kiu/kha/kha-bgt-subrack/kha-bgt-main/README.md

# kha-bgt-main

Main Power Preset Module

## Parts

Use [kha-bgt-generic-base](../../kha-bgt-misc/kha-bgt-generic-base/) as base

## Photos

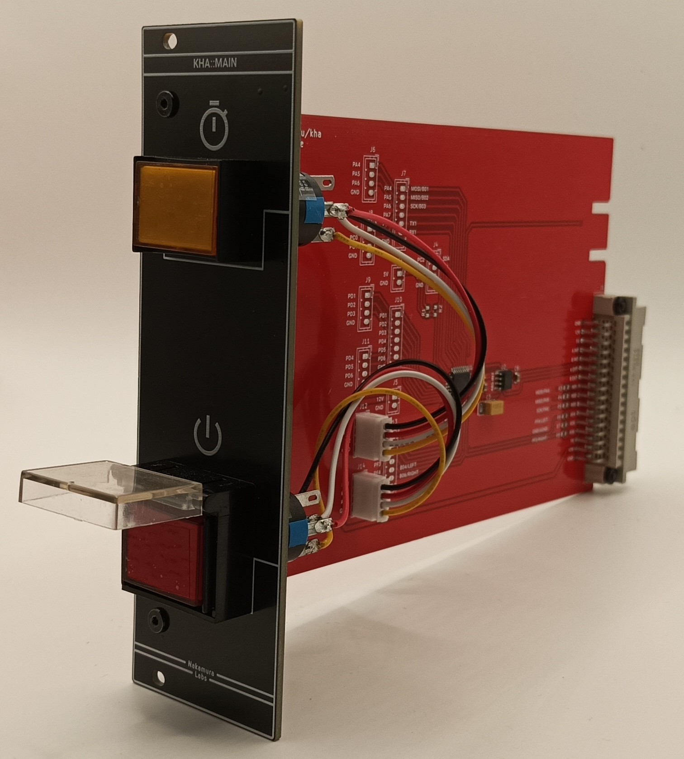
[picture p24: kha-bgt-subrack/kha-bgt-main/kha-bgt-main-photo.jpg]
