kiu/kha/kha-nodes/kha-relay-2x3/README.md

# kha-relay-2x3

Mains Power Relay

## Photos

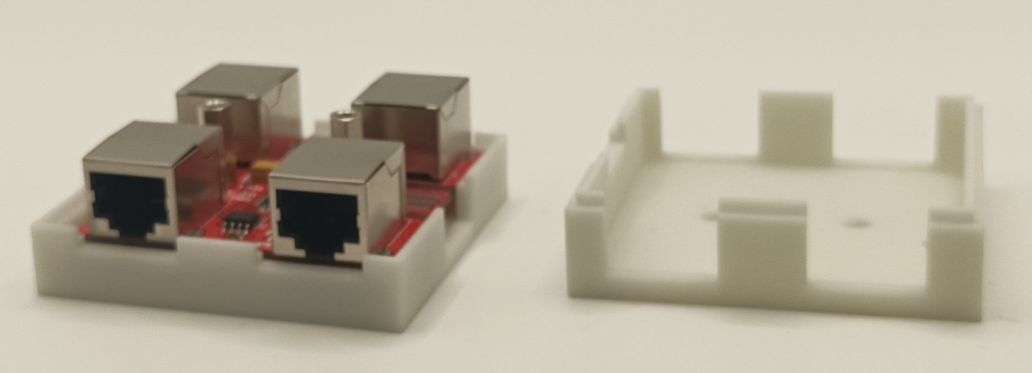
[picture p25: kha-nodes/kha-relay-2x3/kha-relay-2x3-node/kha-relay-2x3-node-photo.jpg]
