kiu/kha/kha-bgt-misc/kha-bgt-pwr/README.md

# kha-bgt-pwr

Subrack Power Module

Generating 5V out of 12V bus supply

## Photos

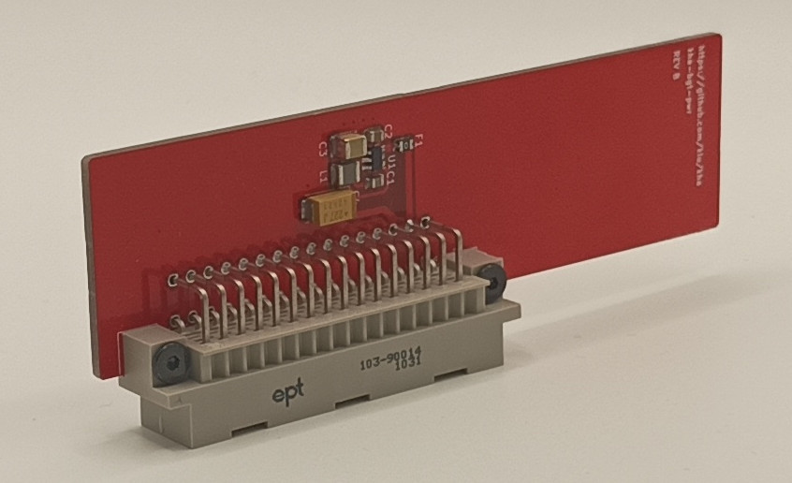
[picture p26: kha-bgt-misc/kha-bgt-pwr/kha-bgt-pwr-photo.jpg]


## Render

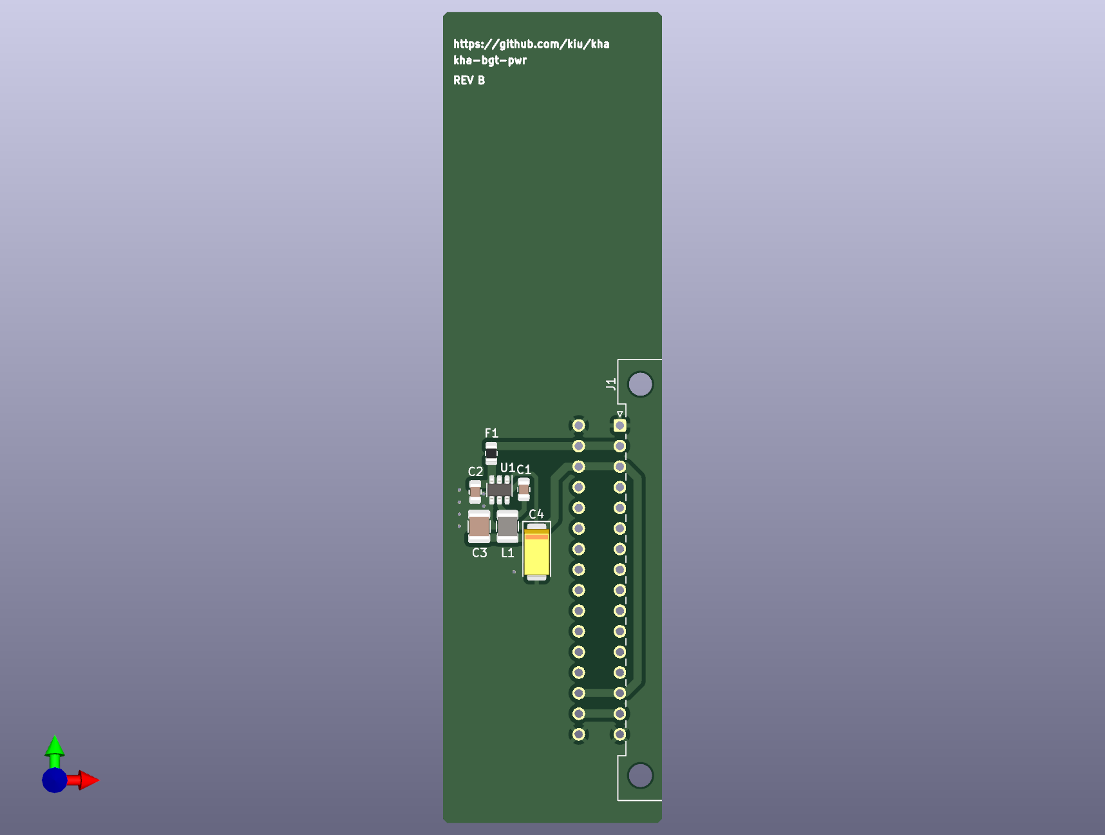
[picture p27: kha-bgt-misc/kha-bgt-pwr/kha-bgt-pwr-render-front.png]


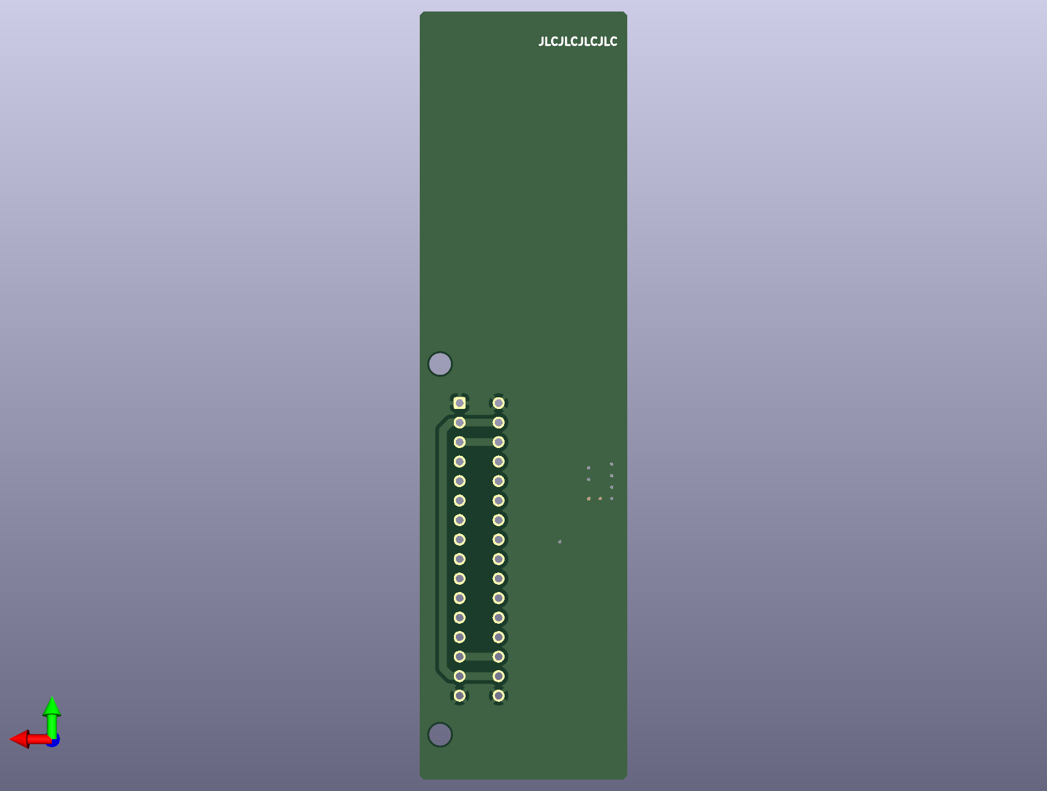
[picture p28: kha-bgt-misc/kha-bgt-pwr/kha-bgt-pwr-render-back.png]
