kiu/kha/kha-bgt-rack/kha-bgt-backplane/README.md

# kha-bgt-backplane

Rack backplane

## Photos

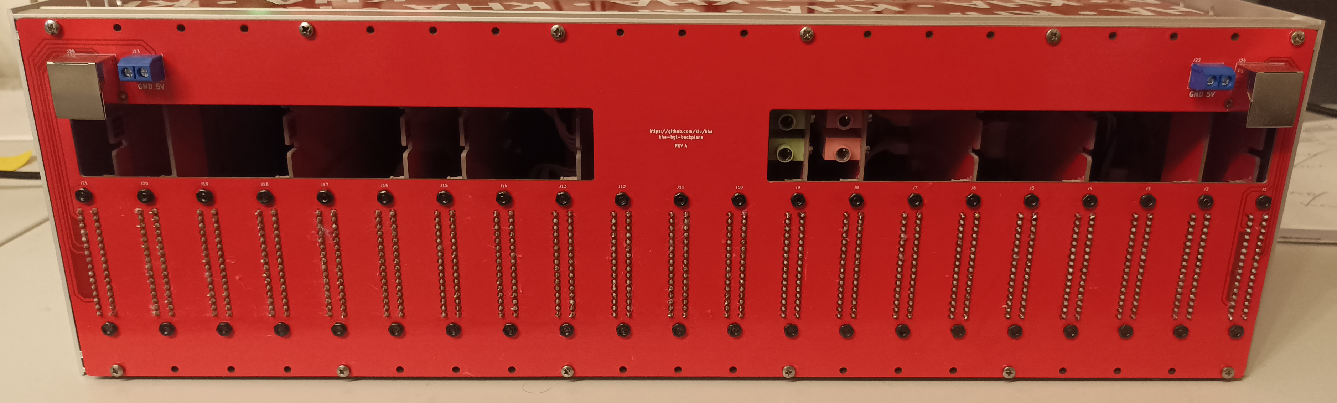
[picture p29: kha-bgt-rack/kha-bgt-backplane/kha-bgt-backplane-photo.jpg]


## Render

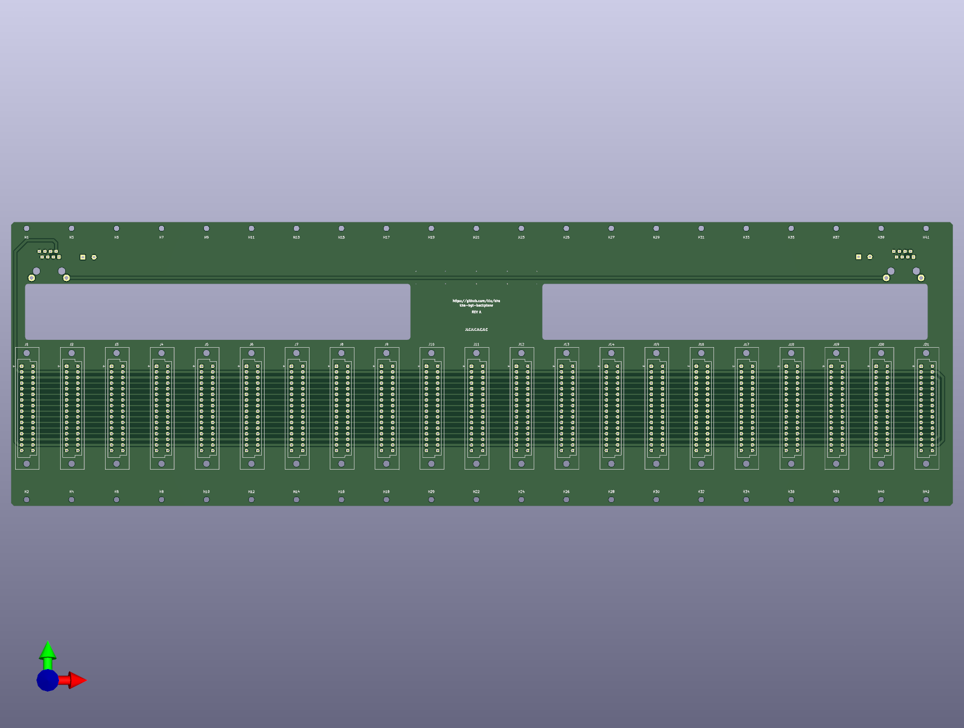
[picture p30: kha-bgt-rack/kha-bgt-backplane/kha-bgt-backplane-render-front.png]


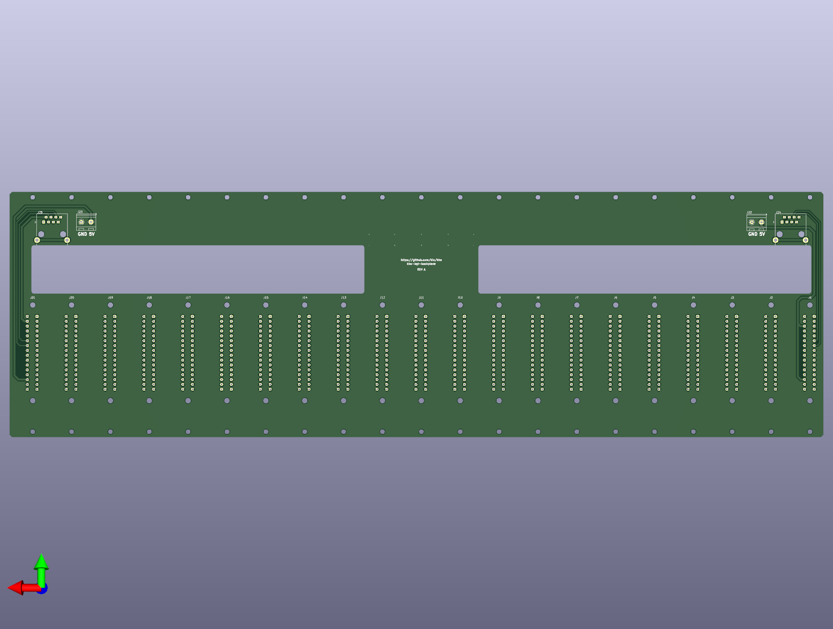
[picture p31: kha-bgt-rack/kha-bgt-backplane/kha-bgt-backplane-render-back.png]


## Todo

- Remove 2nd internal RS-485 bus, never used
- Add silkscreen for bus
- Use bigger font for silkscreen
- Add screw terminal for 12V injection
- Built-in 5V stepdown on backplane
- Backplane should be symmetric
