kiu/kha/kha-nodes/kha-pwr-rj45/README.md

# kha-pwr-rj45

POE Power Inject

## Photos

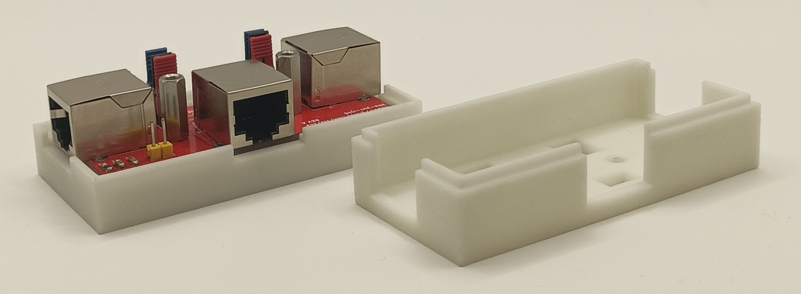
[picture p32: kha-nodes/kha-pwr-rj45/kha-pwr-rj45-photo.jpg]


## Render

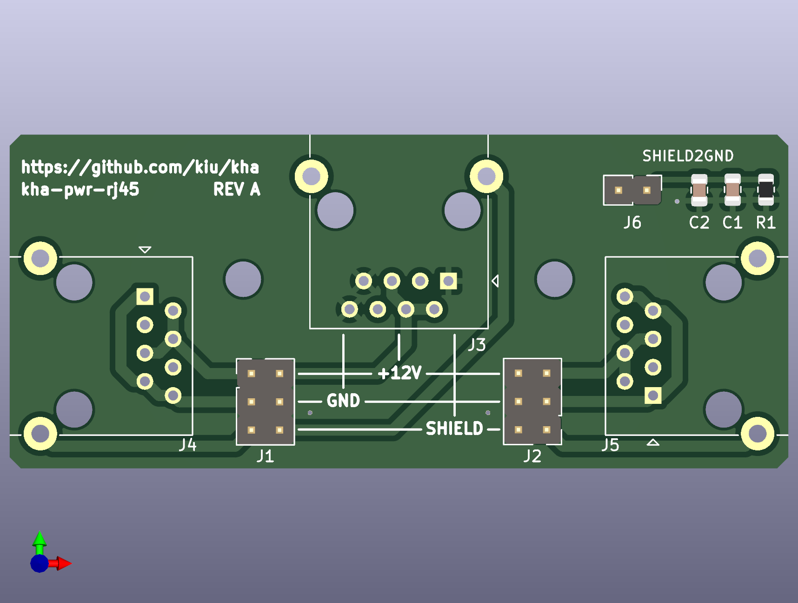
[picture p33: kha-nodes/kha-pwr-rj45/kha-pwr-rj45-render-front.png]


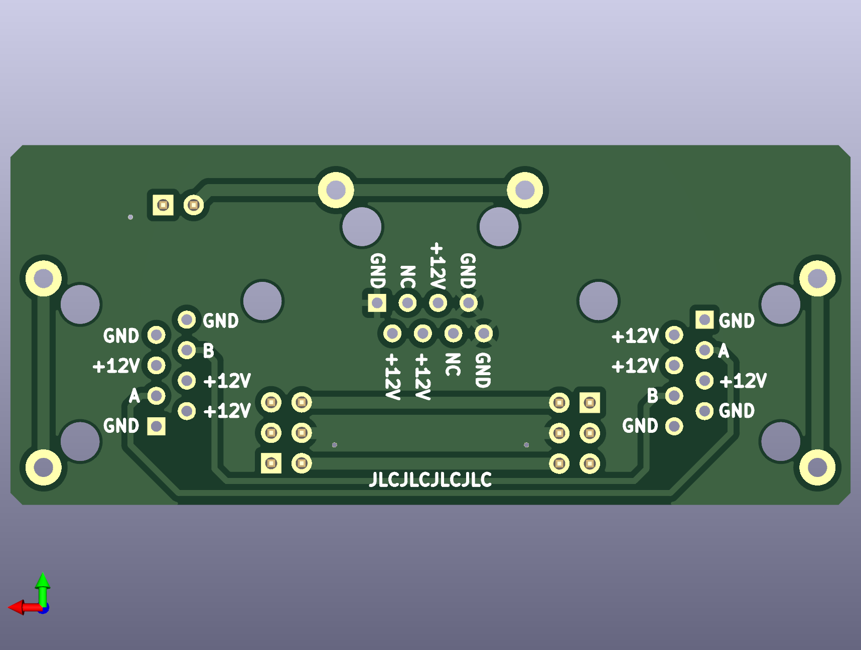
[picture p34: kha-nodes/kha-pwr-rj45/kha-pwr-rj45-render-back.png]
