kiu/kha/kha-nodes/kha-pwr-terminal/README.md

# kha-pwr-terminal

Screw Terminal Power Inject

## Photos

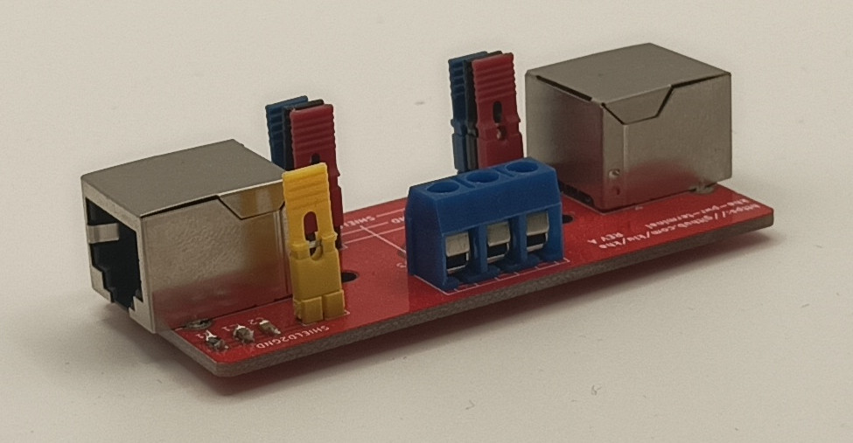
[picture p35: kha-nodes/kha-pwr-terminal/kha-pwr-terminal-photo.jpg]


## Render

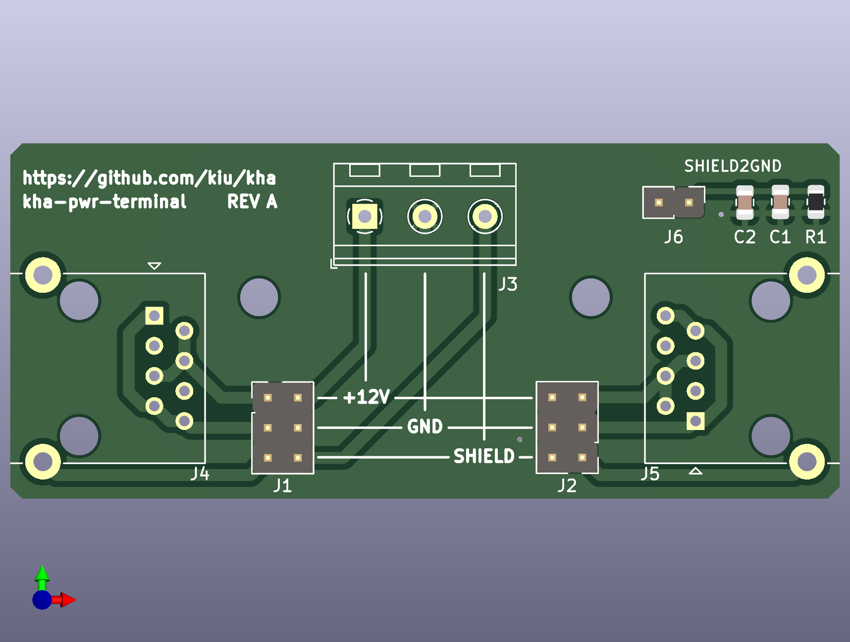
[picture p36: kha-nodes/kha-pwr-terminal/kha-pwr-terminal-render-front.png]


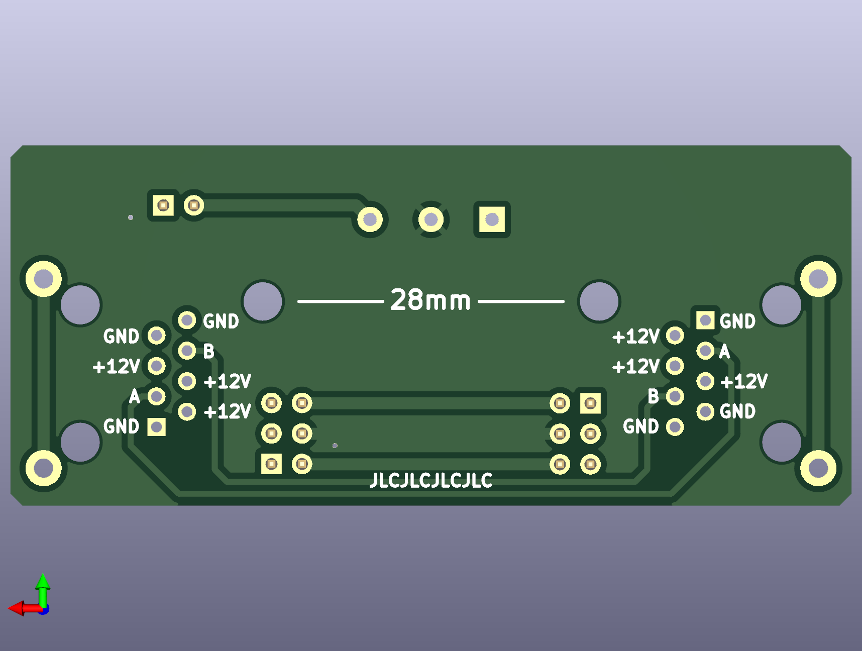
[picture p37: kha-nodes/kha-pwr-terminal/kha-pwr-terminal-render-back.png]
