kiu/kha/tools/kha-userrow/README.md

# kha-userrow

Device provisioning information stored in AVR64 userrow

- Board Type
- Board Revision
- Device Address
- Device Group
- Data (currently unused)
