kiu/kha/kha-bgt-rack/kha-bgt-cover/README.md

# kha-bgt-cover

Rack Cover Plate

## Render

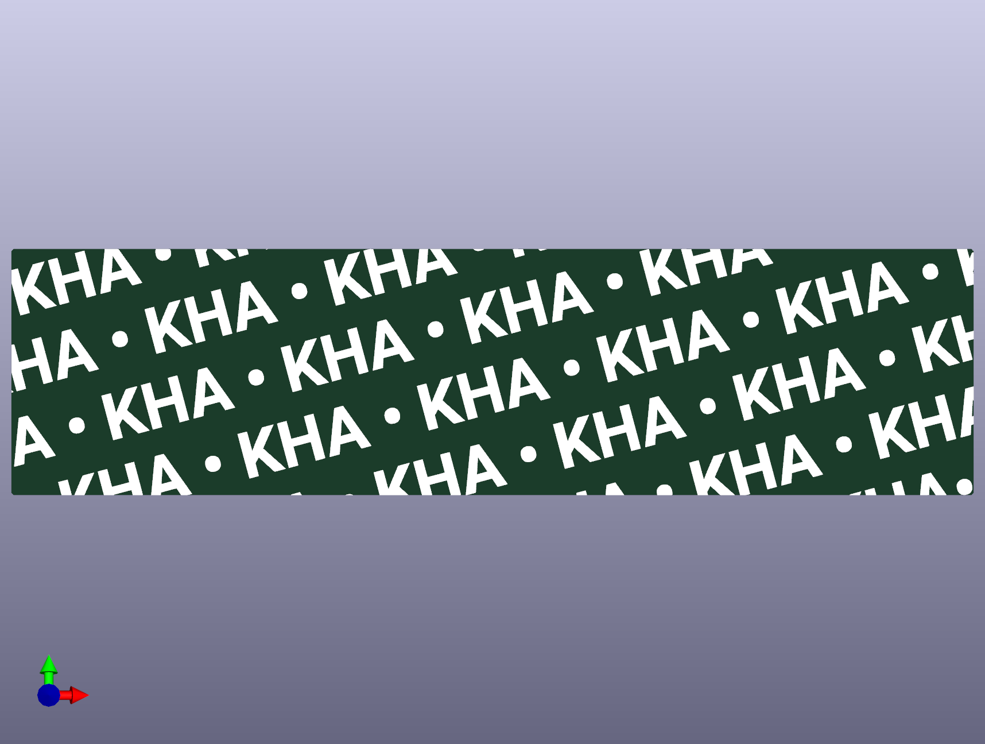
[picture p38: kha-bgt-rack/kha-bgt-cover/kha-bgt-cover-render-front.png]


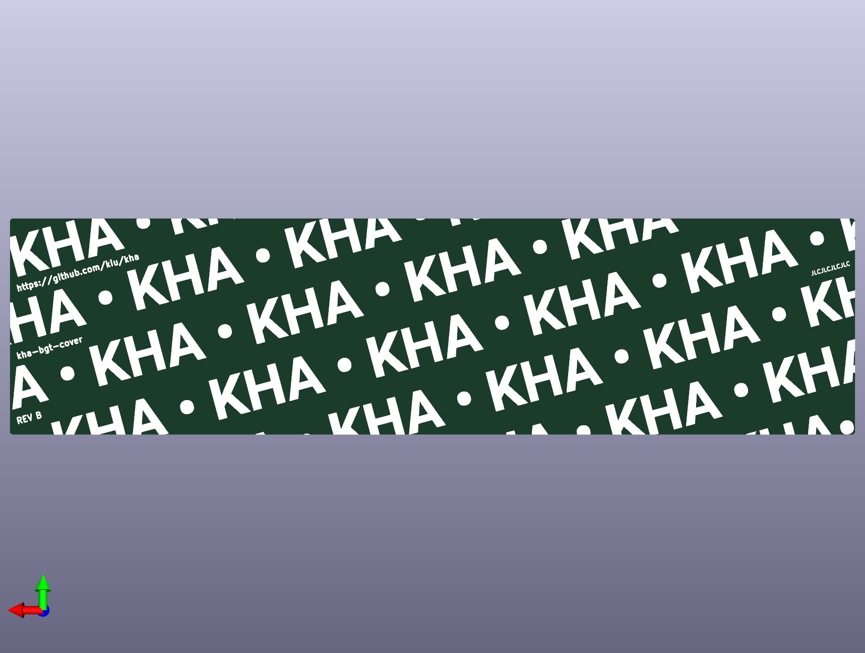
[picture p39: kha-bgt-rack/kha-bgt-cover/kha-bgt-cover-render-back.png]
