kiu/kha/kha-bgt-rack/kha-bgt-spacer/README.md

# kha-bgt-spacer

Rack Spacer

Double stacked spacer needed to provide z space for backplane

## Render

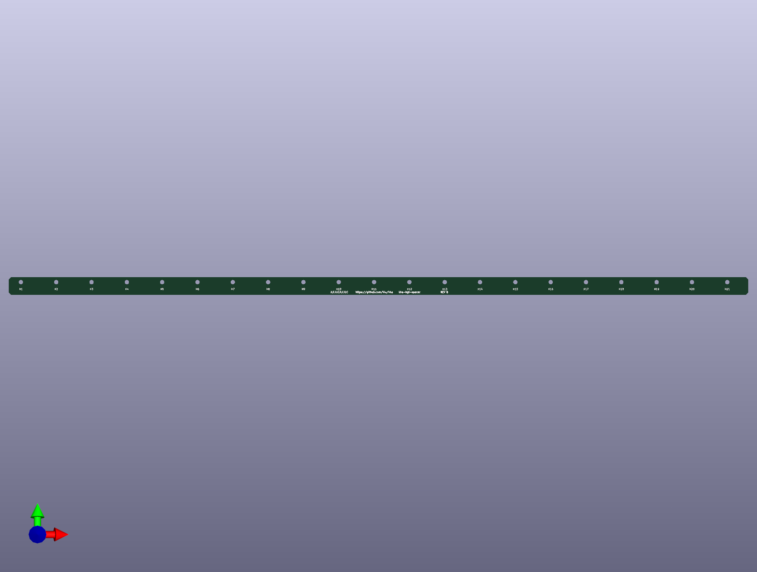
[picture p40: kha-bgt-rack/kha-bgt-spacer/kha-bgt-spacer-render-front.png]


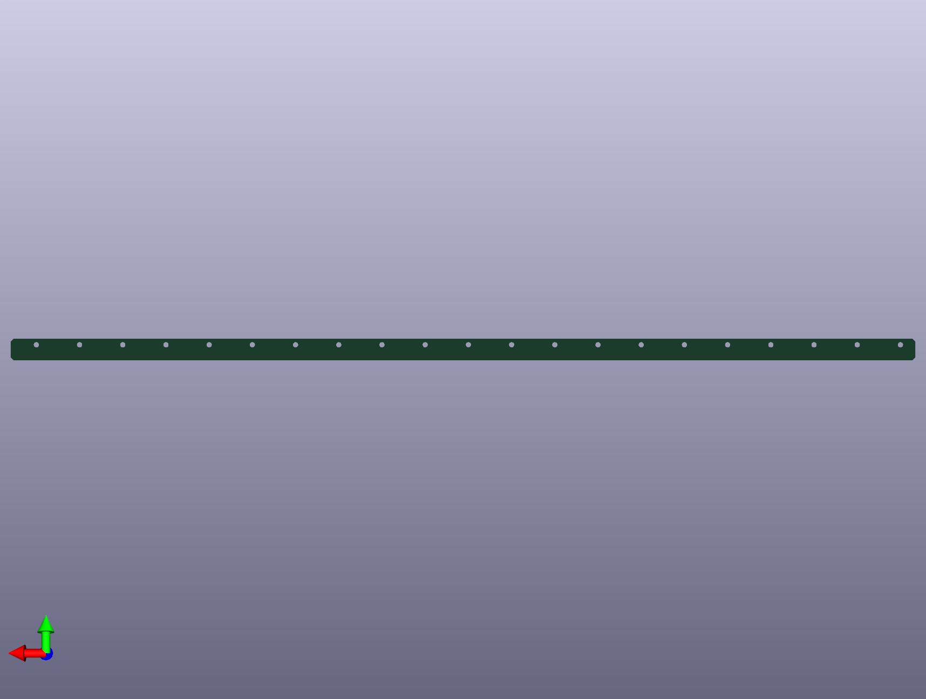
[picture p41: kha-bgt-rack/kha-bgt-spacer/kha-bgt-spacer-render-back.png]
