kiu/kha/kha-bgt-misc/kha-bgt-generic-4btn-sub/README.md

# kha-bgt-generic-4btn-sub

Generic Four Push Button Mounting PCB

## Render

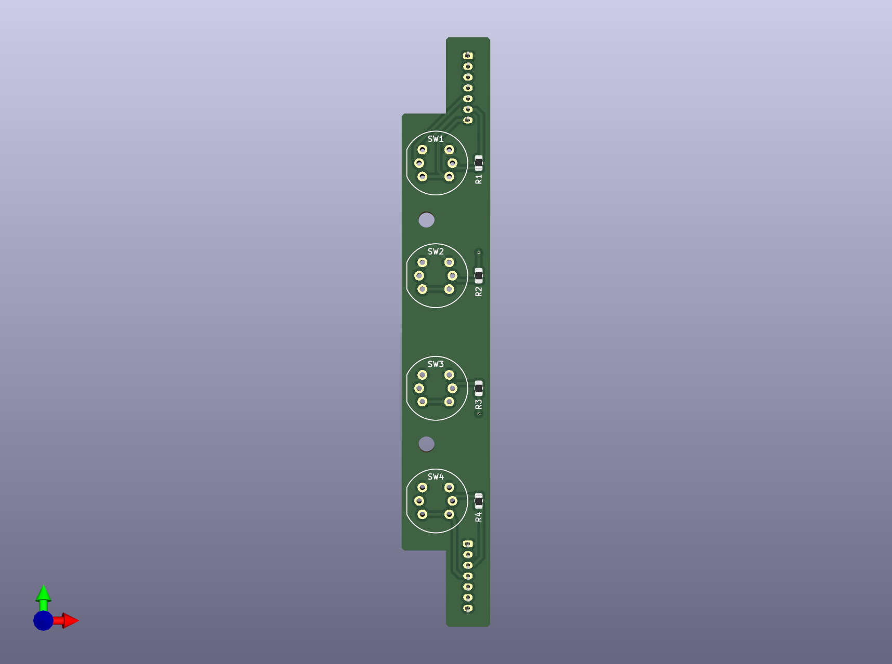
[picture p42: kha-bgt-misc/kha-bgt-generic-4btn-sub/kha-bgt-generic-4btn-sub-render-front.png]


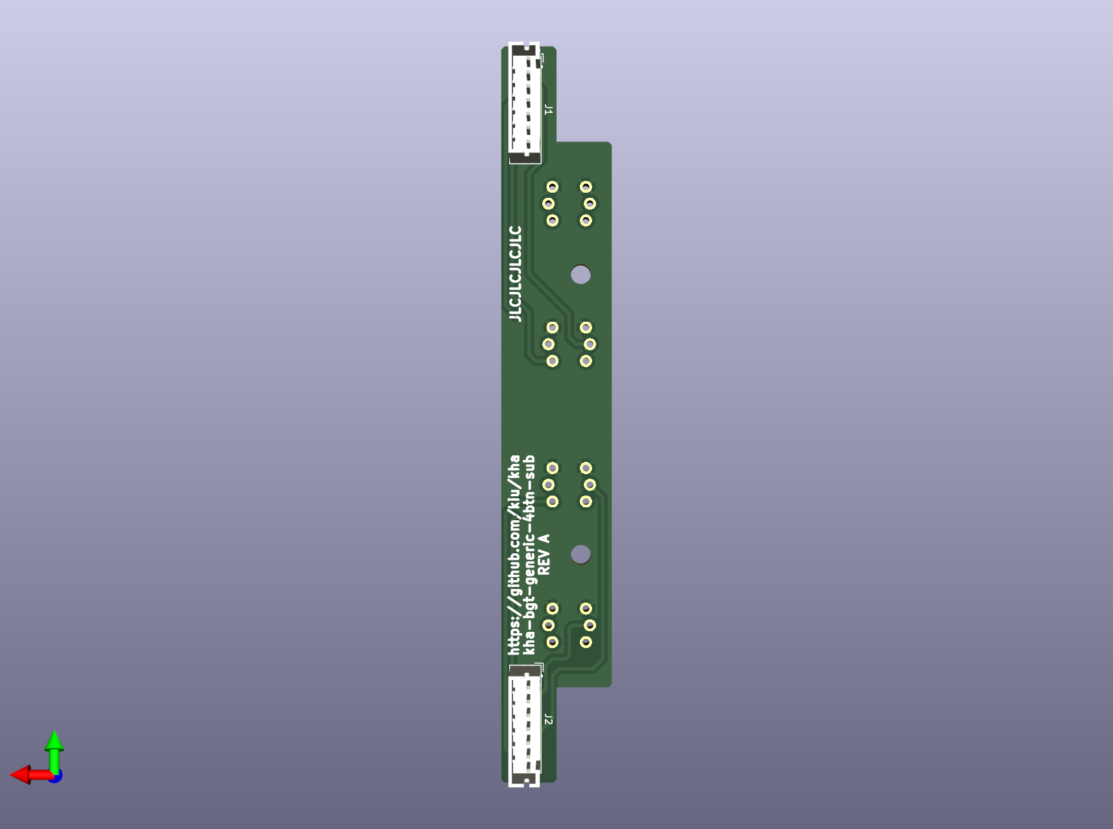
[picture p43: kha-bgt-misc/kha-bgt-generic-4btn-sub/kha-bgt-generic-4btn-sub-render-back.png]
