kiu/kha/kha-bgt-misc/kha-bgt-generic-rotary-encoder/README.md

# kha-bgt-generic-rotary-encoder

Generic Single Rotary Encoder Mounting PCB

## Render

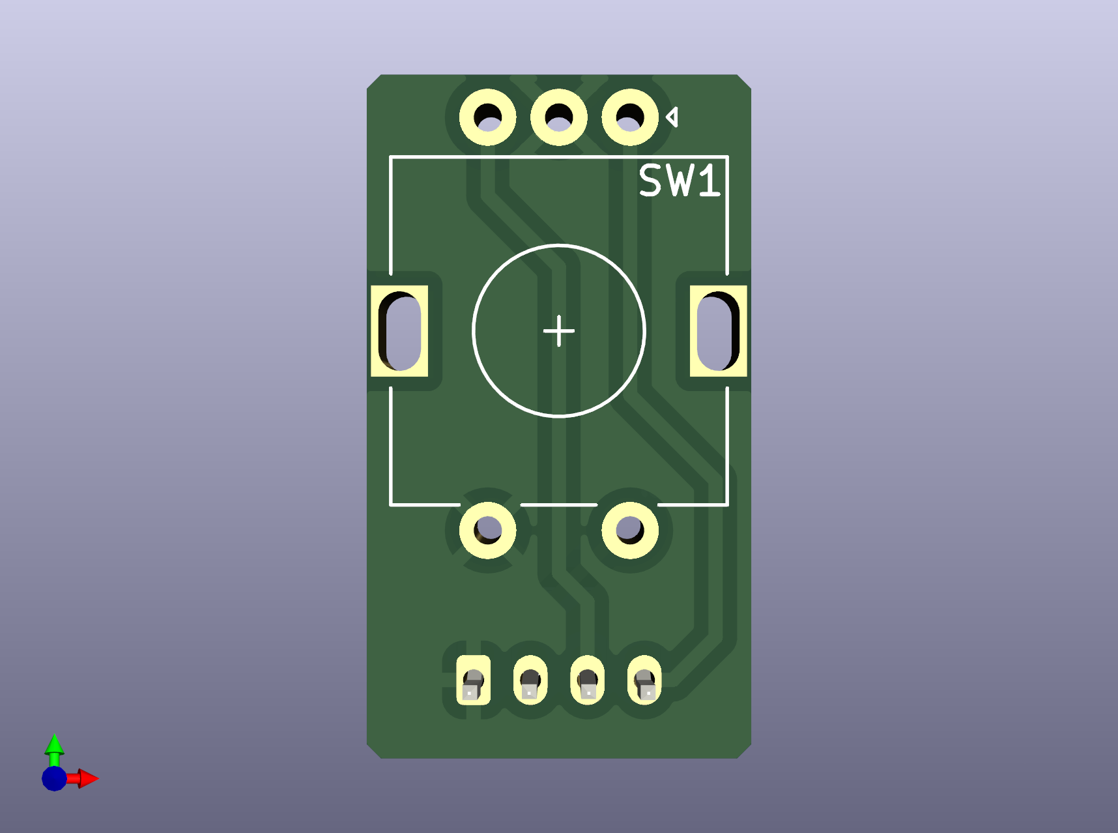
[picture p44: kha-bgt-misc/kha-bgt-generic-rotary-encoder/kha-bgt-generic-rotary-encoder-render-front.png]


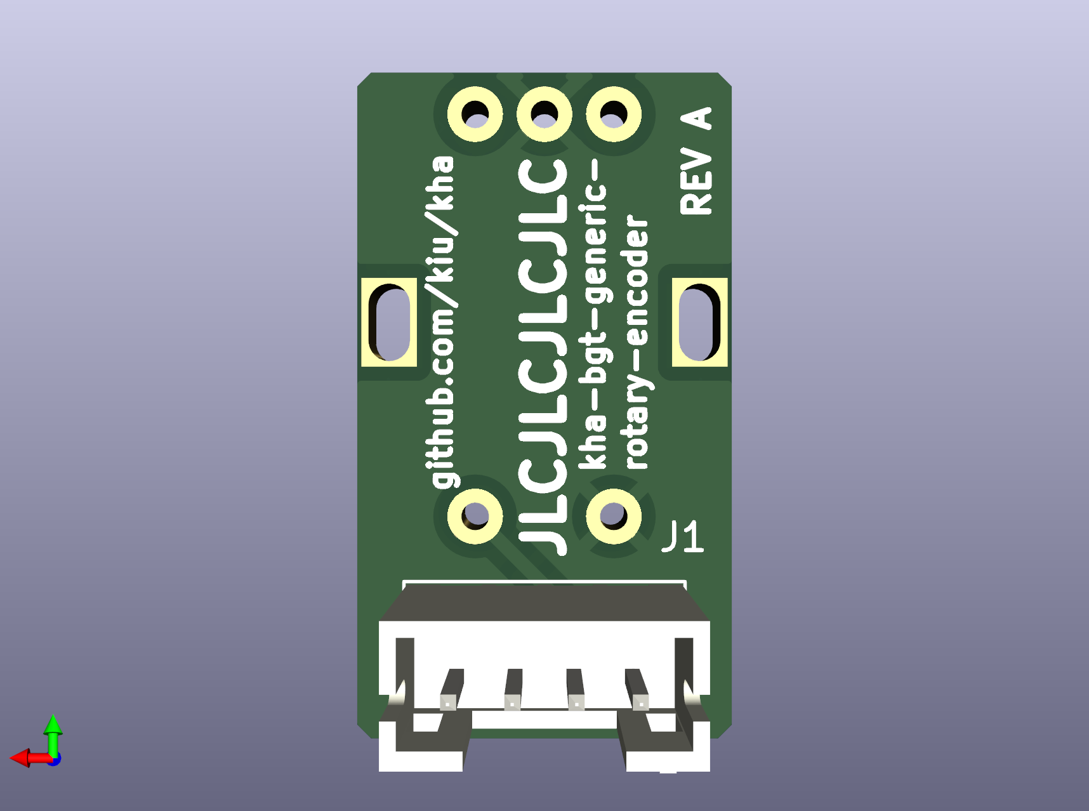
[picture p45: kha-bgt-misc/kha-bgt-generic-rotary-encoder/kha-bgt-generic-rotary-encoder-render-back.png]
