kiu/kha/kha-bgt-misc/kha-bgt-template/README.md

# kha-bgt-template

Templates to be used for creating custom front panels and base pcbs

## Render

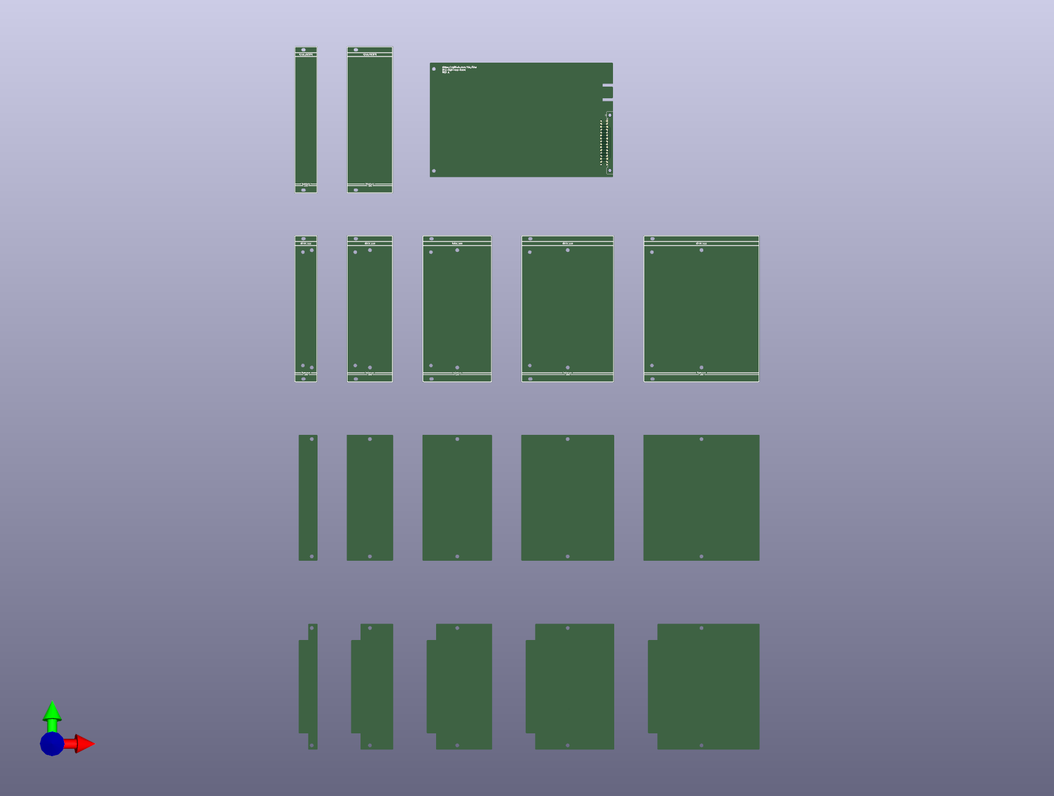
[picture p46: kha-bgt-misc/kha-bgt-template/kha-bgt-template-render-front.png]


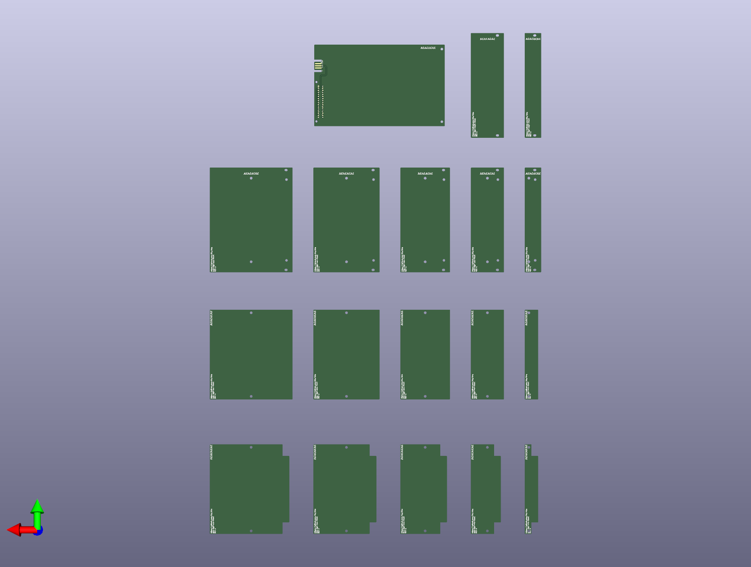
[picture p47: kha-bgt-misc/kha-bgt-template/kha-bgt-template-render-back.png]
