kiu/kha/kha-bgt-subrack/kha-bgt-strip/kha-bgt-strip-front/README.md

# kha-bgt-strip-front

LED Strip Front Panel

## Render

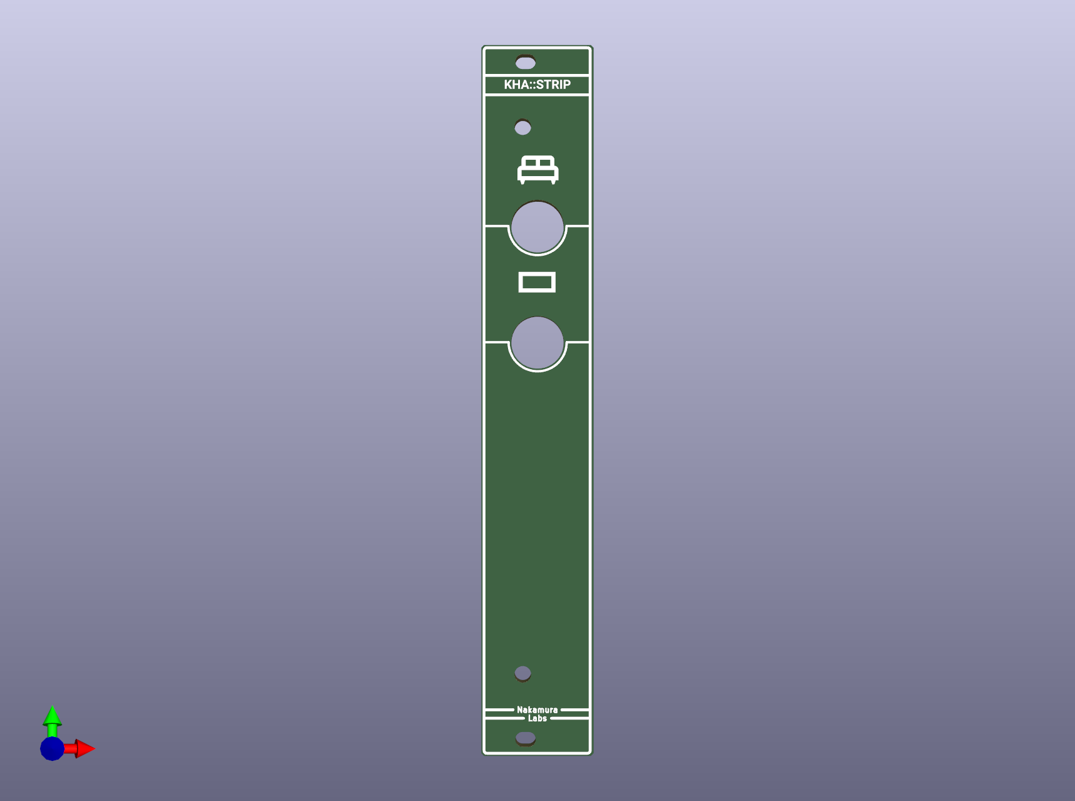
[picture p48: kha-bgt-subrack/kha-bgt-strip/kha-bgt-strip-front/kha-bgt-strip-front-render-front.png]


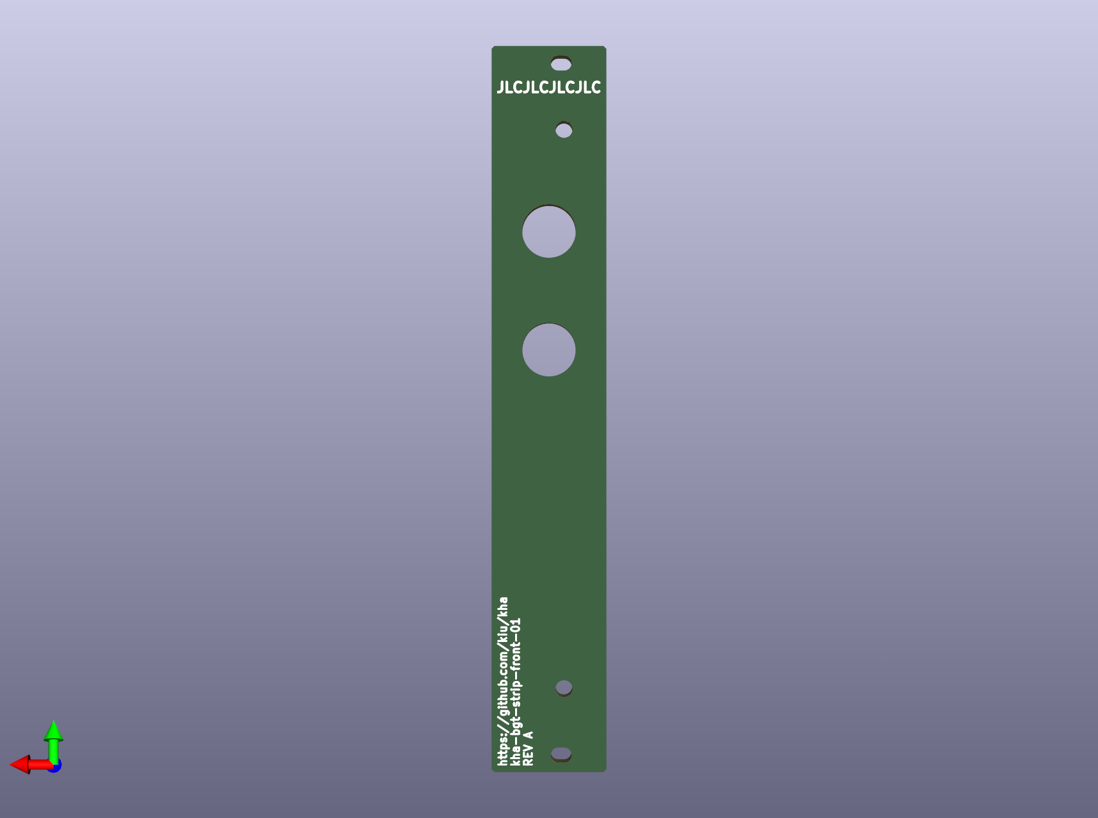
[picture p49: kha-bgt-subrack/kha-bgt-strip/kha-bgt-strip-front/kha-bgt-strip-front-render-back.png]
