kiu/kha/kha-bgt-subrack/kha-bgt-power/kha-bgt-power-front-04-desk/README.md

# kha-bgt-power-front-04-desk

Mains Power Switching Module Front Panel Use Case 04

## Render

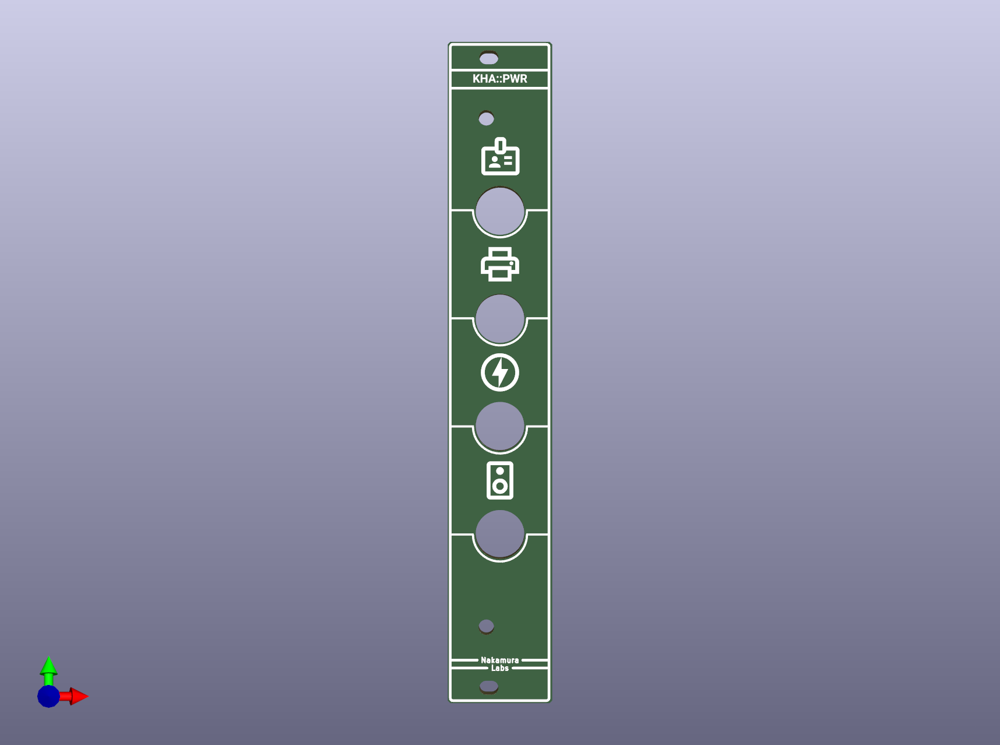
[picture p50: kha-bgt-subrack/kha-bgt-power/kha-bgt-power-front-04-desk/kha-bgt-power-front-04-desk-render-front.png]


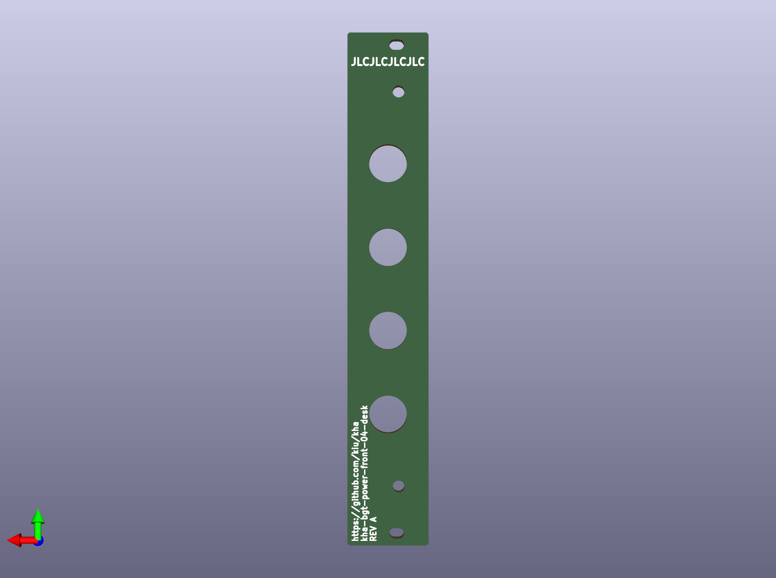
[picture p51: kha-bgt-subrack/kha-bgt-power/kha-bgt-power-front-04-desk/kha-bgt-power-front-04-desk-render-back.png]
