kiu/kha/kha-bgt-subrack/kha-bgt-audio/kha-bgt-audio-base/README.md

# kha-bgt-audio-base

Audio Switching Module Base

- 2x TRS (back)
- 1x TRS (front)
- 1x Bluetooth

## Render

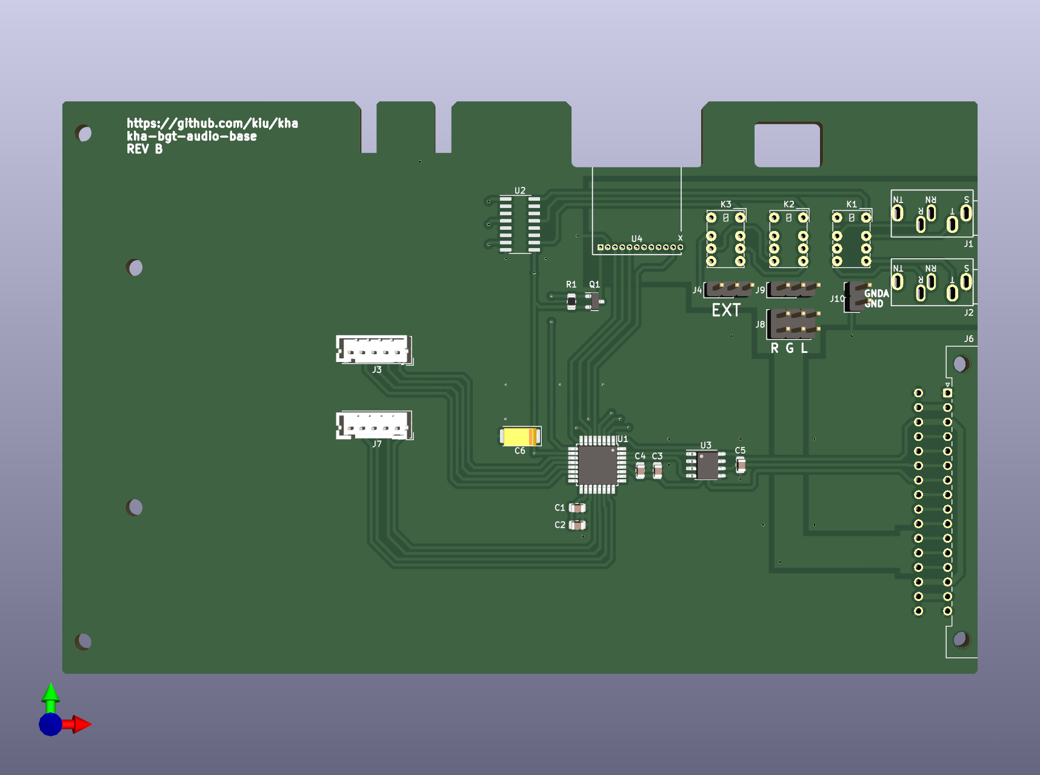
[picture p52: kha-bgt-subrack/kha-bgt-audio/kha-bgt-audio-base/kha-bgt-audio-base-render-front.png]


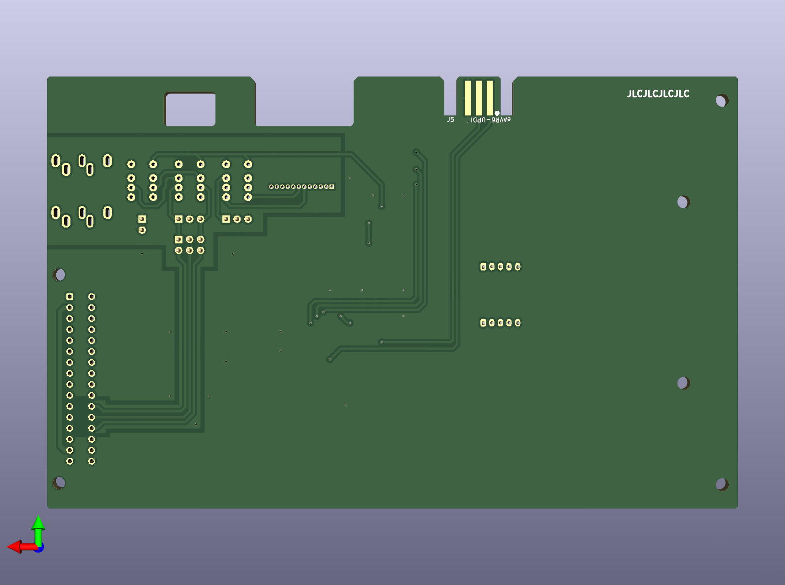
[picture p53: kha-bgt-subrack/kha-bgt-audio/kha-bgt-audio-base/kha-bgt-audio-base-render-back.png]
