kiu/kha/kha-bgt-subrack/kha-bgt-audio/kha-bgt-audio-front-in/README.md

# kha-bgt-audio-front-in

Audio Switching Module Input Front Panel

## Render

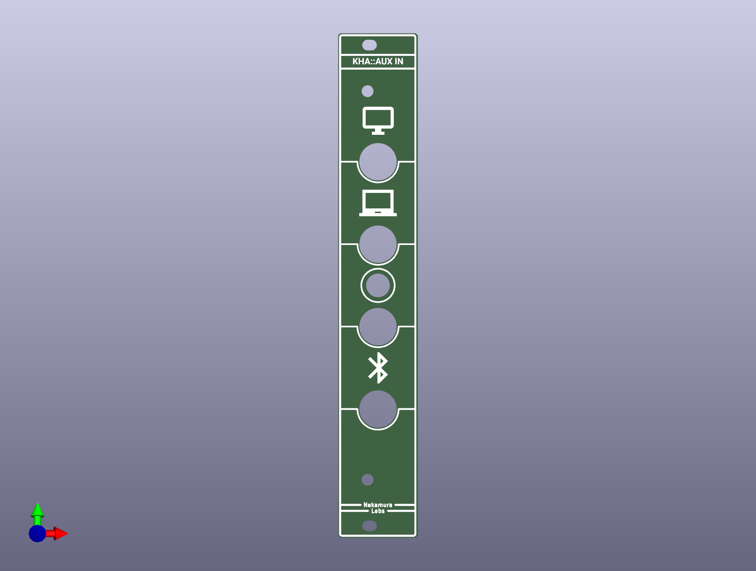
[picture p54: kha-bgt-subrack/kha-bgt-audio/kha-bgt-audio-front-in/kha-bgt-audio-front-in-render-front.png]


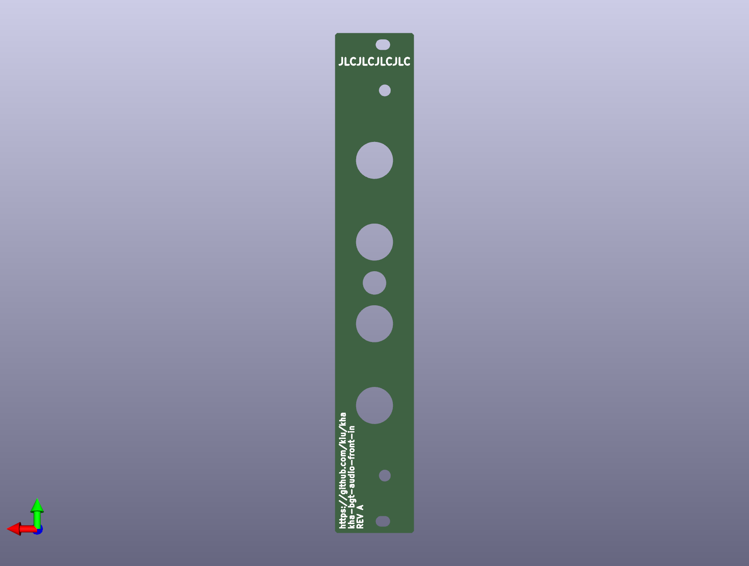
[picture p55: kha-bgt-subrack/kha-bgt-audio/kha-bgt-audio-front-in/kha-bgt-audio-front-in-render-back.png]
