kiu/kha/kha-bgt-subrack/kha-bgt-audio/kha-bgt-audio-front-out/README.md

# kha-bgt-audio-front-out

Audio Switching Module Output Front Panel

## Render

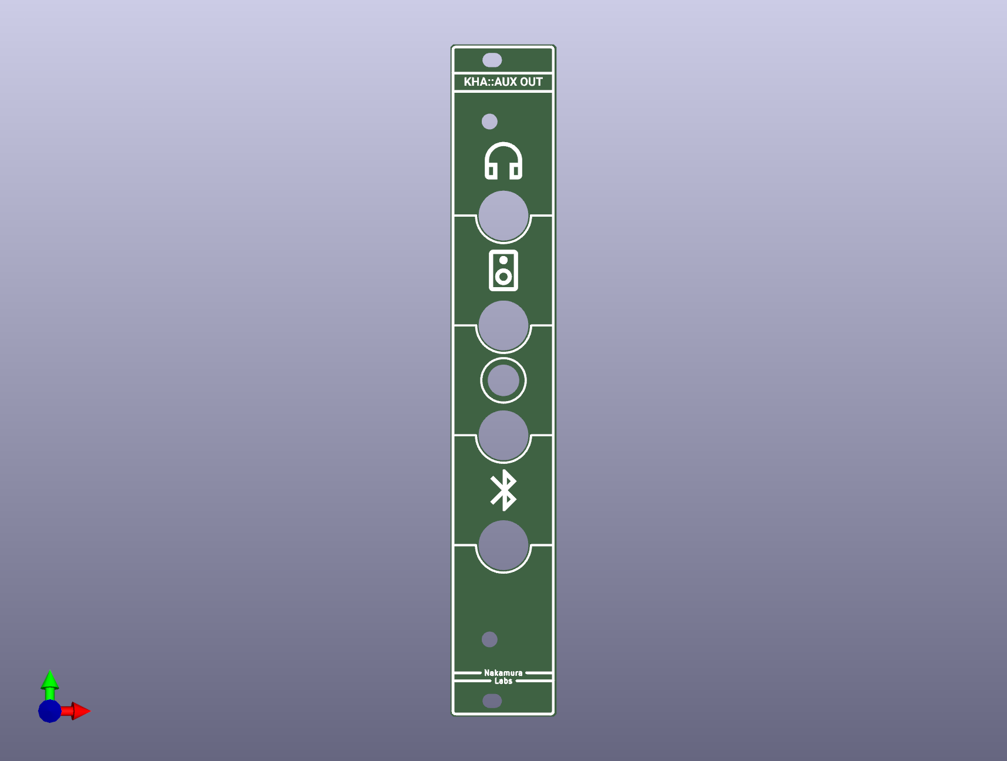
[picture p56: kha-bgt-subrack/kha-bgt-audio/kha-bgt-audio-front-out/kha-bgt-audio-front-out-render-front.png]


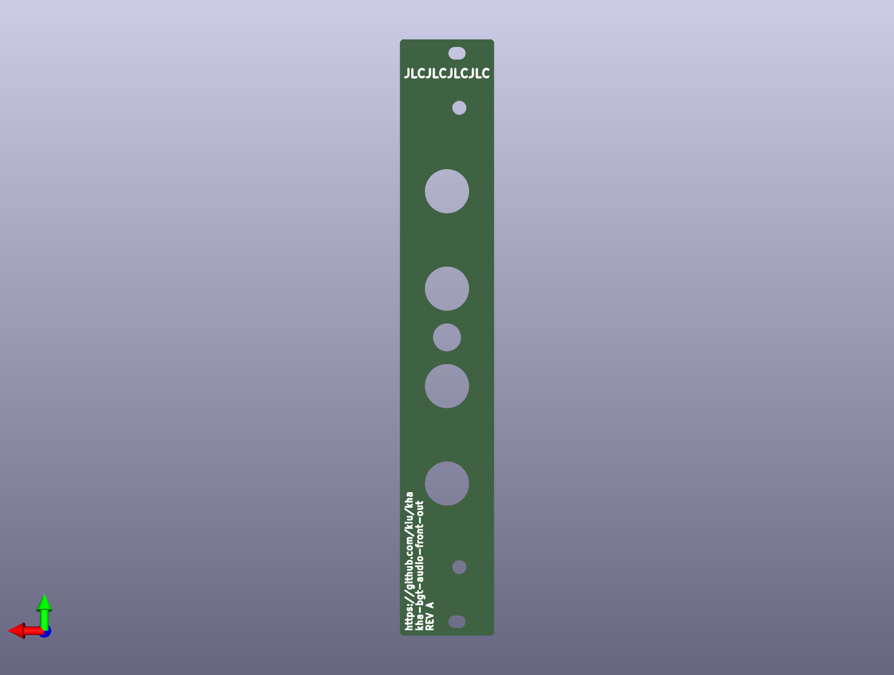
[picture p57: kha-bgt-subrack/kha-bgt-audio/kha-bgt-audio-front-out/kha-bgt-audio-front-out-render-back.png]
