kiu/kha/kha-bgt-subrack/kha-bgt-audio/kha-bgt-audio-sub/README.md

# kha-bgt-audio-sub

Audio Switching Module Four Push Button and TRS Mounting PCB

## Render

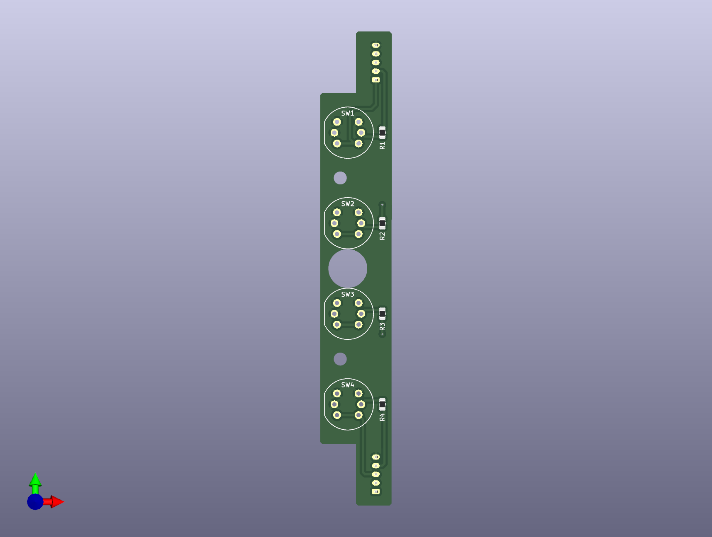
[picture p58: kha-bgt-subrack/kha-bgt-audio/kha-bgt-audio-sub/kha-bgt-audio-sub-render-front.png]


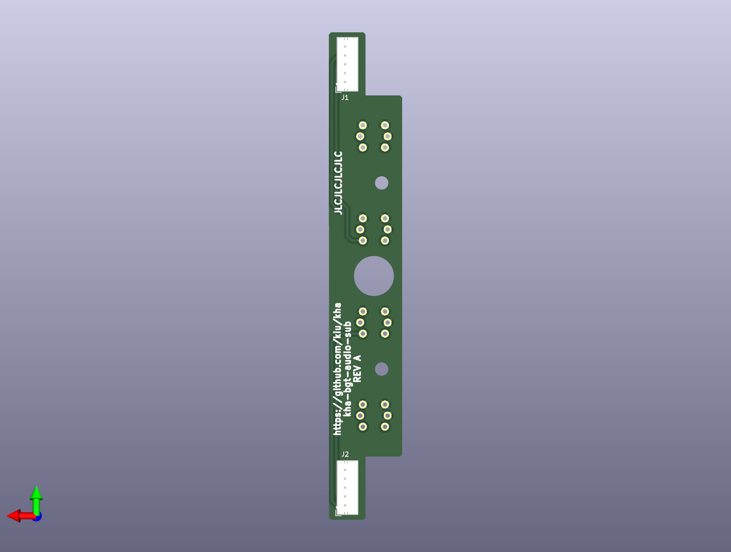
[picture p59: kha-bgt-subrack/kha-bgt-audio/kha-bgt-audio-sub/kha-bgt-audio-sub-render-back.png]
