kiu/kha/kha-bgt-subrack/kha-bgt-main/kha-bgt-main-front/README.md

# kha-bgt-main-front

Main Power Preset Module Front Panel

## Render

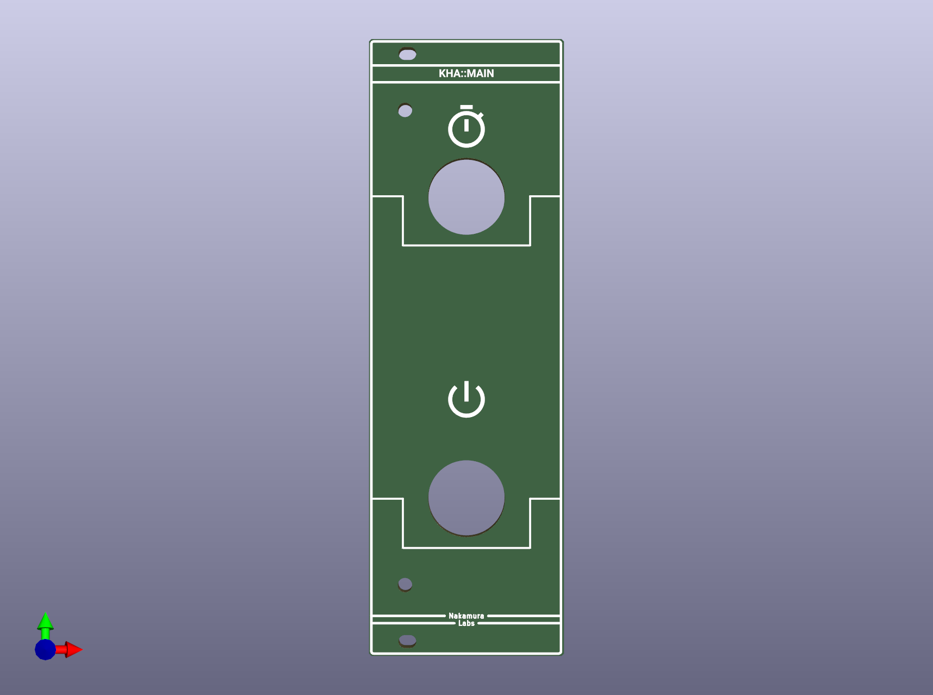
[picture p60: kha-bgt-subrack/kha-bgt-main/kha-bgt-main-front/kha-bgt-main-front-render-front.png]


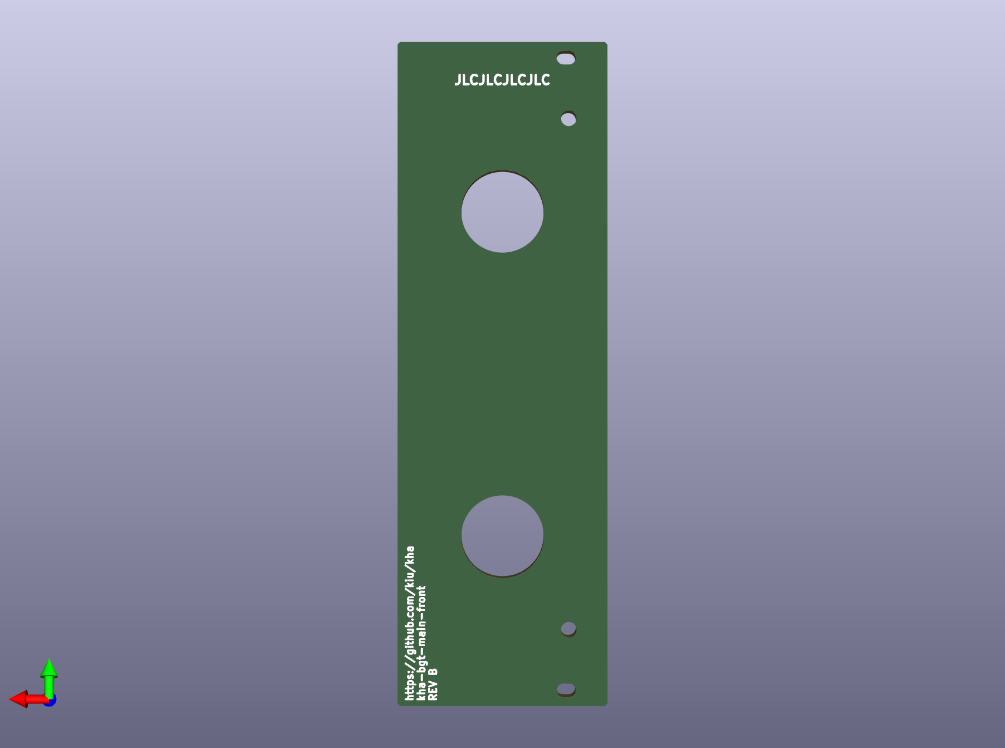
[picture p61: kha-bgt-subrack/kha-bgt-main/kha-bgt-main-front/kha-bgt-main-front-render-back.png]
