kiu/kha/kha-bgt-subrack/kha-bgt-power/kha-bgt-power-base/README.md

# kha-bgt-power-base

Mains Power Switching Module Base

## Render

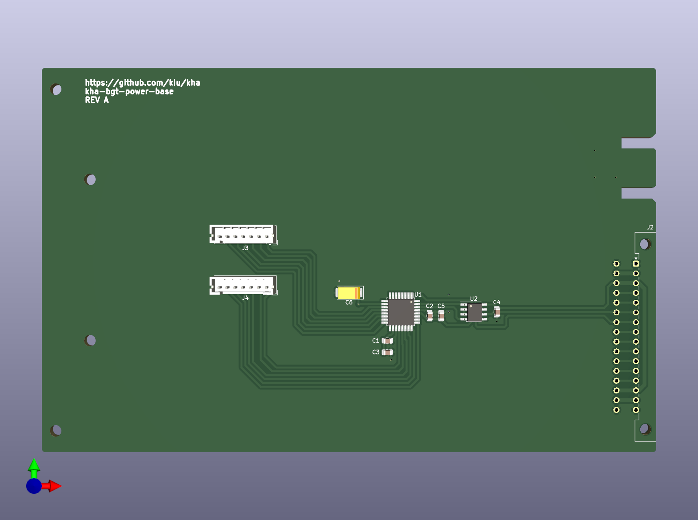
[picture p62: kha-bgt-subrack/kha-bgt-power/kha-bgt-power-base/kha-bgt-power-base-render-front.png]


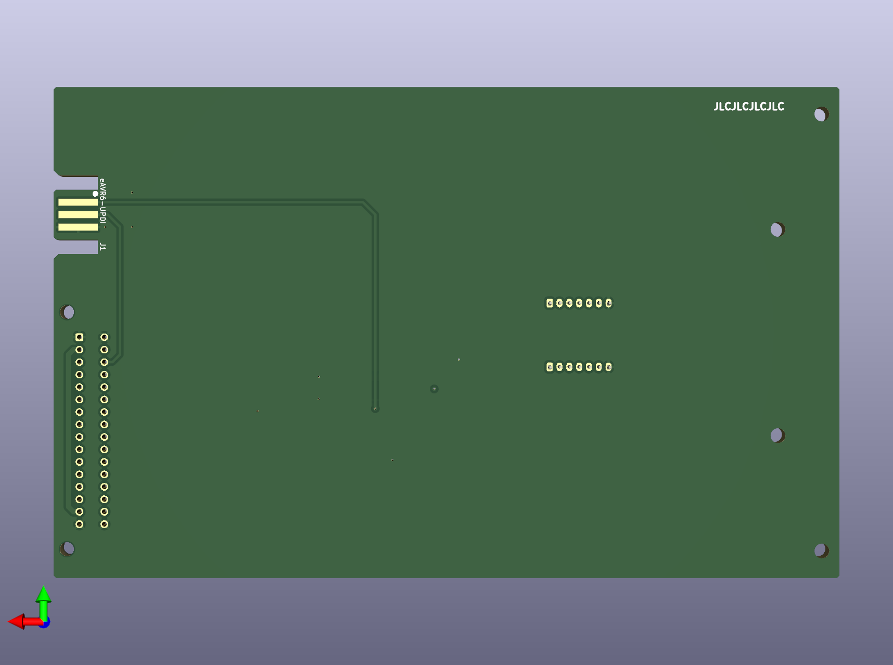
[picture p63: kha-bgt-subrack/kha-bgt-power/kha-bgt-power-base/kha-bgt-power-base-render-back.png]
