kiu/kha/kha-bgt-subrack/kha-bgt-power/kha-bgt-power-front-01-light/README.md

# kha-bgt-power-front-01-light

Mains Power Switching Module Front Panel Use Case 01

## Render

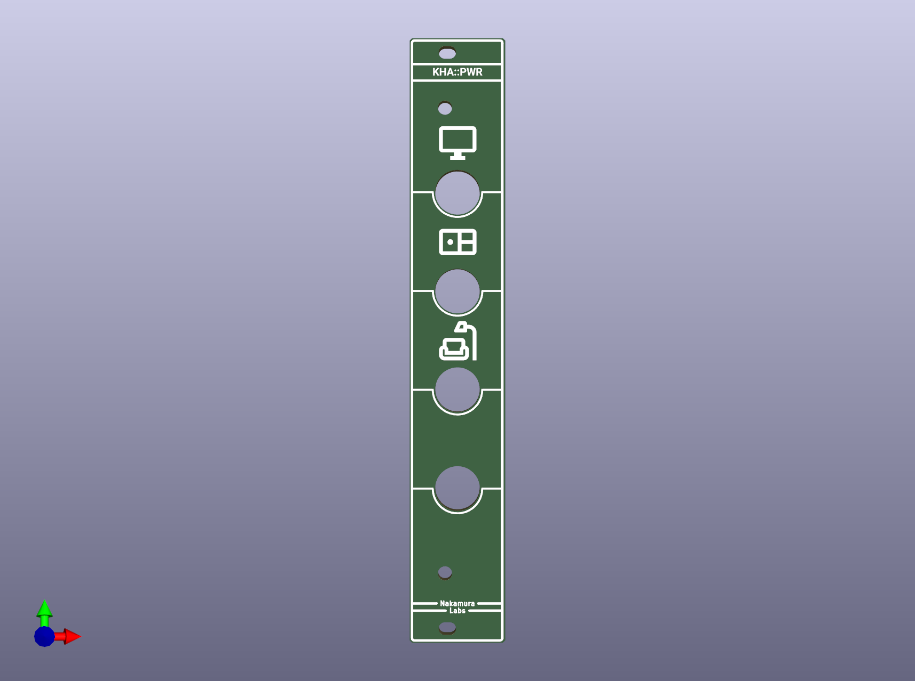
[picture p64: kha-bgt-subrack/kha-bgt-power/kha-bgt-power-front-01-light/kha-bgt-power-front-01-light-render-front.png]


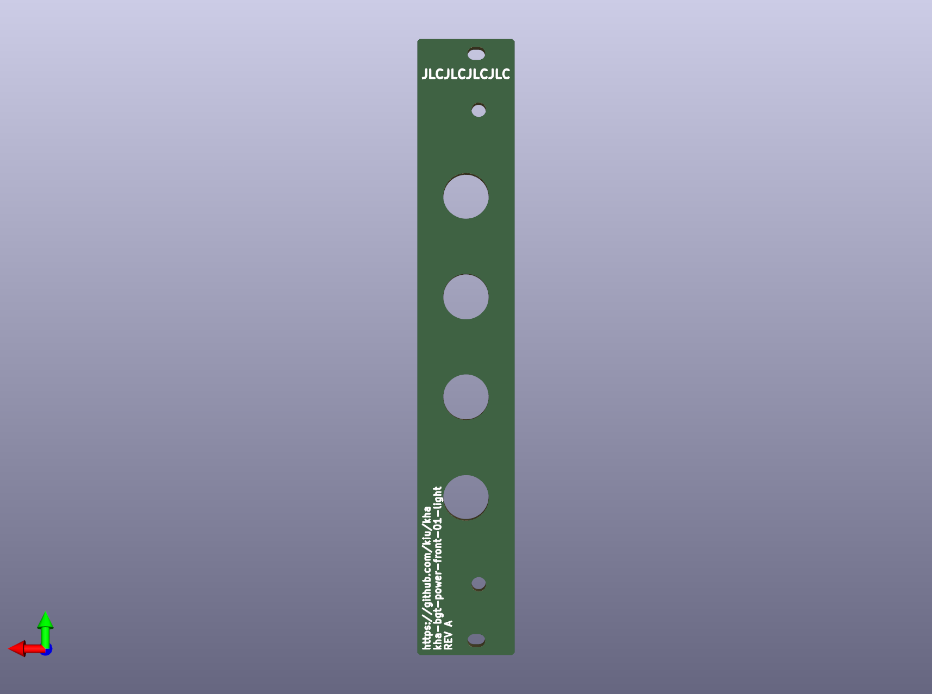
[picture p65: kha-bgt-subrack/kha-bgt-power/kha-bgt-power-front-01-light/kha-bgt-power-front-01-light-render-back.png]
