kiu/kha/kha-bgt-subrack/kha-bgt-power/kha-bgt-power-front-02-tinker/README.md

# kha-bgt-power-front-02-tinker

Mains Power Switching Module Front Panel Use Case 02

## Render

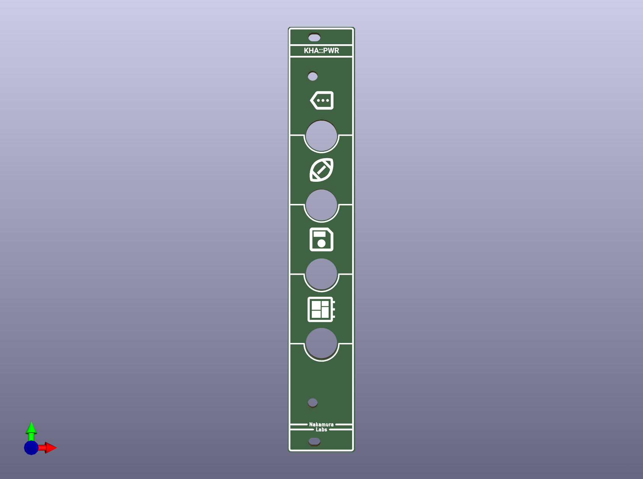
[picture p66: kha-bgt-subrack/kha-bgt-power/kha-bgt-power-front-02-tinker/kha-bgt-power-front-02-tinker-render-front.png]


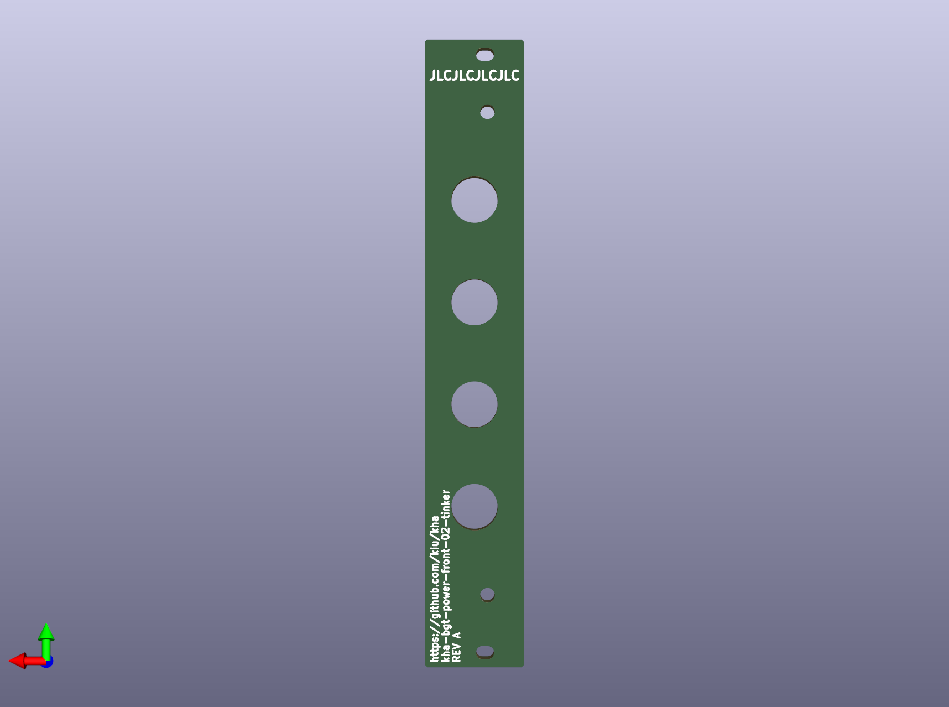
[picture p67: kha-bgt-subrack/kha-bgt-power/kha-bgt-power-front-02-tinker/kha-bgt-power-front-02-tinker-render-back.png]
