kiu/kha/kha-bgt-subrack/kha-bgt-power/kha-bgt-power-front-03-misc/README.md

# kha-bgt-power-front-03-misc

Mains Power Switching Module Front Panel Use Case 03

## Render

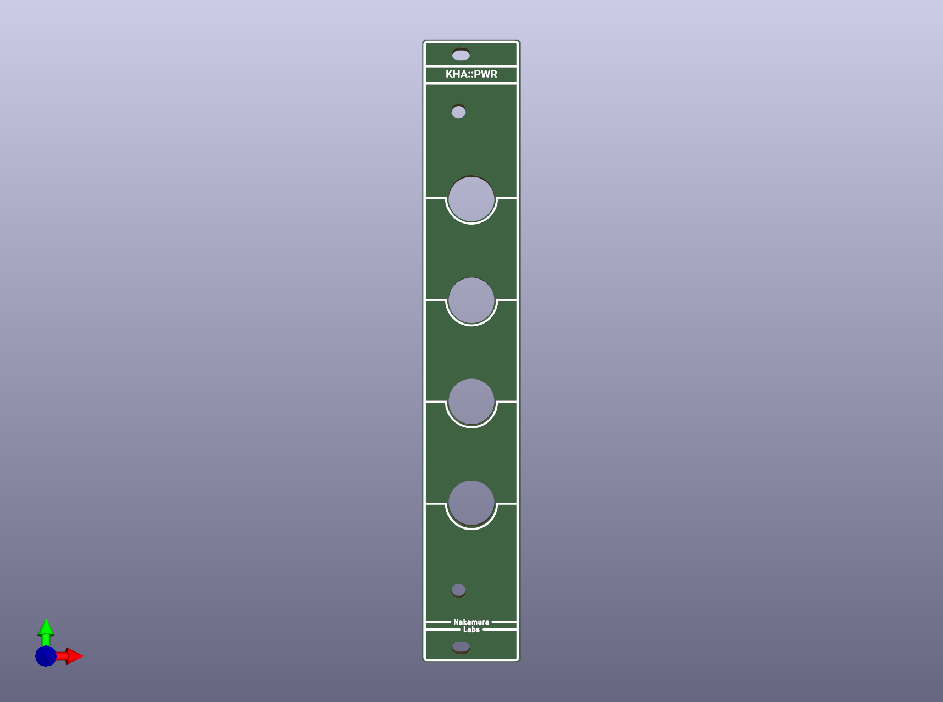
[picture p68: kha-bgt-subrack/kha-bgt-power/kha-bgt-power-front-03-misc/kha-bgt-power-front-03-misc-render-front.png]


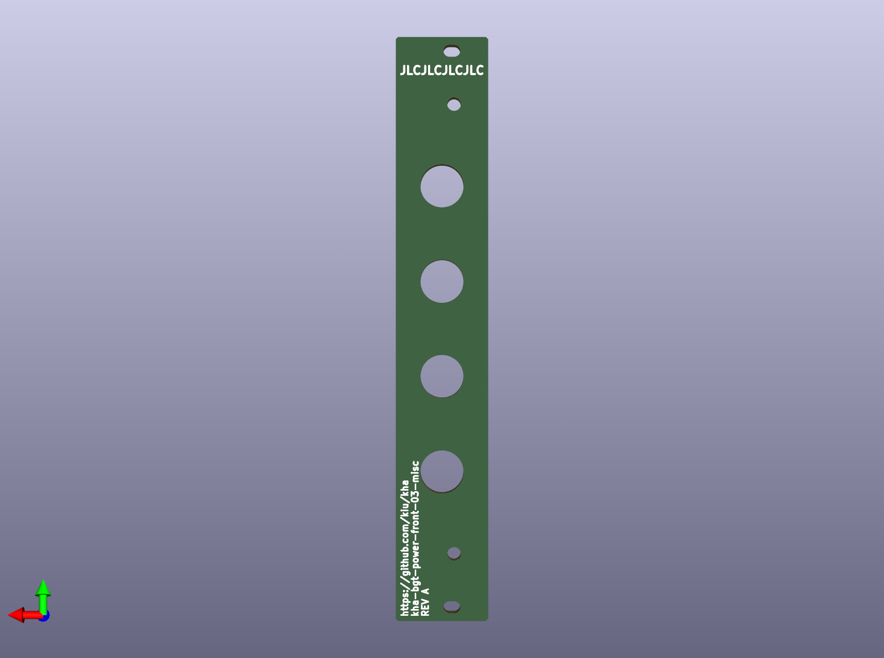
[picture p69: kha-bgt-subrack/kha-bgt-power/kha-bgt-power-front-03-misc/kha-bgt-power-front-03-misc-render-back.png]
