kiu/kha/kha-bgt-subrack/kha-bgt-power/kha-bgt-power-sub/README.md

# kha-bgt-power-sub

Mains Power Switching Module Four Push Button Mounting PCB

## Render



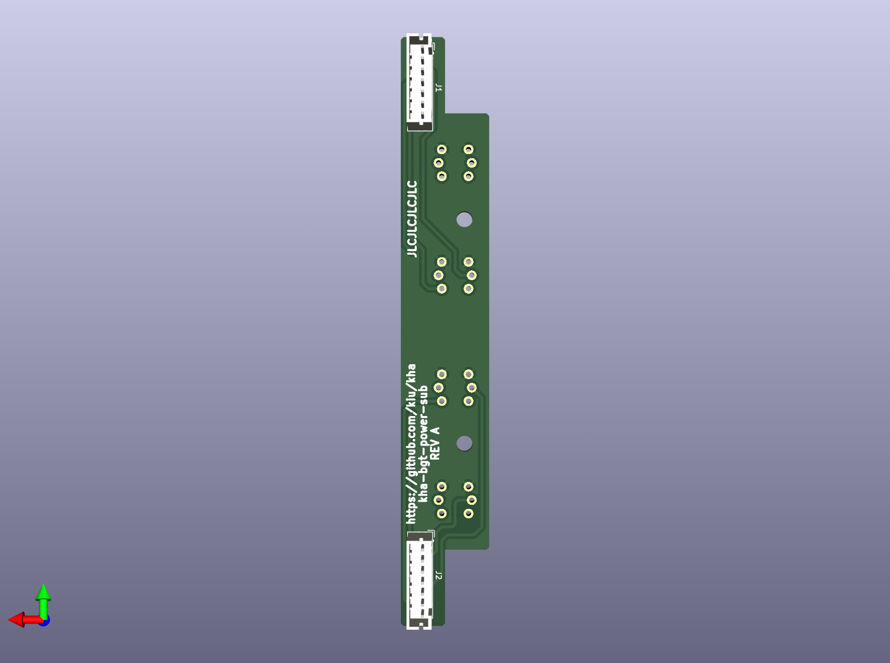
[picture p70: kha-bgt-subrack/kha-bgt-power/kha-bgt-power-sub/kha-bgt-power-sub-render-back.png]
