kiu/kha/kha-bgt-subrack/kha-bgt-rainbow/kha-bgt-rainbow-sub/README.md

# kha-bgt-rainbow-sub

Rainbow Animation Module One Push Button Mounting PCB

## Render

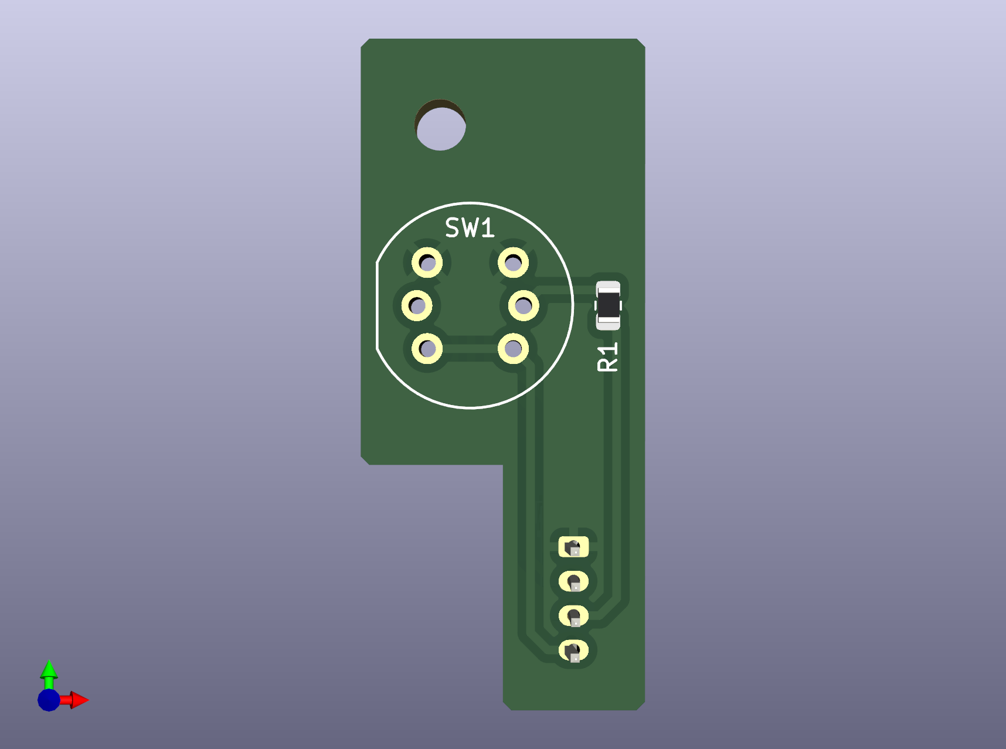
[picture p71: kha-bgt-subrack/kha-bgt-rainbow/kha-bgt-rainbow-sub/kha-bgt-rainbow-sub-render-front.png]


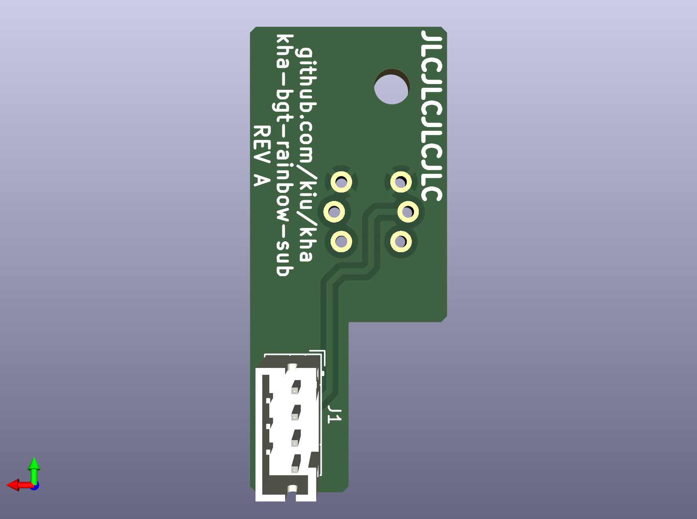
[picture p72: kha-bgt-subrack/kha-bgt-rainbow/kha-bgt-rainbow-sub/kha-bgt-rainbow-sub-render-back.png]
