kiu/kha/kha-nodes/kha-led-ikea/kha-led-ikea-node/README.md

# kha-led-ikea-node

IKEA LED Node

## Photos



## Render

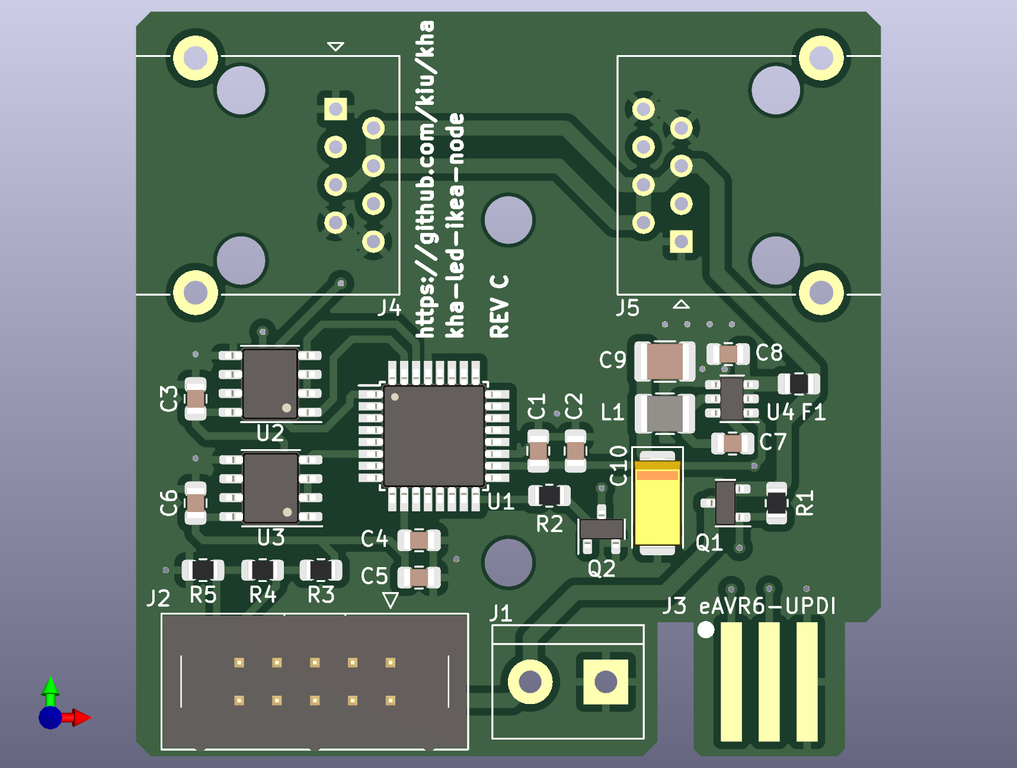
[picture p73: kha-nodes/kha-led-ikea/kha-led-ikea-node/kha-led-ikea-node-render-front.png]


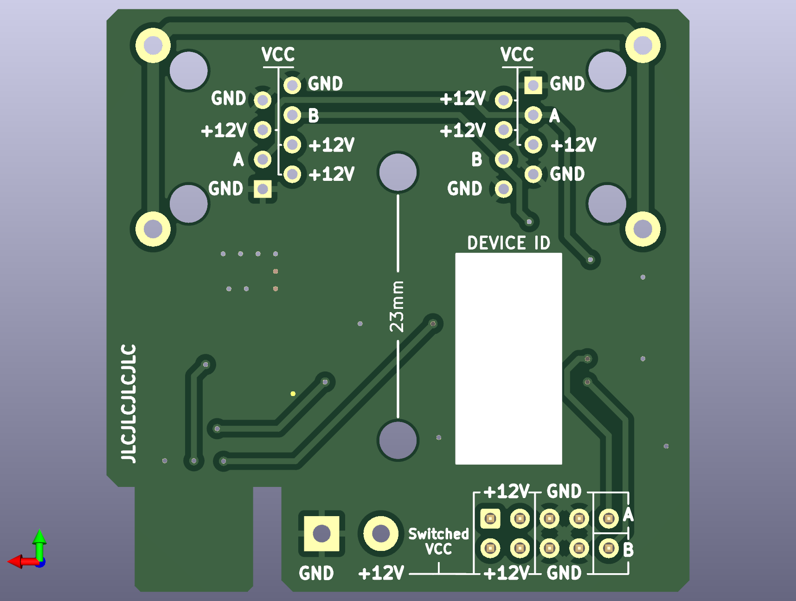
[picture p74: kha-nodes/kha-led-ikea/kha-led-ikea-node/kha-led-ikea-node-render-back.png]
