kiu/kha/kha-nodes/kha-relay-2x3/kha-relay-2x3-box/README.md

# kha-relay-2x3-box

Mains Power Relay Box

## Photos



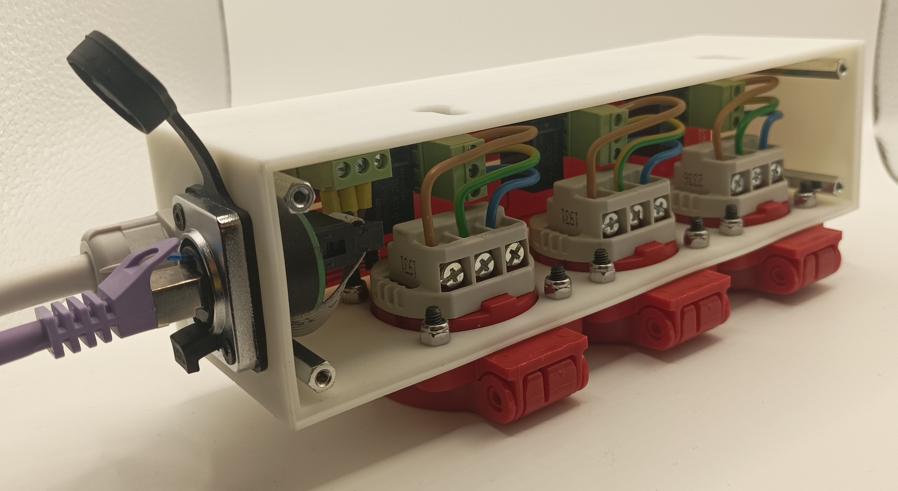
[picture p75: kha-nodes/kha-relay-2x3/kha-relay-2x3-box/kha-relay-2x3-box-photo-inside.jpg]
