kiu/kha/kha-nodes/kha-relay-2x3/kha-relay-2x3-node/README.md

# kha-relay-2x3-node

Mains Power Relay Node

## Photos



## Render

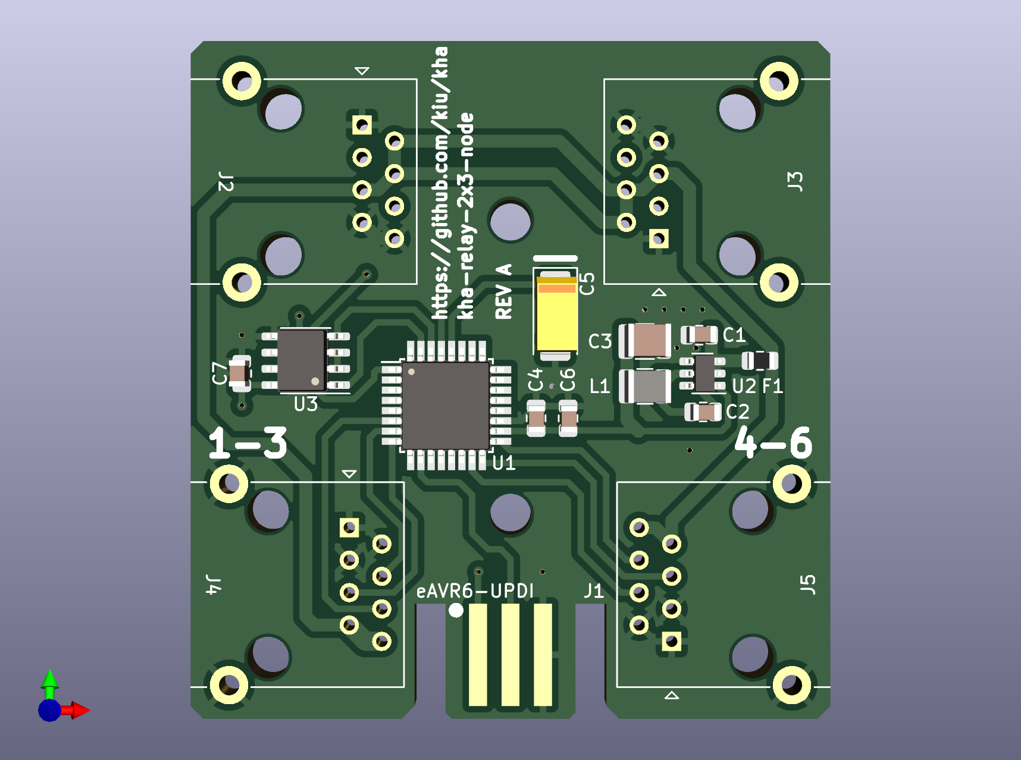
[picture p76: kha-nodes/kha-relay-2x3/kha-relay-2x3-node/kha-relay-2x3-node-render-front.png]


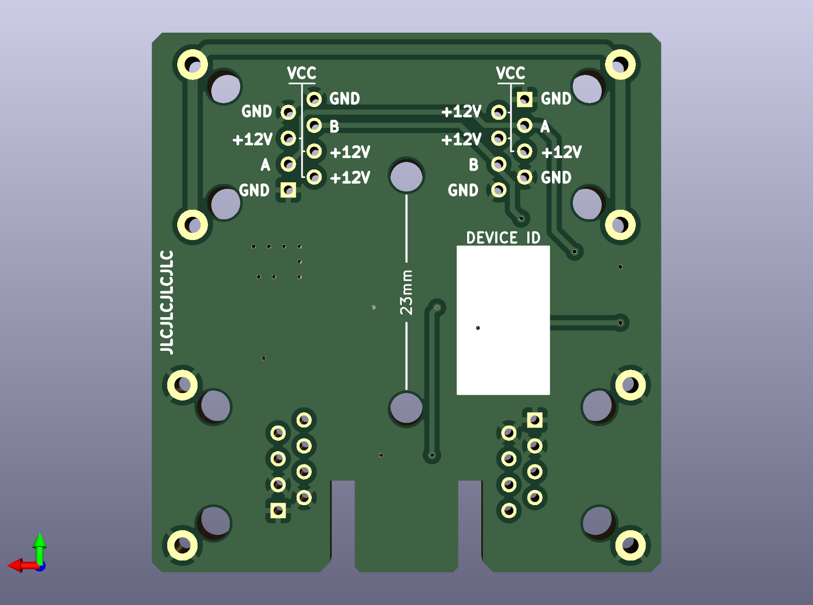
[picture p77: kha-nodes/kha-relay-2x3/kha-relay-2x3-node/kha-relay-2x3-node-render-back.png]
