kiu/kha/kha-nodes/kha-led-ikea/kha-led-ikea-lighting/kha-led-ikea-kallax/README.md

# kha-led-ikea-kallax

IKEA Kallax LED Panels 

## Photos



## Render

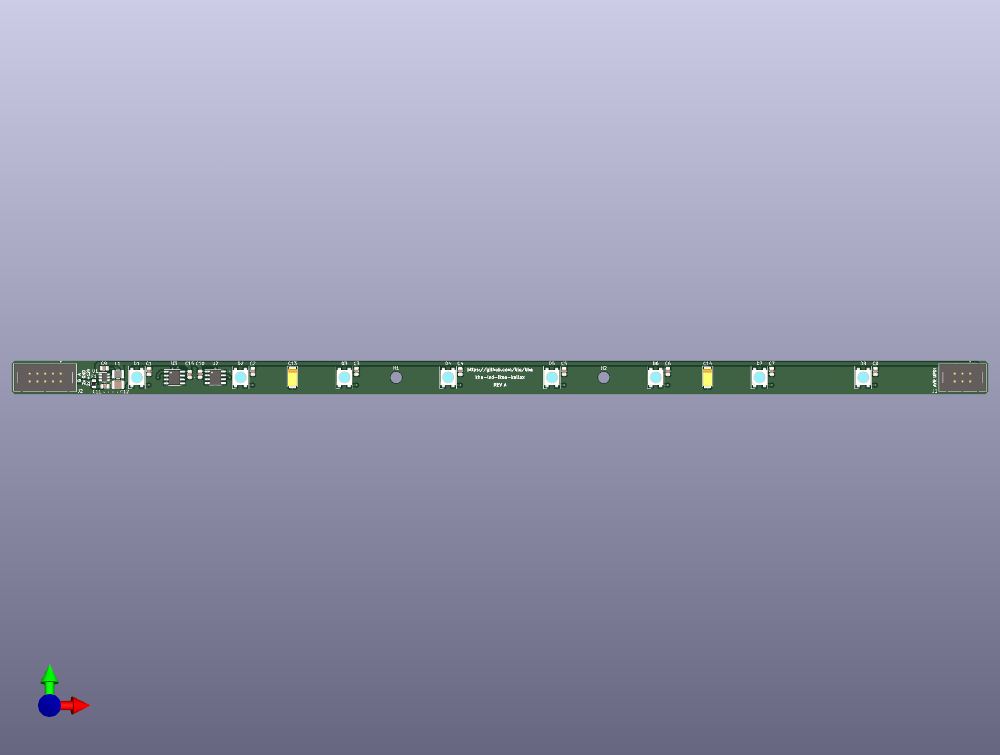
[picture p78: kha-nodes/kha-led-ikea/kha-led-ikea-lighting/kha-led-ikea-kallax/kha-led-ikea-kallax-render-front.png]


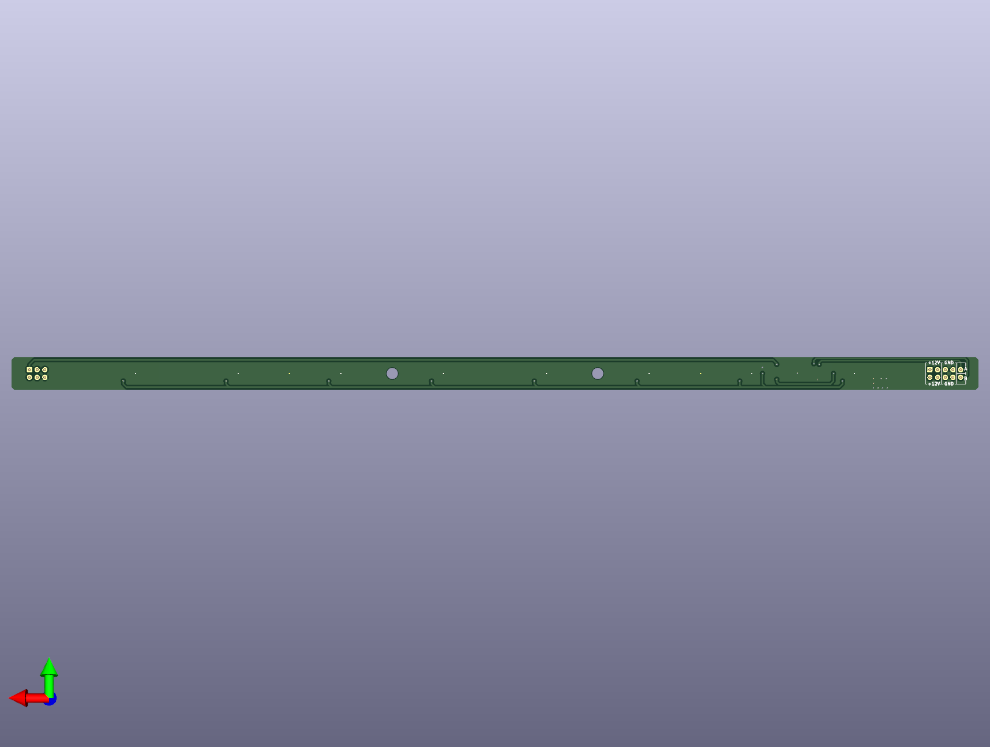
[picture p79: kha-nodes/kha-led-ikea/kha-led-ikea-lighting/kha-led-ikea-kallax/kha-led-ikea-kallax-render-back.png]
