kiu/kha/kha-nodes/kha-led-ikea/kha-led-ikea-lighting/kha-led-ikea-oxberg40/README.md

# kha-led-ikea-oxberg40

IKEA Oxberg 40cm LED Panels 

## Photos

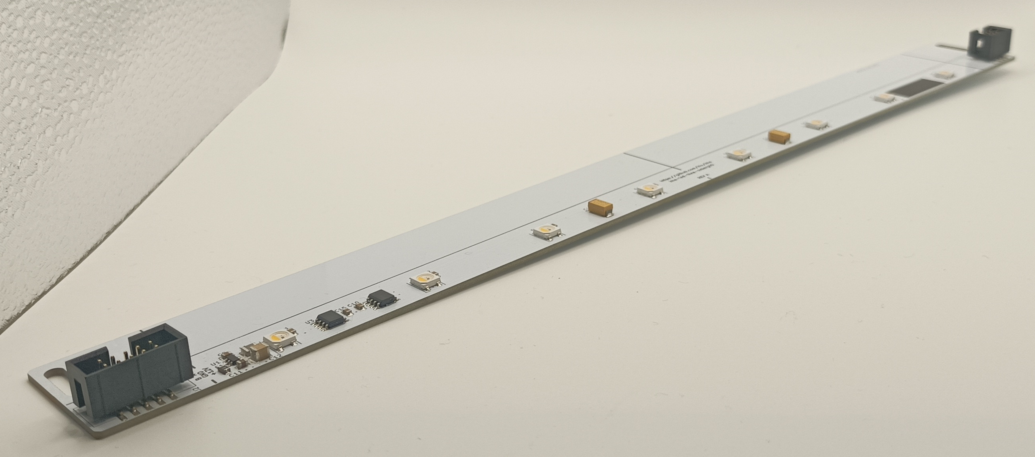
[picture p80: kha-nodes/kha-led-ikea/kha-led-ikea-lighting/kha-led-ikea-oxberg40/kha-led-ikea-oxberg40-photo.jpg]




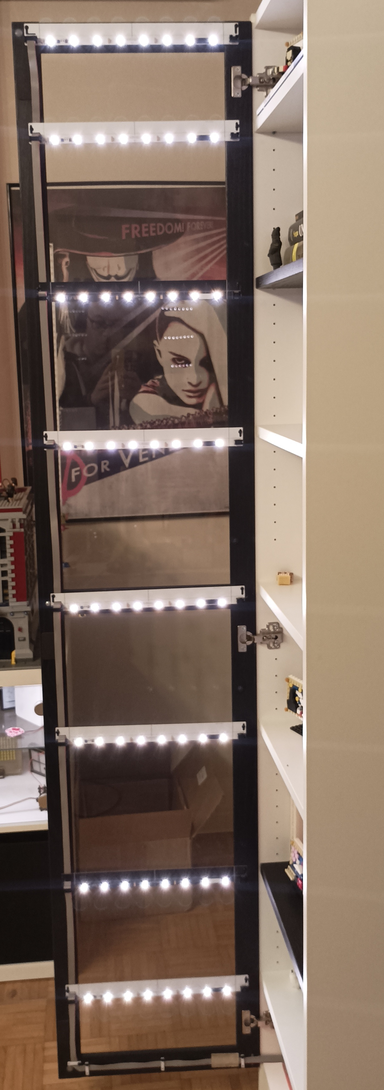
[picture p81: kha-nodes/kha-led-ikea/kha-led-ikea-lighting/kha-led-ikea-oxberg40/kha-led-ikea-oxberg40-photo-inside.jpg]


## Render

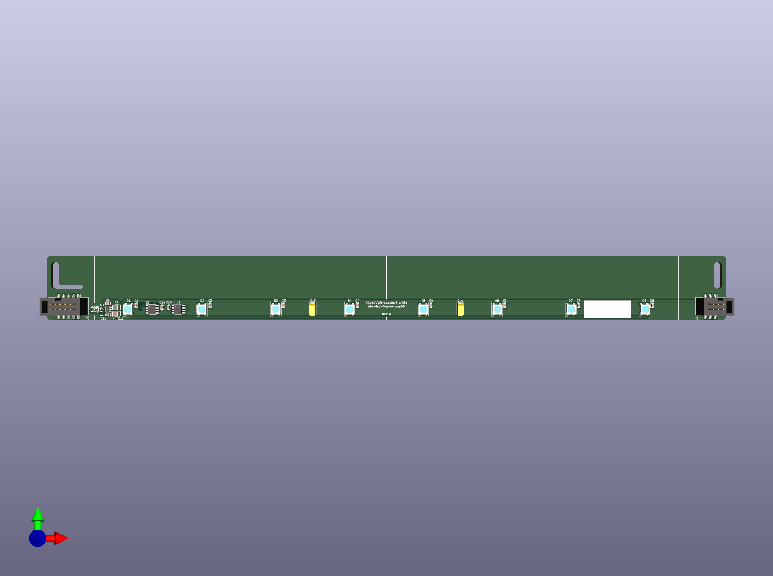
[picture p82: kha-nodes/kha-led-ikea/kha-led-ikea-lighting/kha-led-ikea-oxberg40/kha-led-ikea-oxberg40-render-front.png]


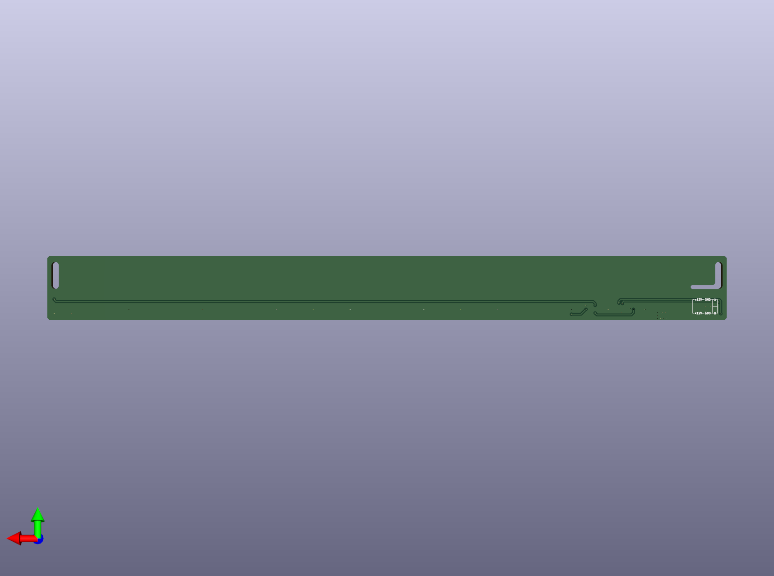
[picture p83: kha-nodes/kha-led-ikea/kha-led-ikea-lighting/kha-led-ikea-oxberg40/kha-led-ikea-oxberg40-render-back.png]
