kiu/kha/kha-nodes/kha-led-ikea/kha-led-ikea-lighting/kha-led-ikea-term/README.md

# kha-led-ikea-term

IKEA LED Panel Bus Termination

## Render

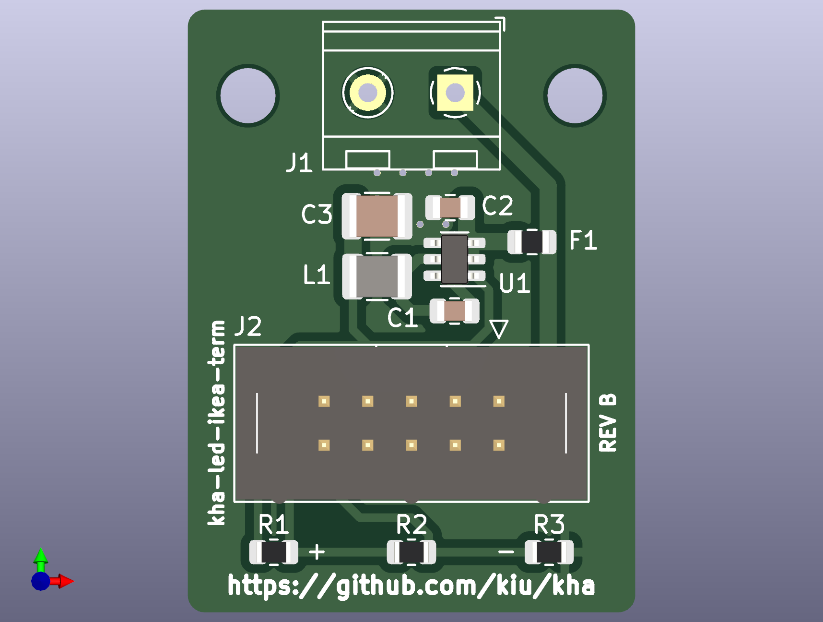
[picture p84: kha-nodes/kha-led-ikea/kha-led-ikea-lighting/kha-led-ikea-term/kha-led-ikea-term-render-front.png]


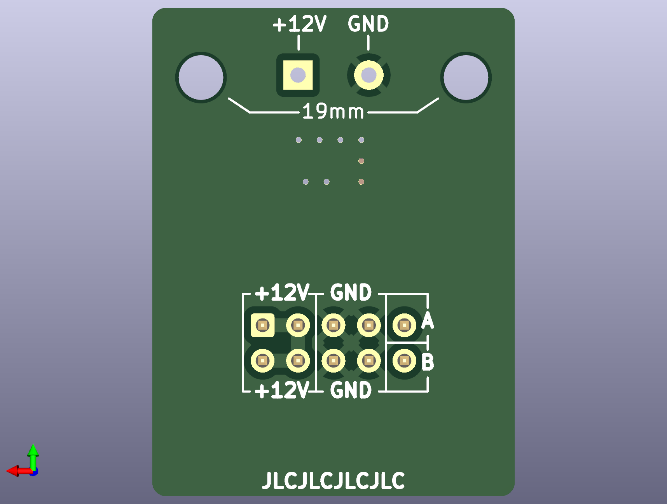
[picture p85: kha-nodes/kha-led-ikea/kha-led-ikea-lighting/kha-led-ikea-term/kha-led-ikea-term-render-back.png]
