kiu/kha/kha-nodes/kha-relay-2x3/kha-relay-2x3-box/kha-relay-2x3-base/README.md

# kha-relay-2x3-base

Mains Power Relay Box Base

## Render

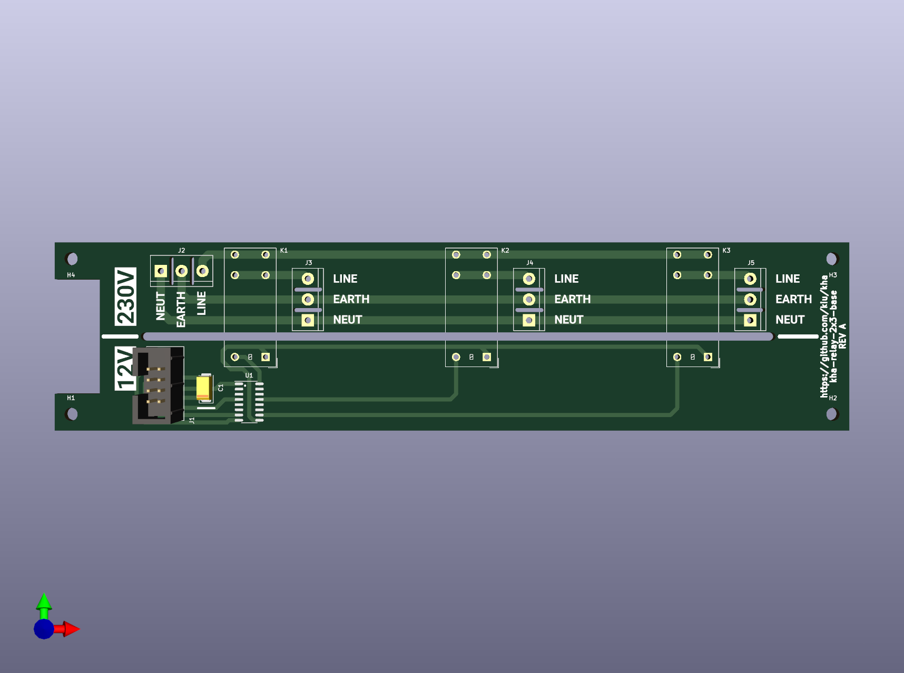
[picture p86: kha-nodes/kha-relay-2x3/kha-relay-2x3-box/kha-relay-2x3-base/kha-relay-2x3-base-render-front.png]


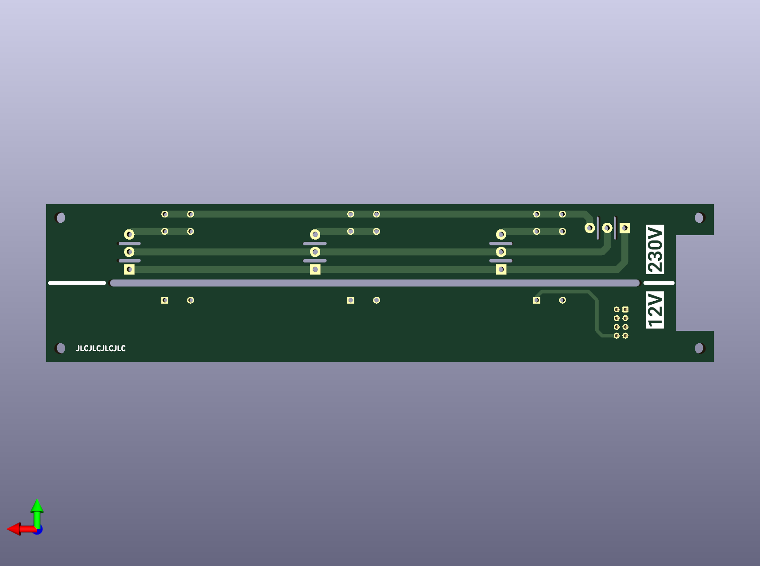
[picture p87: kha-nodes/kha-relay-2x3/kha-relay-2x3-box/kha-relay-2x3-base/kha-relay-2x3-base-render-back.png]
