kiu/kha/kha-nodes/kha-relay-2x3/kha-relay-2x3-box/kha-relay-2x3-front/README.md

# kha-relay-2x3-front

Mains Power Relay Box Front

## Render

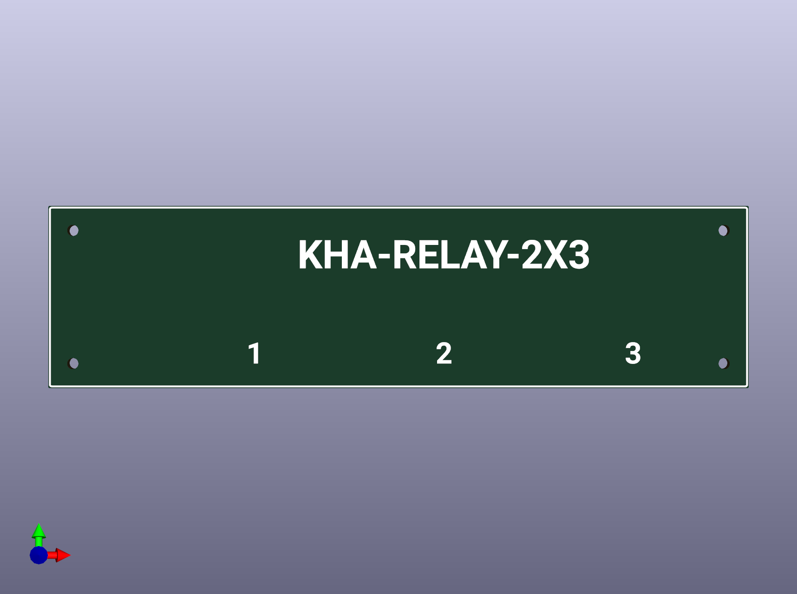
[picture p88: kha-nodes/kha-relay-2x3/kha-relay-2x3-box/kha-relay-2x3-front/kha-relay-2x3-front-render-front.png]


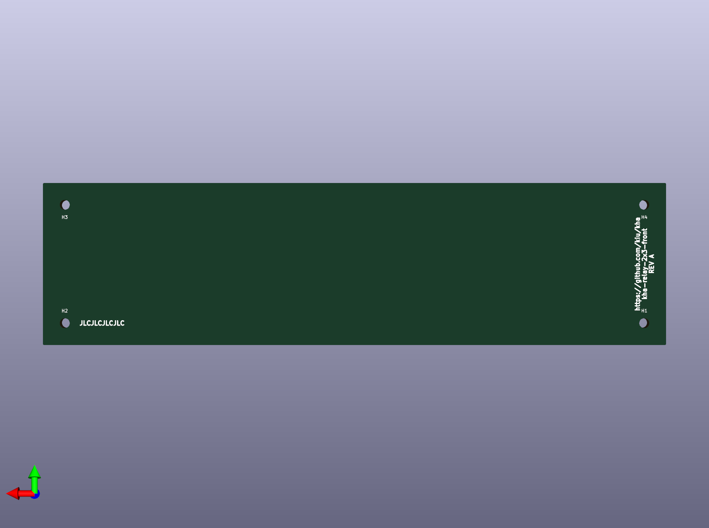
[picture p89: kha-nodes/kha-relay-2x3/kha-relay-2x3-box/kha-relay-2x3-front/kha-relay-2x3-front-render-back.png]
