kiu/kha/kha-bgt-subrack/kha-bgt-kaox/README.md

# kha-bgt-kaox

Kallax / Oxberg Module

## Parts

Use [kha-bgt-generic-base](../../kha-bgt-misc/kha-bgt-generic-base/) as base

Use [kha-bgt-generic-4btn-sub](../../kha-bgt-misc/kha-bgt-generic-4btn-sub/) as sub

## Photos

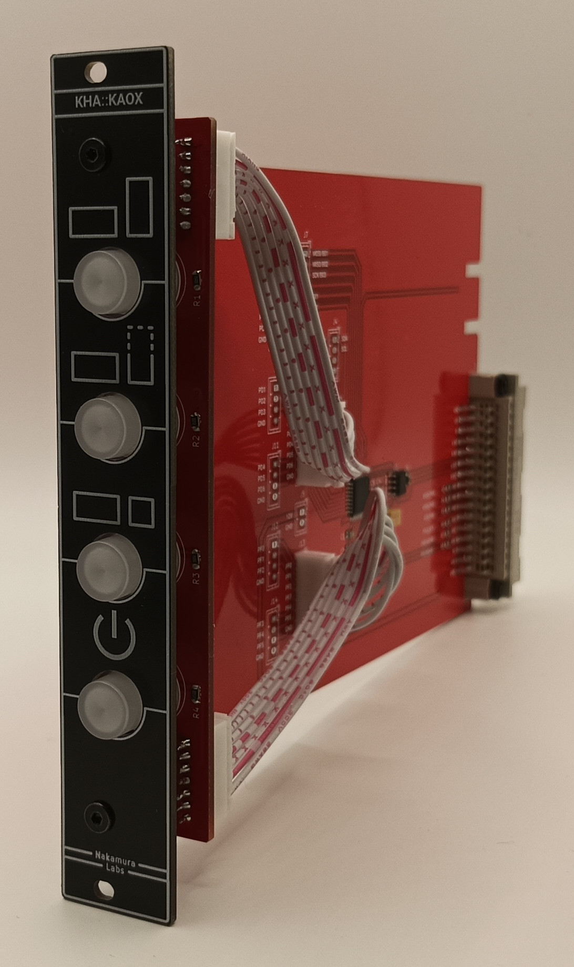
[picture p95: kha-bgt-subrack/kha-bgt-kaox/kha-bgt-kaox-photo.jpg]
