kiu/kha/kha-bgt-subrack/kha-bgt-preset/README.md

# kha-bgt-preset

Preset Module

## Parts

Use [kha-bgt-generic-base](../../kha-bgt-misc/kha-bgt-generic-base/) as base

Use [kha-bgt-generic-4btn-sub](../../kha-bgt-misc/kha-bgt-generic-4btn-sub/) as sub

## Photos

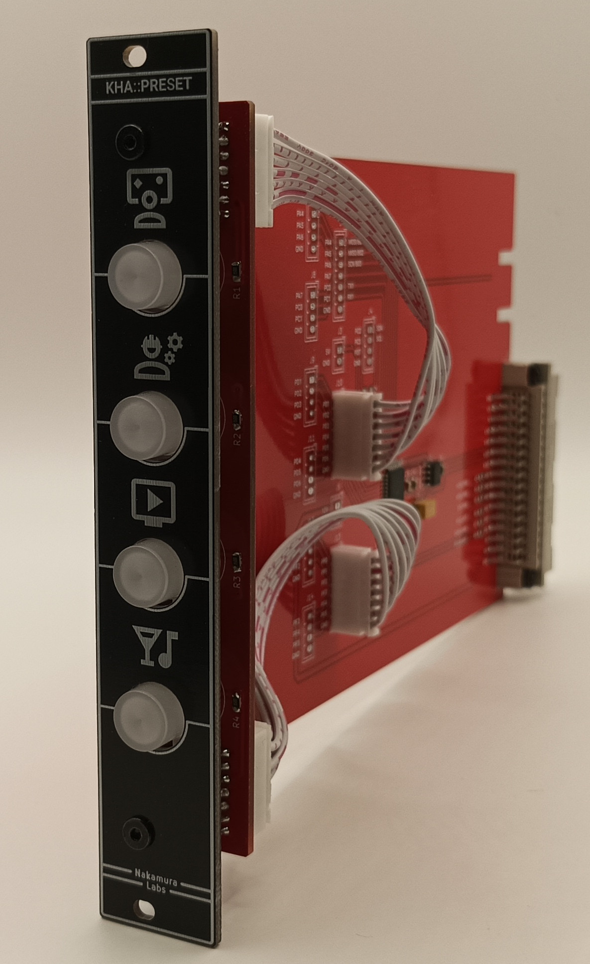
[picture p96: kha-bgt-subrack/kha-bgt-preset/kha-bgt-preset-photo.jpg]
