kiu/kha/kha-nodes/kha-gateway-usb/README.md

# kha-gateway-usb

USB Serial Gateway Node

## Photos

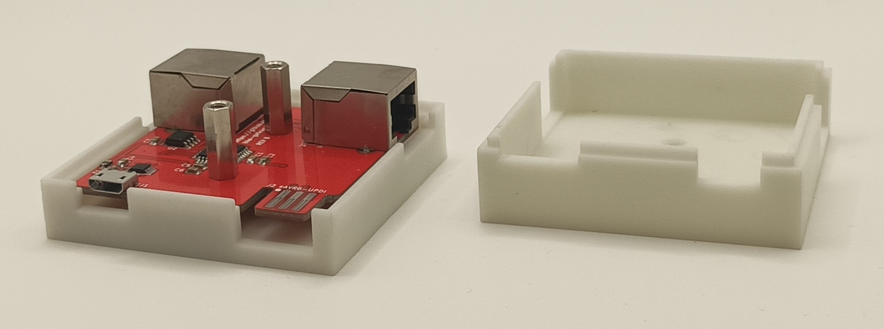
[picture p97: kha-nodes/kha-gateway-usb/kha-gateway-usb-photo.jpg]


## Render

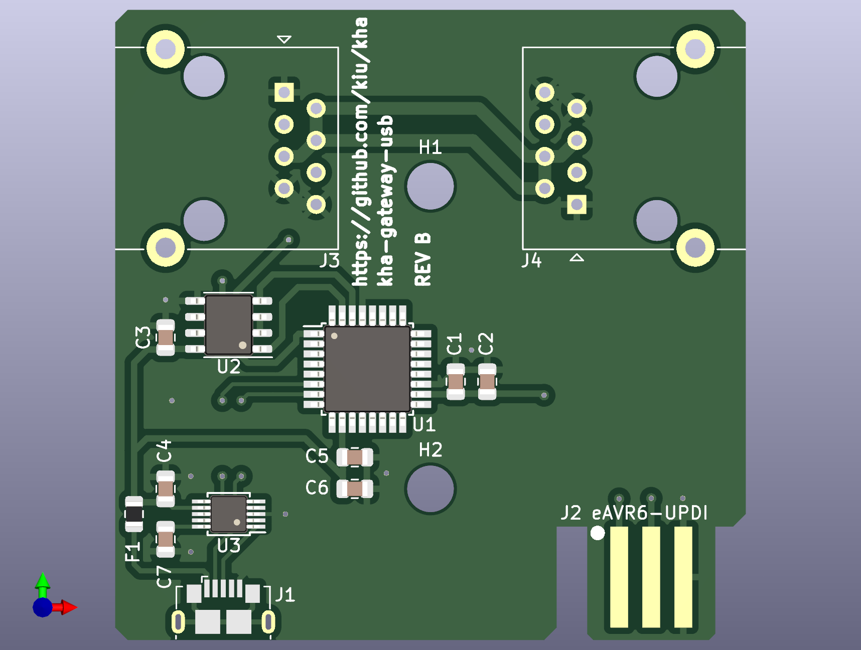
[picture p98: kha-nodes/kha-gateway-usb/kha-gateway-usb-render-front.png]


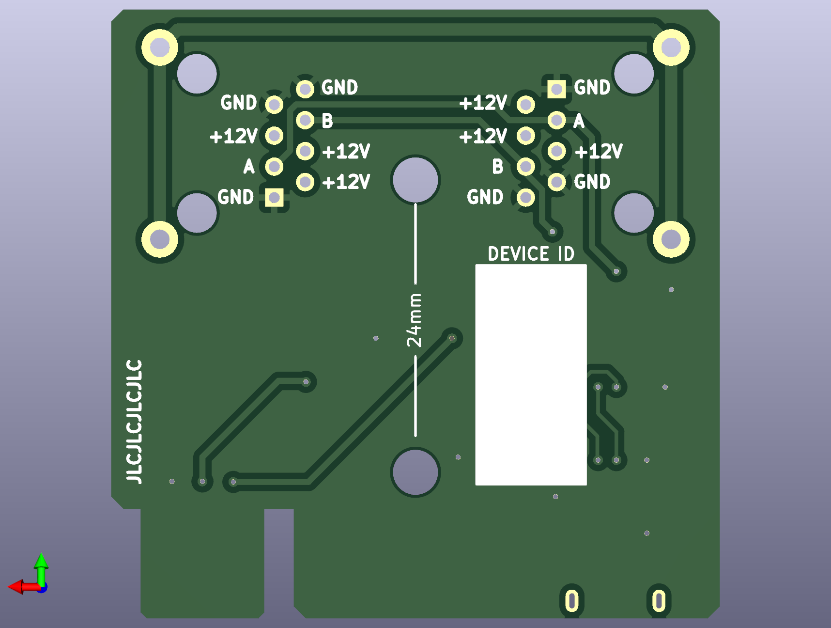
[picture p99: kha-nodes/kha-gateway-usb/kha-gateway-usb-render-back.png]
