kiu/kha/kha-bgt-misc/kha-bgt-extend/README.md

# kha-bgt-extend

Debugging Extender

## Photos

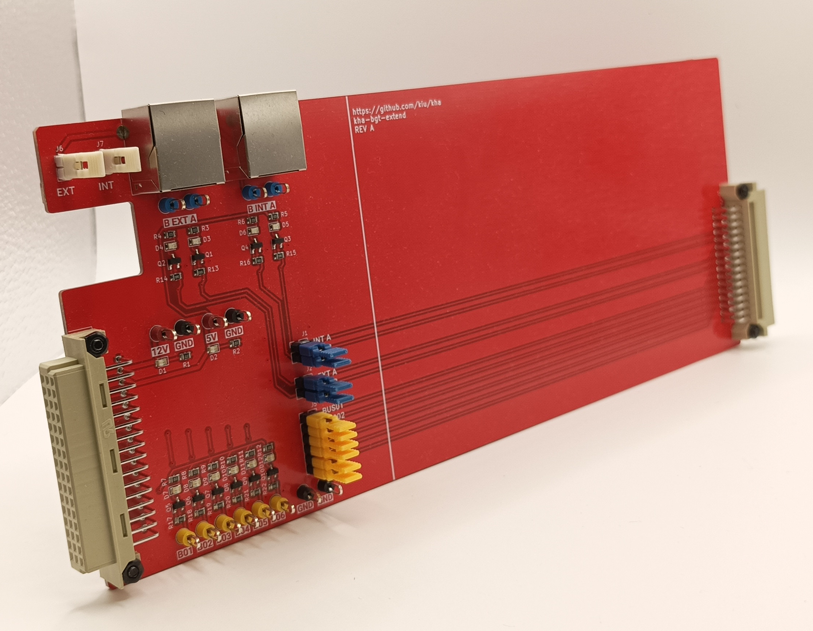
[picture p100: kha-bgt-misc/kha-bgt-extend/kha-bgt-extend-photo.jpg]


## Render

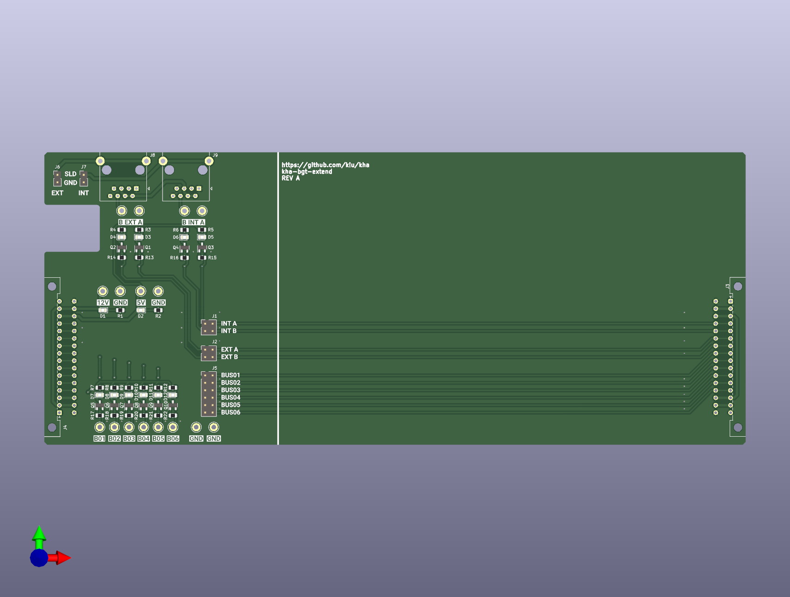
[picture p101: kha-bgt-misc/kha-bgt-extend/kha-bgt-extend-render-front.png]


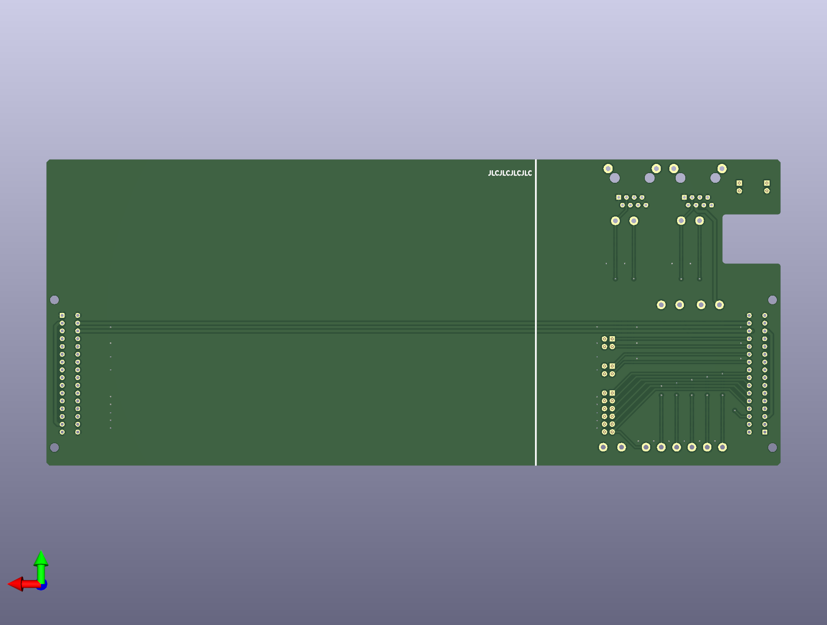
[picture p102: kha-bgt-misc/kha-bgt-extend/kha-bgt-extend-render-back.png]
