kiu/kha/kha-nodes/kha-term/README.md

# kha-pwr-term

Bus Termination

## Photos

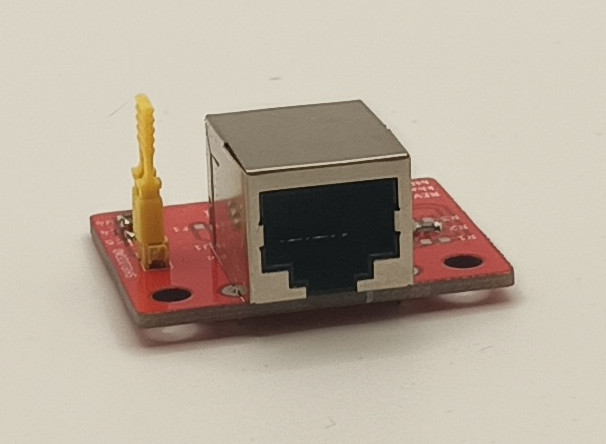
[picture p103: kha-nodes/kha-term/kha-term-photo.jpg]


## Render

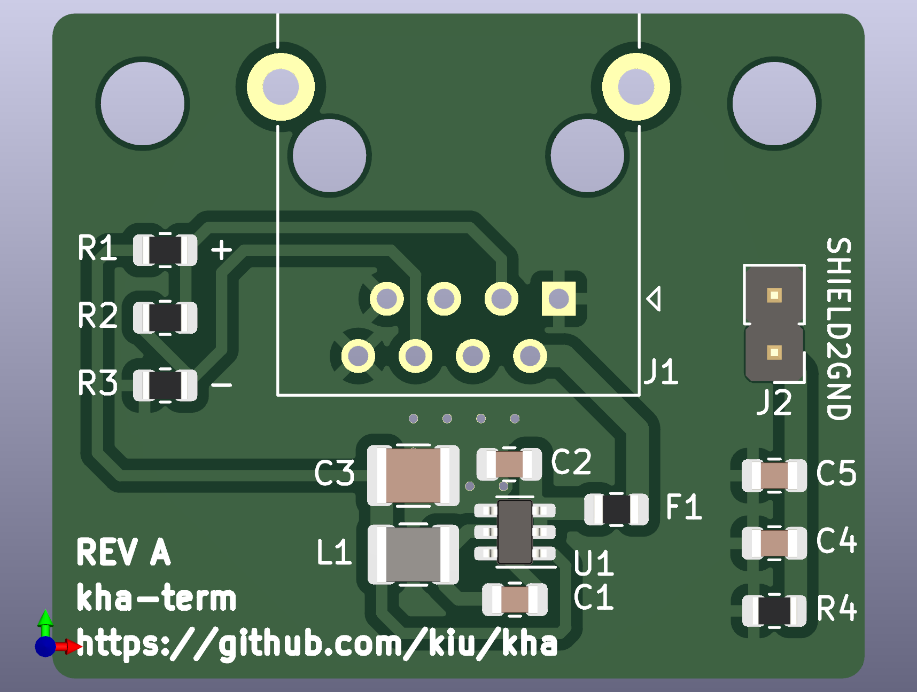
[picture p104: kha-nodes/kha-term/kha-term-render-front.png]


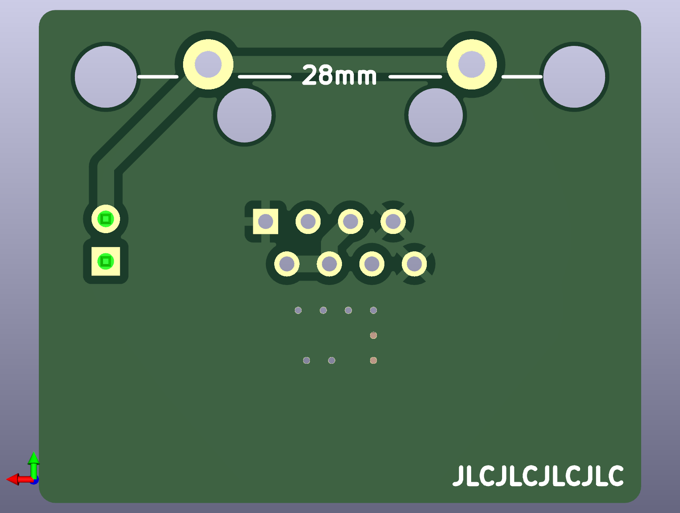
[picture p105: kha-nodes/kha-term/kha-term-render-back.png]
