kiu/kha/kha-bgt-misc/kha-bgt-generic-base/README.md

# kha-bgt-generic-base

Generic Base

## Render

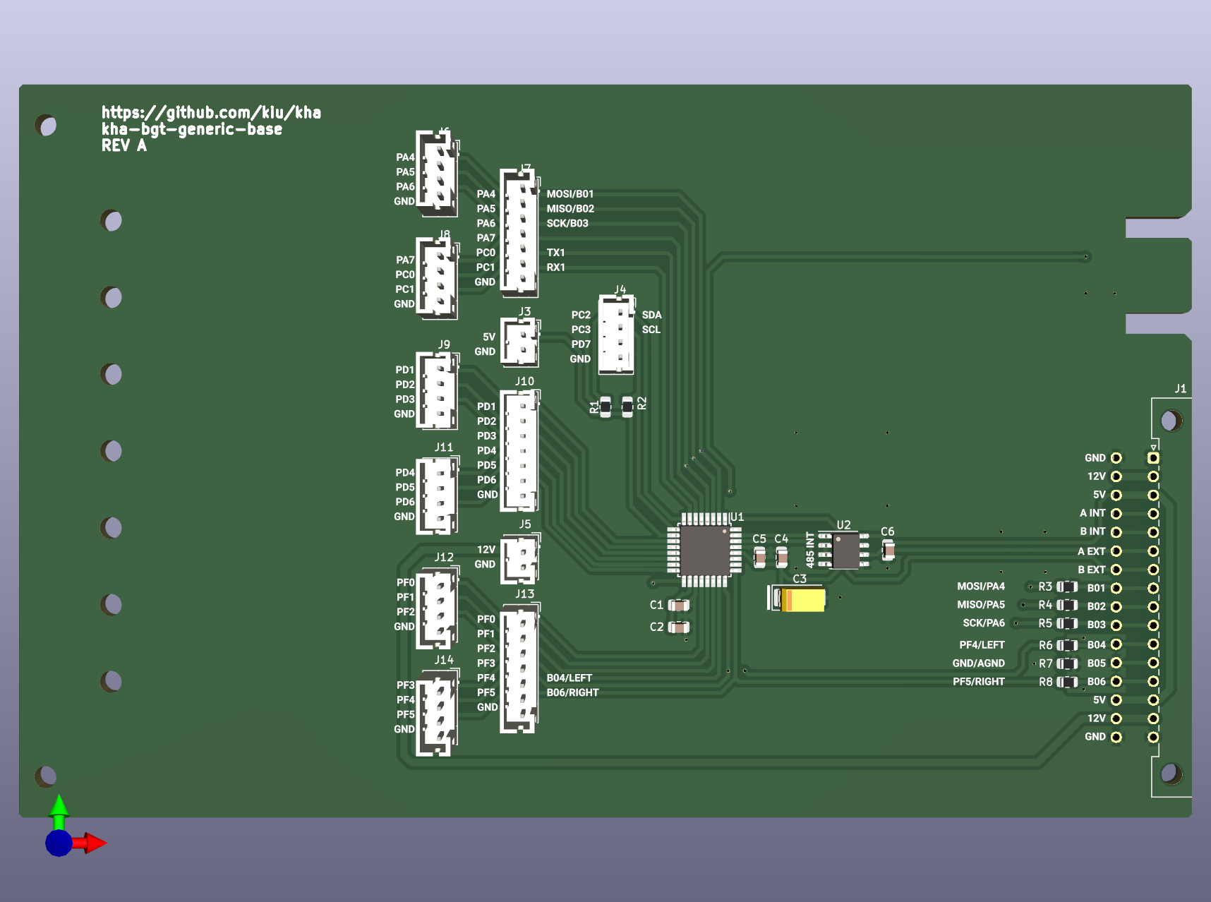
[picture p106: kha-bgt-misc/kha-bgt-generic-base/kha-bgt-generic-base-render-front.png]


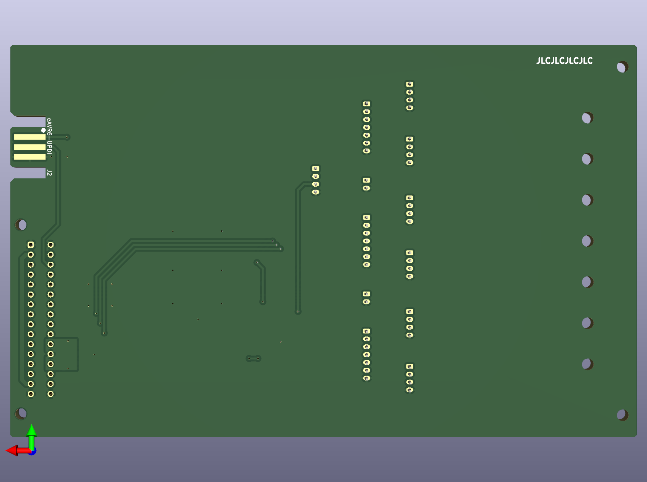
[picture p107: kha-bgt-misc/kha-bgt-generic-base/kha-bgt-generic-base-render-back.png]
