kiu/kha/kha-bgt-misc/kha-bgt-nop4/README.md

# kha-bgt-nop4

Dummy 4HP Front Panel

## Render

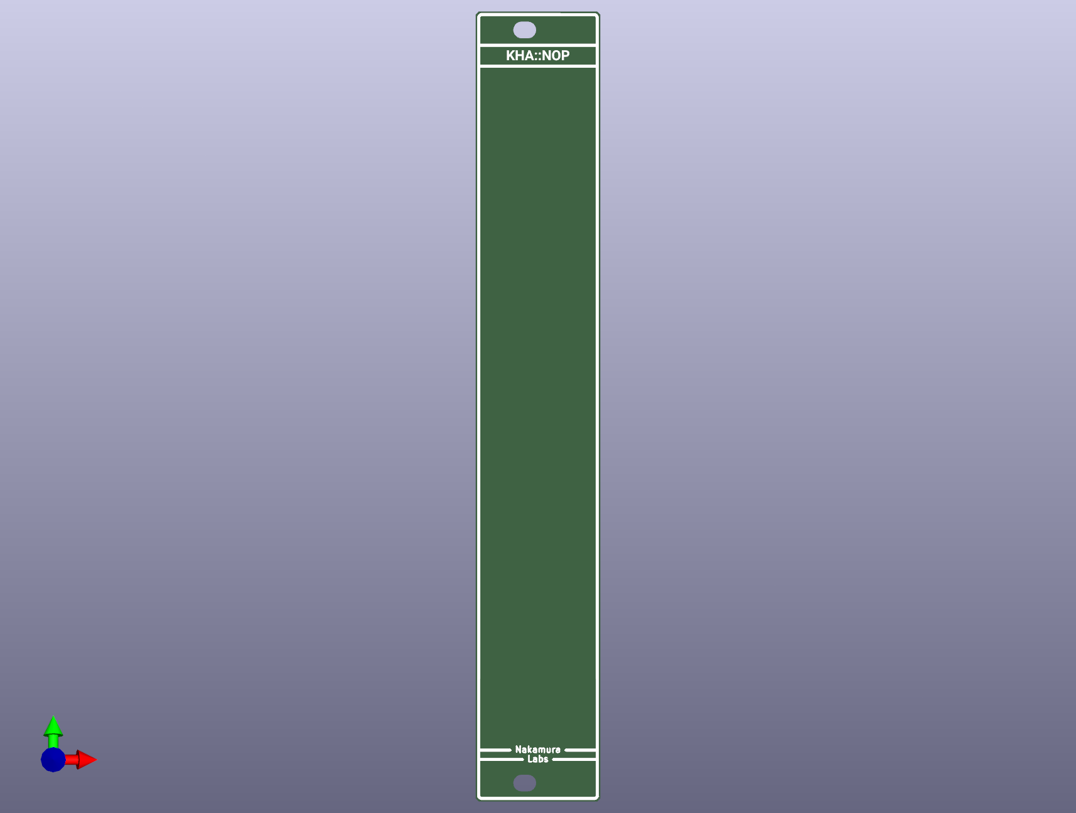
[picture p108: kha-bgt-misc/kha-bgt-nop4/kha-bgt-nop4-render-front.png]


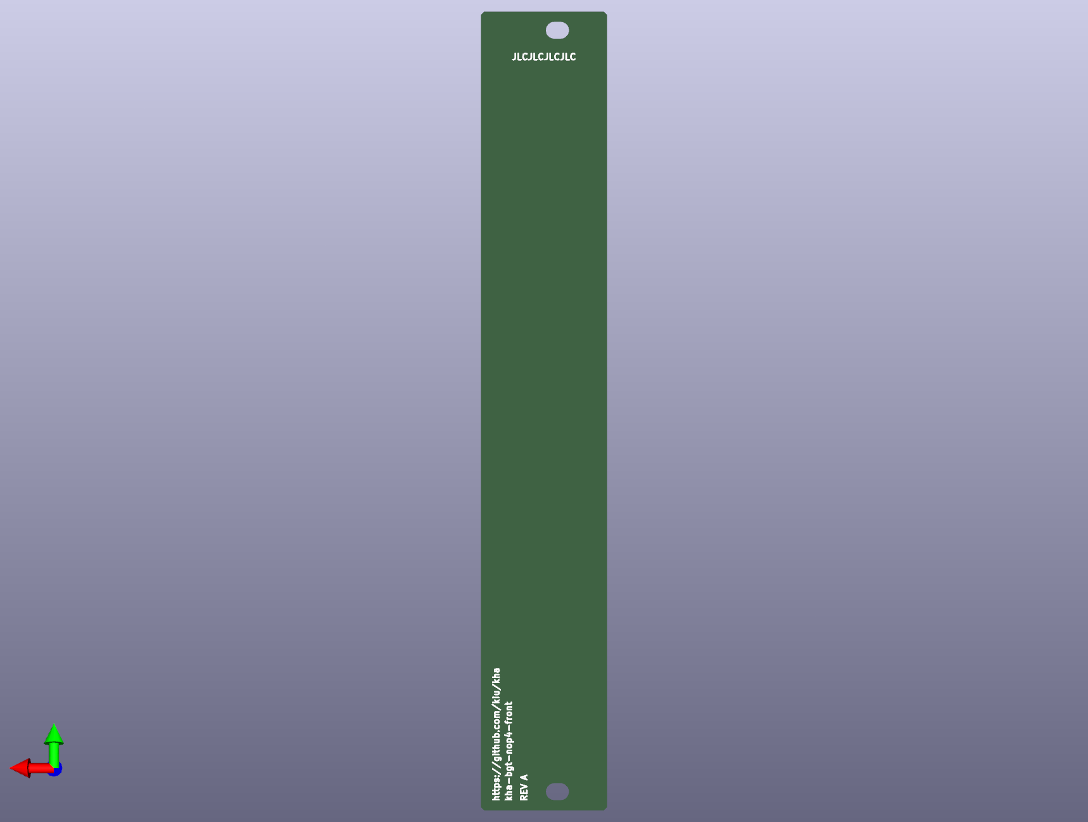
[picture p109: kha-bgt-misc/kha-bgt-nop4/kha-bgt-nop4-render-back.png]
