kiu/kha/kha-bgt-misc/kha-bgt-nop8/README.md

# kha-bgt-nop8

Dummy 8HP Front Panel

## Render

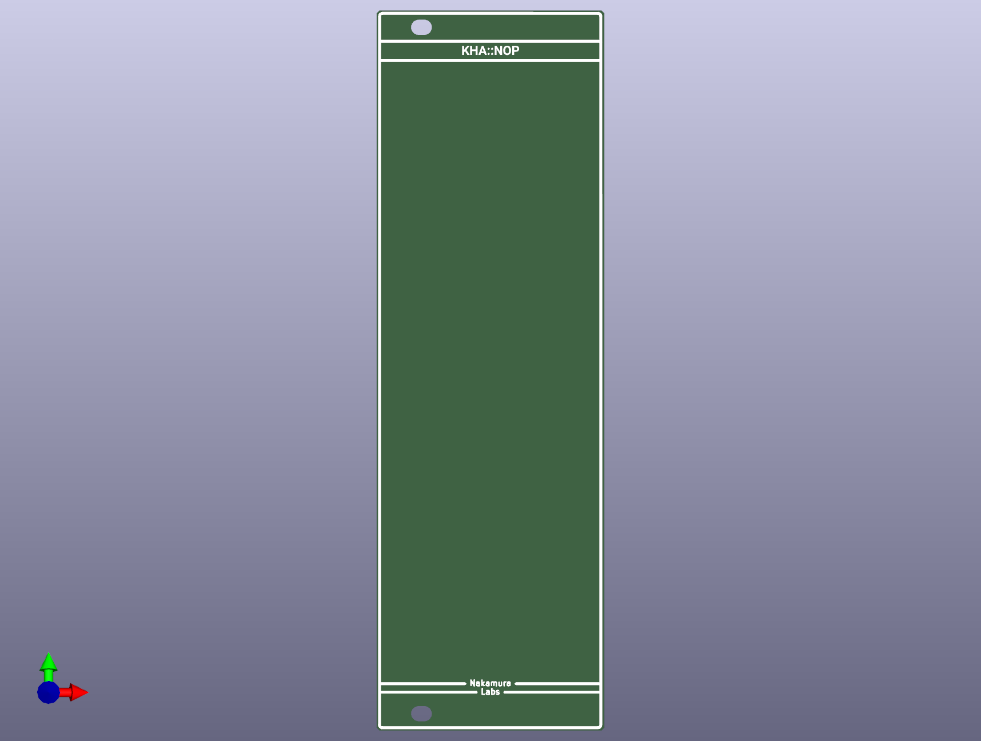
[picture p110: kha-bgt-misc/kha-bgt-nop8/kha-bgt-nop8-render-front.png]


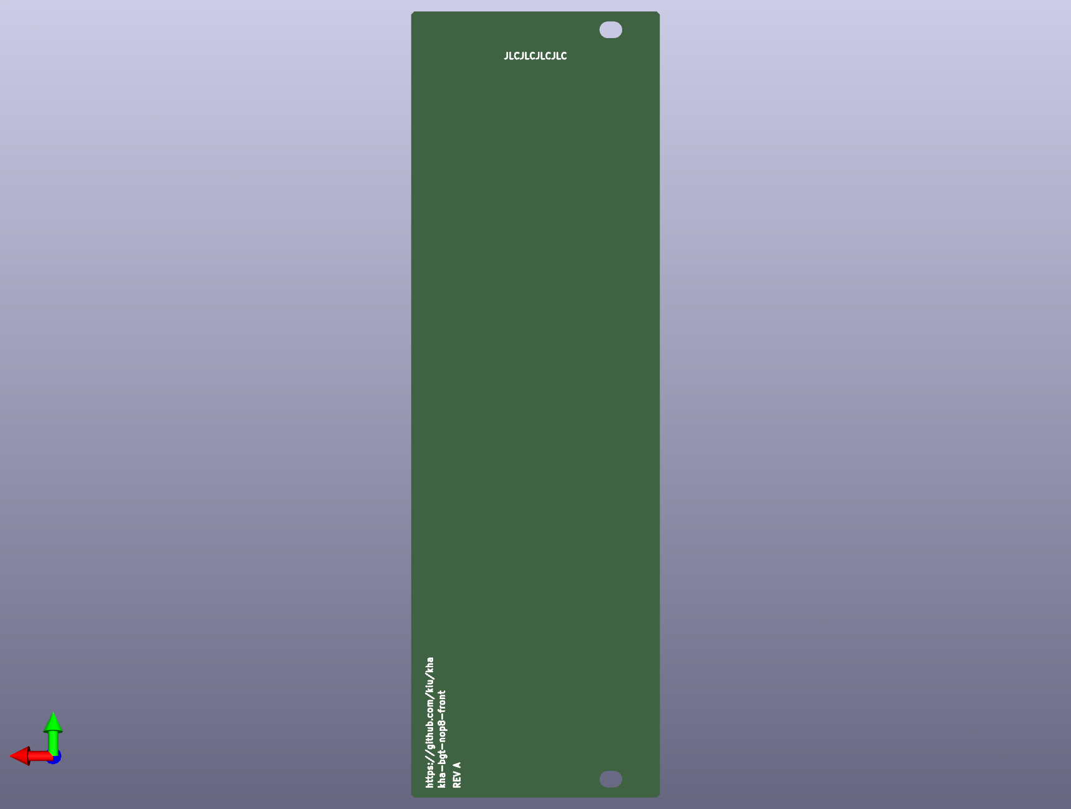
[picture p111: kha-bgt-misc/kha-bgt-nop8/kha-bgt-nop8-render-back.png]
