kiu/kha/kha-bgt-subrack/kha-bgt-dark/kha-bgt-dark-front/README.md

# kha-bgt-dark-front

Enable/Disable UI Module Front Panel

## Render

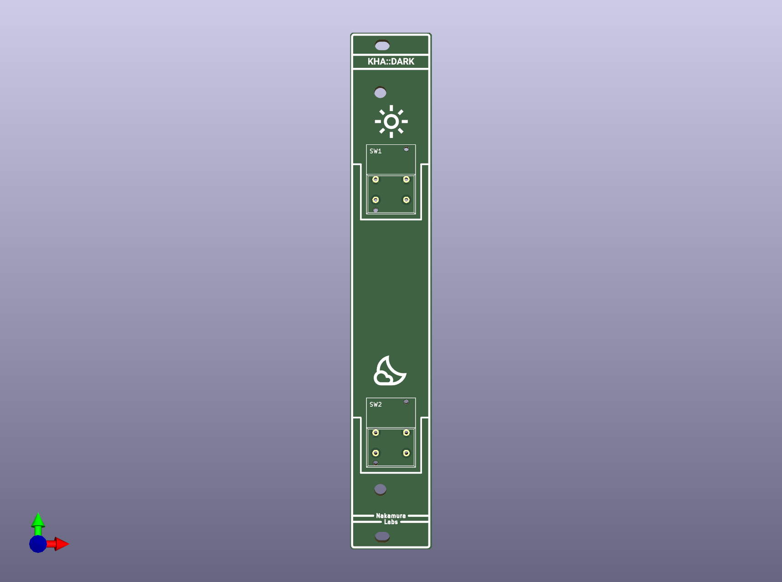
[picture p112: kha-bgt-subrack/kha-bgt-dark/kha-bgt-dark-front/kha-bgt-dark-front-render-front.png]


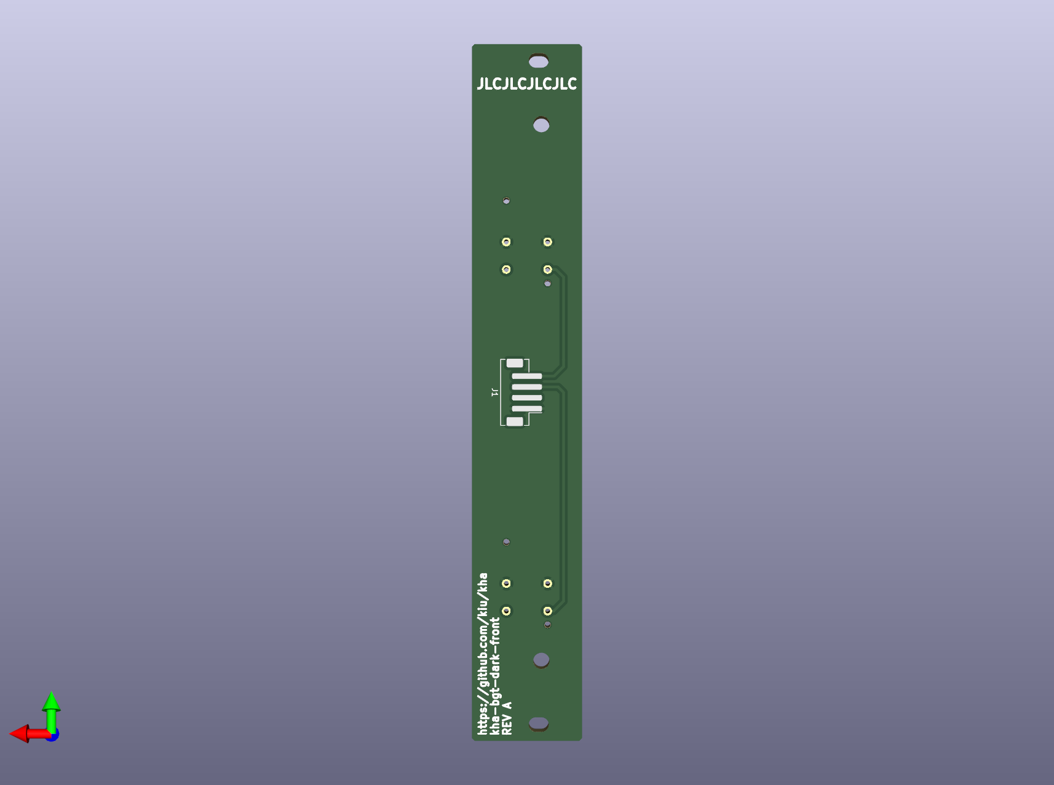
[picture p113: kha-bgt-subrack/kha-bgt-dark/kha-bgt-dark-front/kha-bgt-dark-front-render-back.png]
