kiu/kha/kha-bgt-subrack/kha-bgt-guru/kha-bgt-guru-front/README.md

# kha-bgt-guru-front

Debug Module Front Panel

## Render

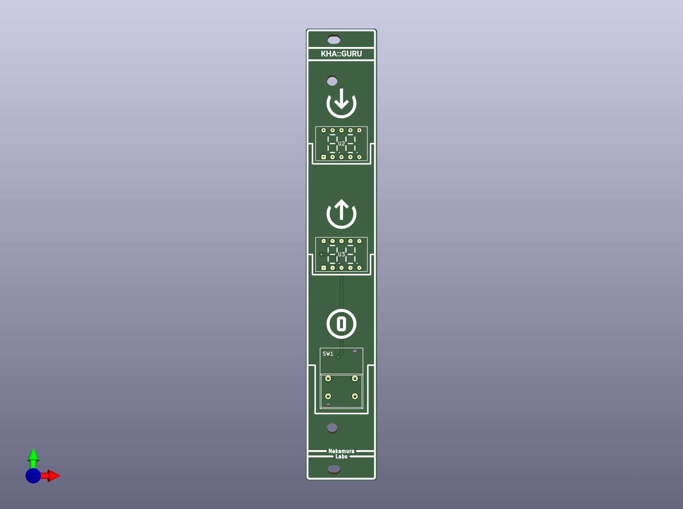
[picture p114: kha-bgt-subrack/kha-bgt-guru/kha-bgt-guru-front/kha-bgt-guru-front-render-front.png]


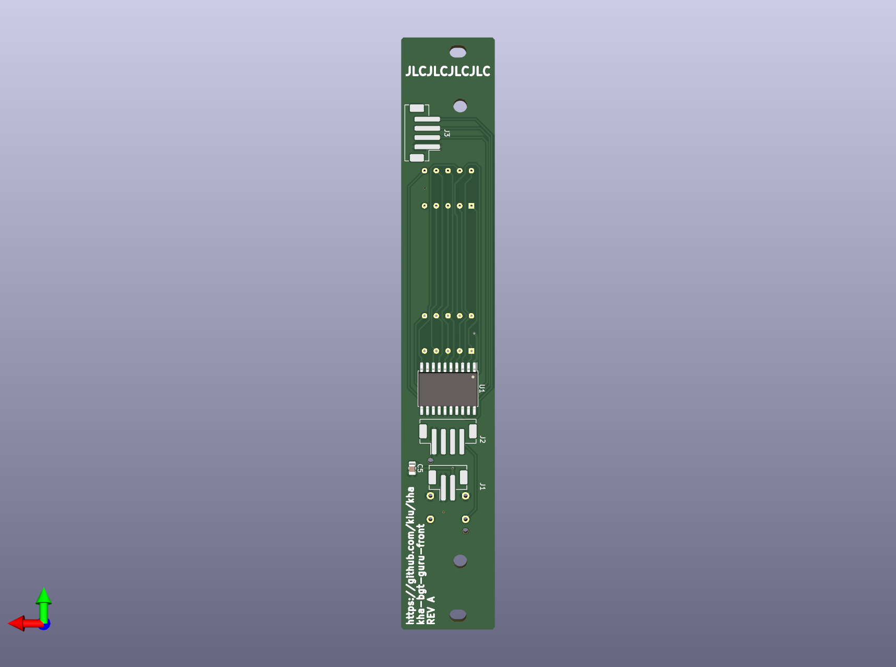
[picture p115: kha-bgt-subrack/kha-bgt-guru/kha-bgt-guru-front/kha-bgt-guru-front-render-back.png]
