kiu/kha/kha-bgt-subrack/kha-bgt-hsi/kha-bgt-hsi-front/README.md

# kha-bgt-hsi-front

Hue Saturation Intensity Module Front Panel

## Render

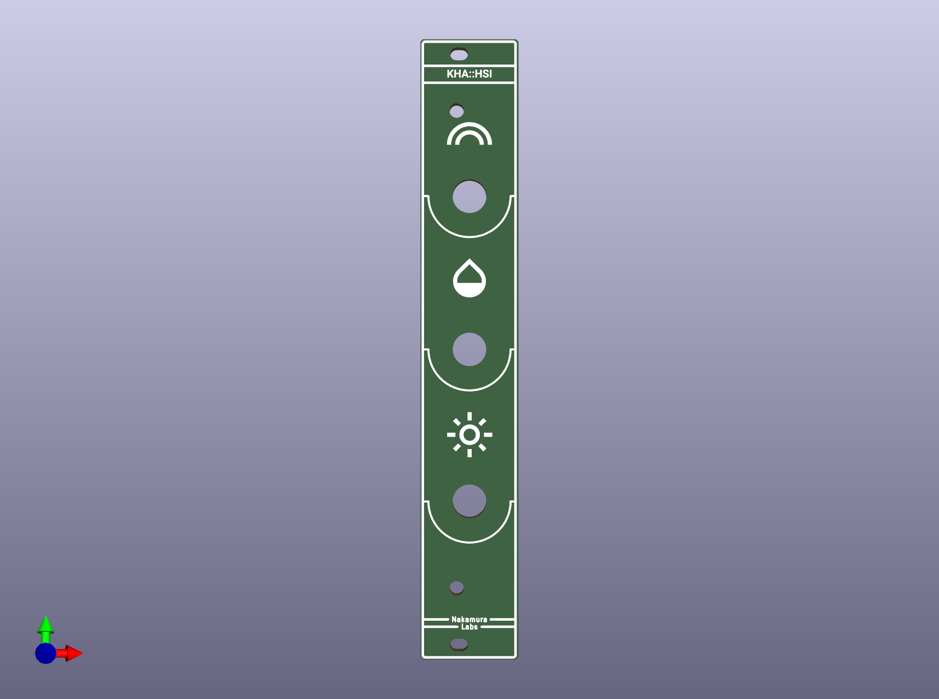
[picture p116: kha-bgt-subrack/kha-bgt-hsi/kha-bgt-hsi-front/kha-bgt-hsi-front-render-front.png]


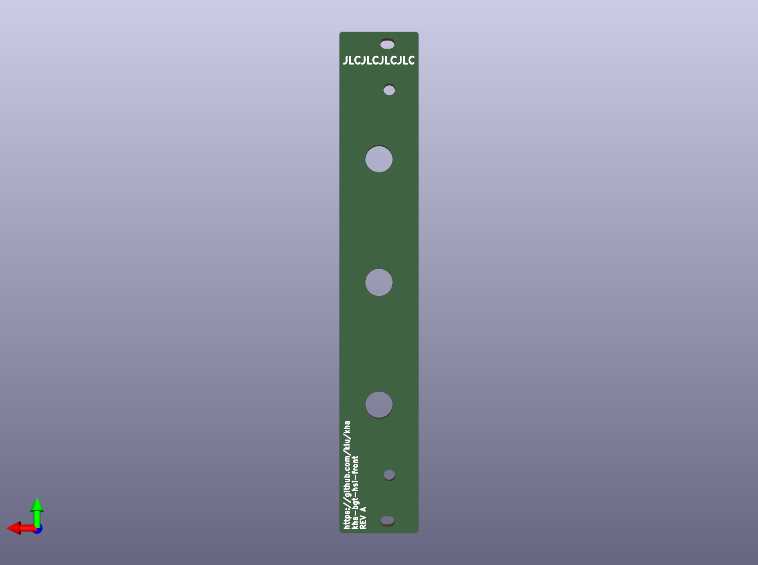
[picture p117: kha-bgt-subrack/kha-bgt-hsi/kha-bgt-hsi-front/kha-bgt-hsi-front-render-back.png]
