kiu/kha/kha-bgt-subrack/kha-bgt-kaox/kha-bgt-kaox-front/README.md

# kha-bgt-kaox-front

Kallax / Oxberg Module Front Panel

## Render

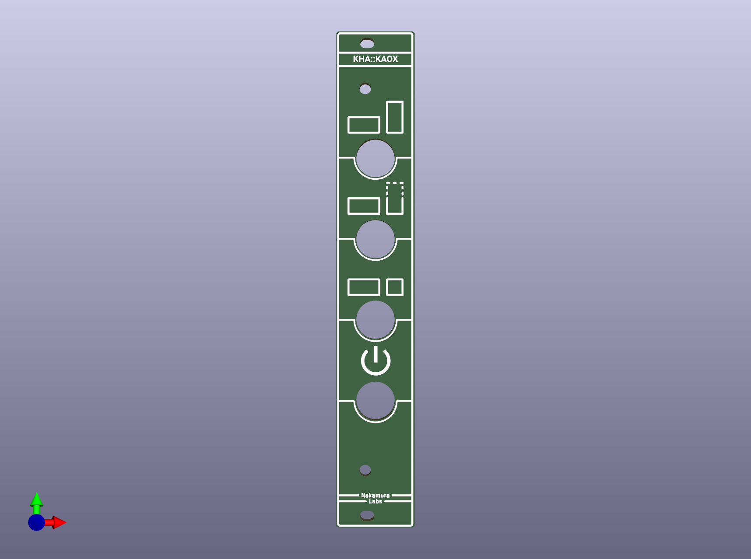
[picture p118: kha-bgt-subrack/kha-bgt-kaox/kha-bgt-kaox-front/kha-bgt-kaox-front-render-front.png]


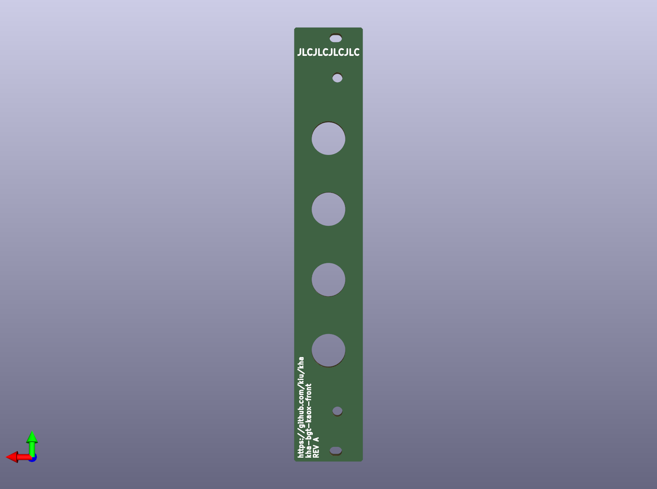
[picture p119: kha-bgt-subrack/kha-bgt-kaox/kha-bgt-kaox-front/kha-bgt-kaox-front-render-back.png]
