kiu/kha/kha-bgt-subrack/kha-bgt-preset/kha-bgt-preset-front/README.md

# kha-bgt-preset

Preset Module Front Panel

## Render

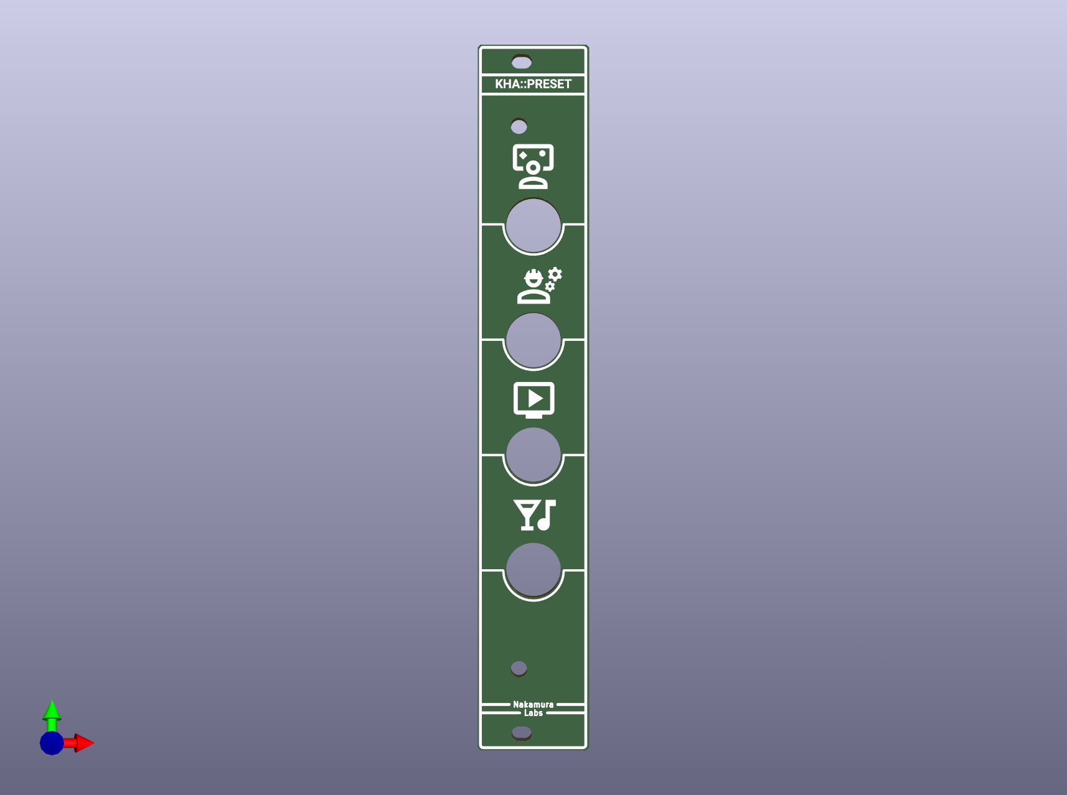
[picture p120: kha-bgt-subrack/kha-bgt-preset/kha-bgt-preset-front/kha-bgt-preset-front-render-front.png]


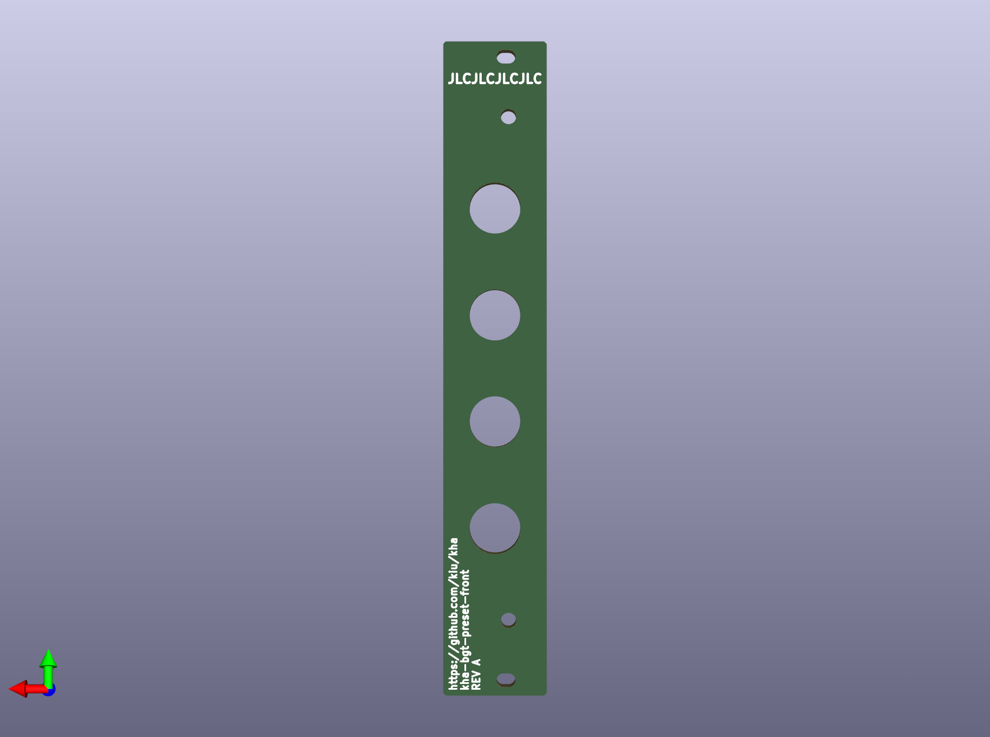
[picture p121: kha-bgt-subrack/kha-bgt-preset/kha-bgt-preset-front/kha-bgt-preset-front-render-back.png]
