kiu/kha/kha-bgt-subrack/kha-bgt-rainbow/kha-bgt-rainbow-front/README.md

# kha-bgt-rainbow-front

Rainbow Animation Module Front Panel

## Render

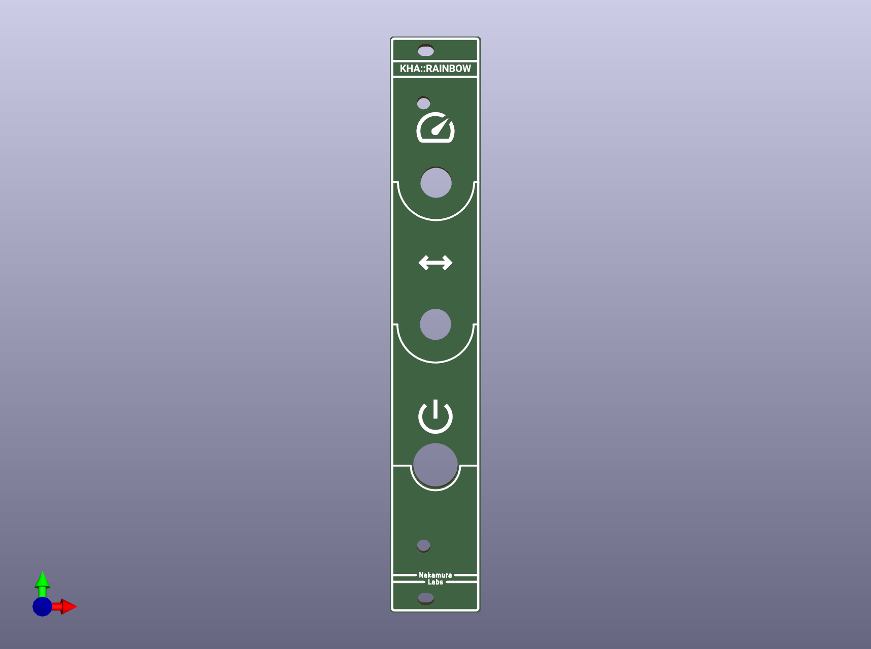
[picture p122: kha-bgt-subrack/kha-bgt-rainbow/kha-bgt-rainbow-front/kha-bgt-rainbow-front-render-front.png]


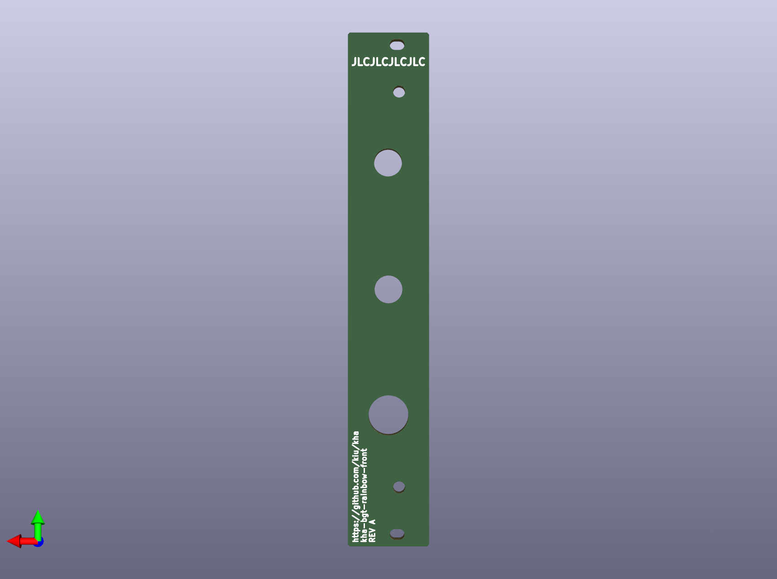
[picture p123: kha-bgt-subrack/kha-bgt-rainbow/kha-bgt-rainbow-front/kha-bgt-rainbow-front-render-back.png]
