kiu/kha/superseded/kha-bgt-rack/kha-bgt-backplane-64/README.md

# superseded

Superseded Ideas / Failed Hardware Revisions

64P full size connector backplane

## Render

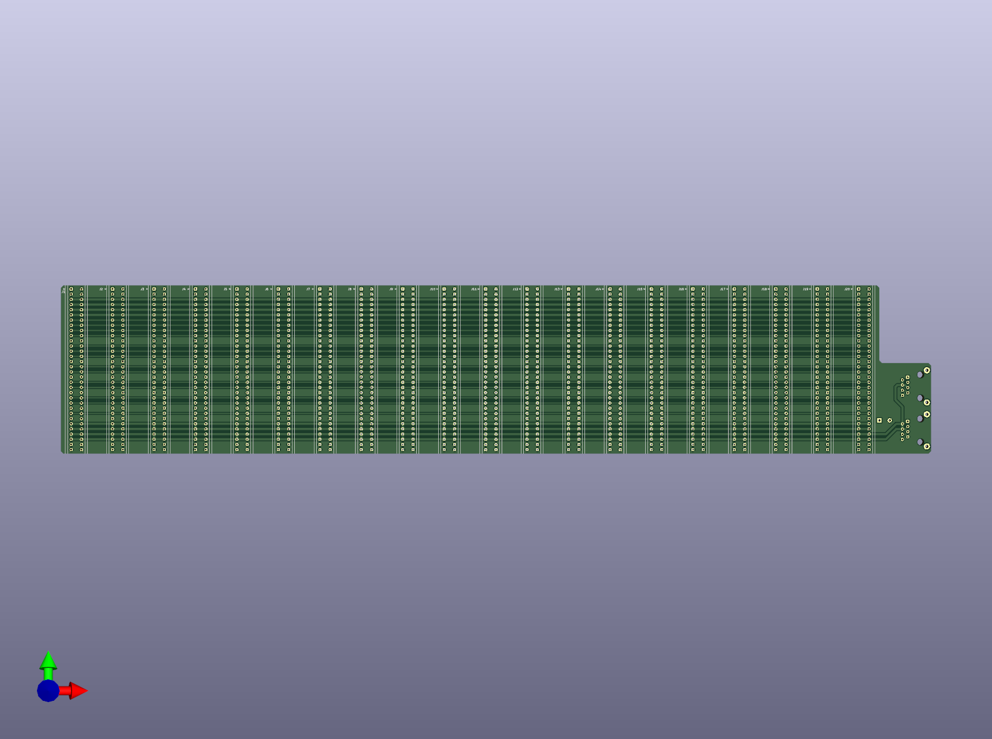
[picture p124: superseded/kha-bgt-rack/kha-bgt-backplane-64/kha-bgt-backplane-64-render-front.png]


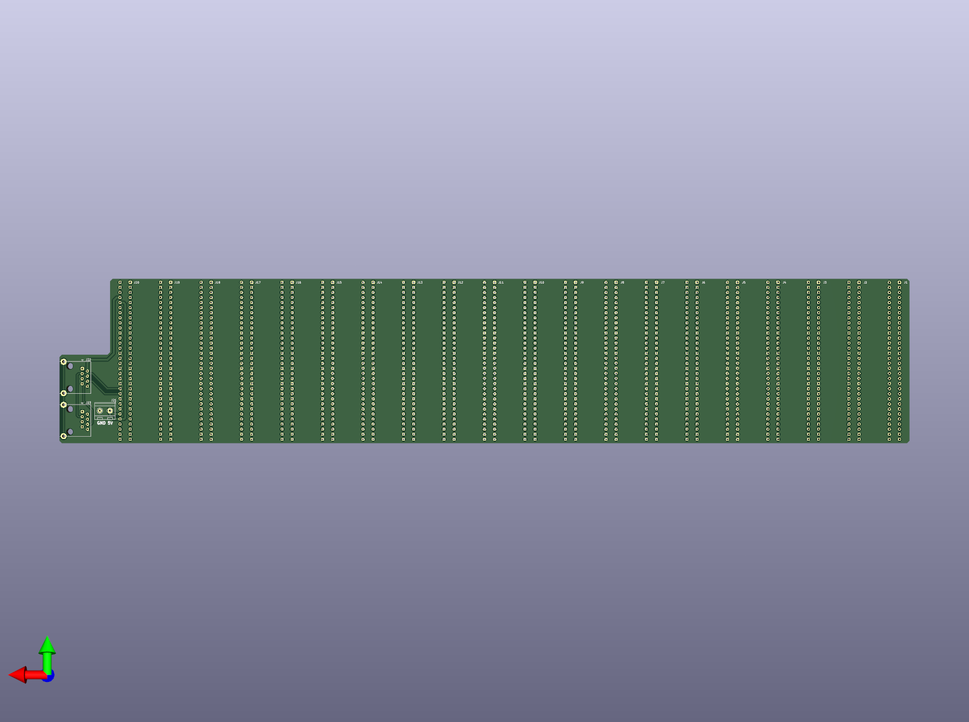
[picture p125: superseded/kha-bgt-rack/kha-bgt-backplane-64/kha-bgt-backplane-64-render-back.png]
