kiu/kha/superseded/kha-bgt-rack/kha-bgt-backplane-mini/README.md

# superseded

Superseded Ideas / Failed Hardware Revisions

20P mini size connector backplane

## Render

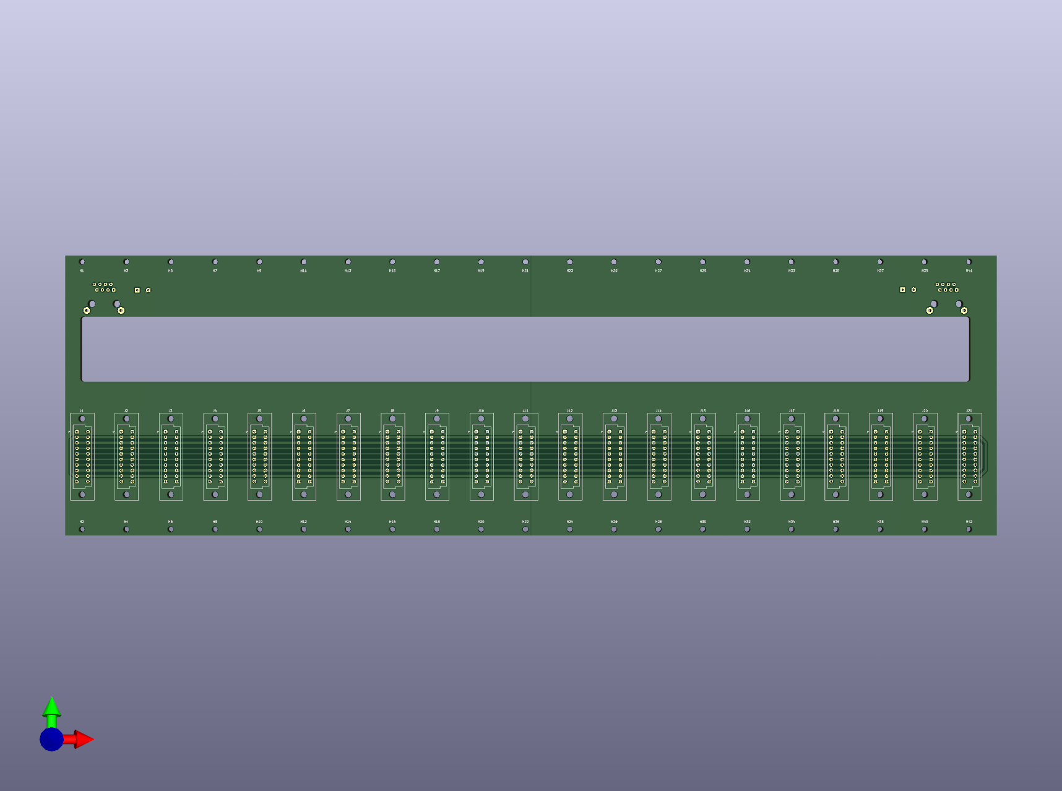
[picture p126: superseded/kha-bgt-rack/kha-bgt-backplane-mini/kha-bgt-backplane-mini-render-front.png]


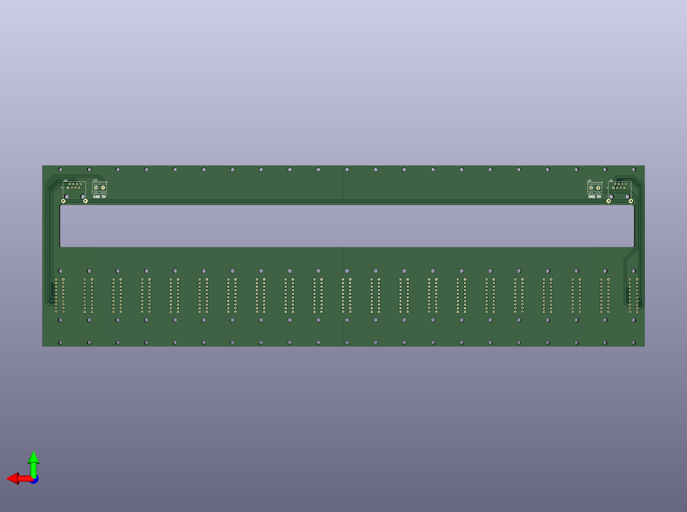
[picture p127: superseded/kha-bgt-rack/kha-bgt-backplane-mini/kha-bgt-backplane-mini-render-back.png]
