kiu/kha/datasheets/rack/R6077214-02.jpg

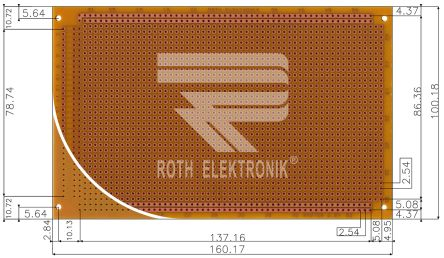
datasheets/rack/R6077214-02.jpg
