kiu/kha/kha-bgt-rack/kha-bgt-cover/kicad/res/kha-cover-art.png

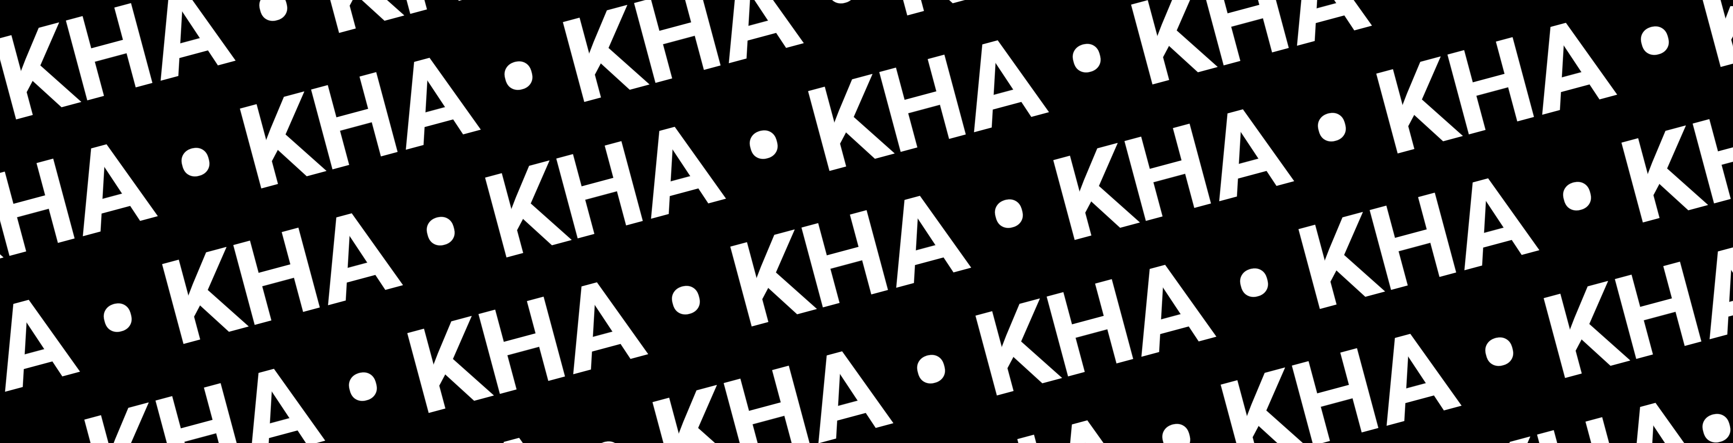
kha-bgt-rack/kha-bgt-cover/kicad/res/kha-cover-art.png
