kiu/kha/kha-nodes/kha-led-ikea/kha-led-ikea-node/kha-led-ikea-node-enclosure-top.stl

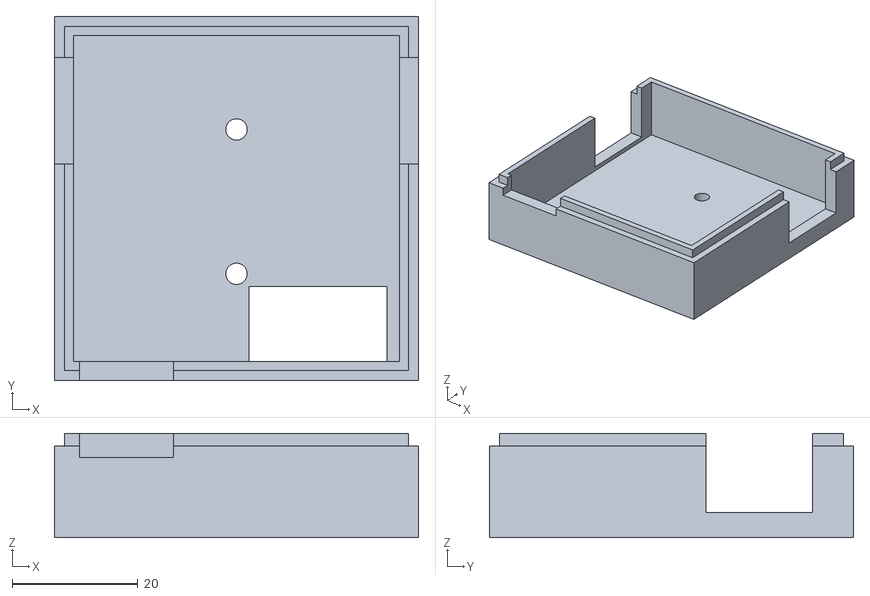
[picture p144: CAD file, 2024-02-18]
kha-nodes/kha-led-ikea/kha-led-ikea-node/kha-led-ikea-node-enclosure-top.stl
58.0 x 58.0 x 16.6
