kiu/kha/kha-nodes/kha-pwr-rj45/kha-pwr-rj45-enclosure-bottom.stl

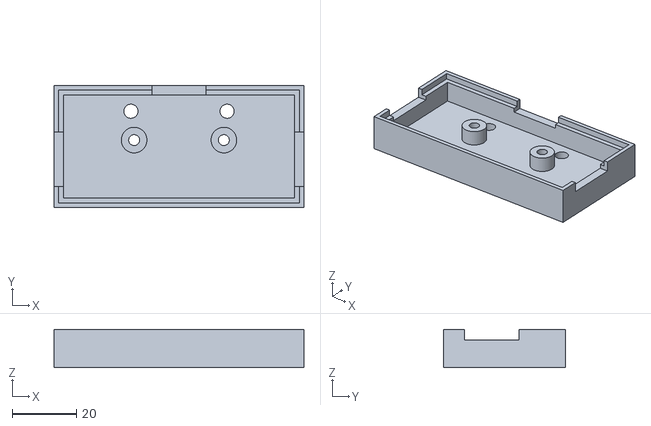
[picture p145: CAD file, 2024-02-17]
kha-nodes/kha-pwr-rj45/kha-pwr-rj45-enclosure-bottom.stl
78.0 x 38.0 x 12.0
