kiu/kha/kha-nodes/kha-pwr-rj45/kha-pwr-rj45-enclosure.stl

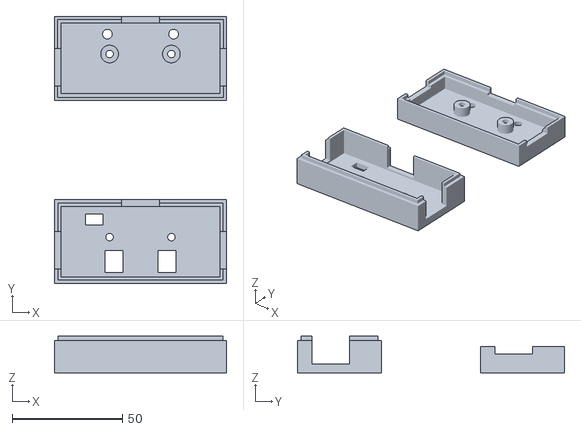
[picture p146: CAD file, 2024-02-17]
kha-nodes/kha-pwr-rj45/kha-pwr-rj45-enclosure.stl
78.0 x 121.0 x 16.6
