kiu/kha/kha-bgt-subrack/kha-bgt-audio/kha-bgt-audio-base/kicad/kha-bgt-audio-base.kicad_pcb

## KiCad design kha-bgt-subrack/kha-bgt-audio/kha-bgt-audio-base/kicad/kha-bgt-audio-base.kicad_pcb (2024-02-18)

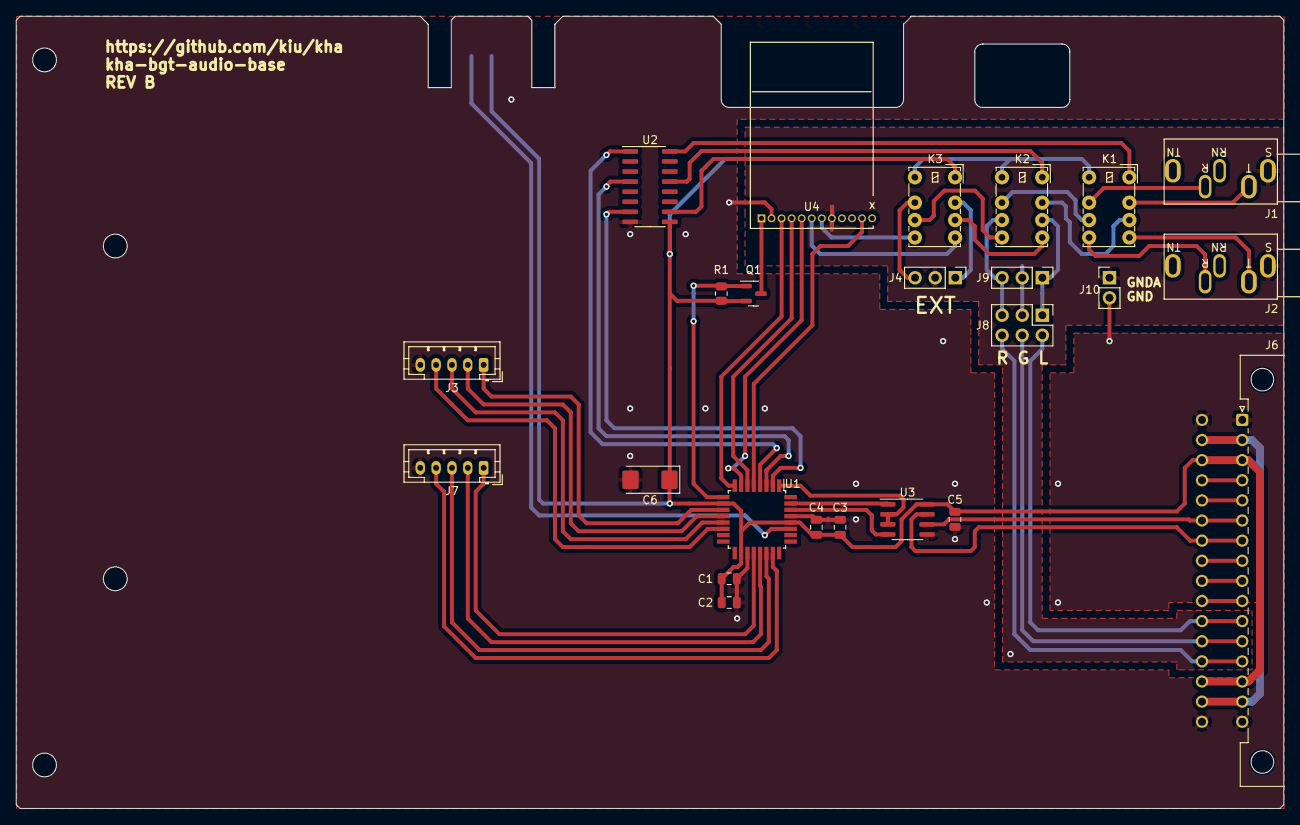
[picture p159: board kha-bgt-audio-base.kicad_pcb from above]

Board: 2 copper layers, 160.0 x 100.0 mm, 25 parts (1 on the bottom side), 52 nets.

Parts:
C1, C4: 10nF; C_0805_2012Metric
C2, C3, C5: 100nF; C_0805_2012Metric
C6: 220uF; CP_EIA-6032-28_Kemet-C
J1, J2: AudioJack3; PJ-325C5
J3, J7: Conn_01x05; JST_PH_B5B-PH-K_1x05_P2.00mm_Vertical
J4, J9: Conn_01x03; PinHeader_1x03_P2.54mm_Vertical
J5: AVR-UPDI-6; eAVR6-UPDI-F
J6: DIN41612_02x16_AC; DIN41612_C2_2x16_Male_Horizontal_THT
J8: Conn_02x03_Odd_Even; PinHeader_2x03_P2.54mm_Vertical
J10: 1x02_Jumper; PinHeader_1x02_P2.54mm_Vertical
K1, K2, K3: HFD4/5; Relay_DPDT_HDF4-5
Q1: DMG2301L; SOT-23
R1: 10k; R_0805_2012Metric
U1: AVR64DD32; TQFP-32_7x7mm_P0.8mm
U2: ULN2003; SOP-16_3.9x9.9mm_P1.27mm
U3: SP481E; SOIC-8_3.9x4.9mm_P1.27mm
U4: KCX_BT_EMITTER_1.7; KCX_BT_EMITTER_V1.7 12P

Connections:
+5V: C1.1, C2.1, C3.1, C4.1, C5.1, C6.1, J5.2 (VCC), J6.a3, J6.a14, J6.c3, J6.c14, K1.8, K2.8, K3.8, Q1.2 (S), R1.1, U1.10 (VDDIO2), U1.18 (VDD), U1.28 (VDD), U2.9 (COM), U3.8 (VCC)
+12V: J6.a2, J6.a15, J6.c2, J6.c15
AUDIO_LEFT: J8.1, J9.1, K2.3
AUDIO_RIGHT: J8.5, J9.3, K2.6
BTN01: J3.1, U1.11 (PD1)
BTN02: J3.3, U1.13 (PD3)
BTN03: J7.1, U1.20 (XTAL32K1/PF0)
BTN04: J7.3, U1.22 (PF2)
BT_CON: U1.5 (PA7), U4.11 (CON)
BT_LNK: U1.8 (PC2), U4.3 (LINK)
BT_RX: U1.6 (PC0), U4.4 (RX)
BT_TX: U1.7 (PC1), U4.5 (TX)
BT_VCC: Q1.3 (D), U4.1 (+5V)
BUS01: J6.a8, J6.c8
BUS02: J6.a9, J6.c9
BUS03: J6.a10, J6.c10
BUS04: J6.a11, J6.c11, J8.2
BUS05: J6.a12, J6.c12, J8.4
BUS06: J6.a13, J6.c13, J8.6
BUS_DIR: U1.1 (PA3), U3.2 (~RE), U3.3 (DE)
BUS_RX: U1.31 (PA1), U3.1 (RO)
BUS_TX: U1.30 (EXTCLK/PA0), U3.4 (DI)
GND: C1.2, C2.2, C3.2, C4.2, C5.2, C6.2, J3.5, J5.6 (GND), J6.a1, J6.a16, J6.c1, J6.c16, J7.5, J10.2, U1.19 (GND), U1.29 (GND), U2.8 (GND), U3.5 (GND), U4.2 (GND)
GNDA: J1.S, J2.S, J4.2, J8.3, J9.2, J10.1, U4.8 (AGND)
LED01: J3.2, U1.12 (PD2)
LED02: J3.4, U1.14 (PD4)
LED03: J7.2, U1.21 (XTAL32K2/PF1)
LED04: J7.4, U1.23 (PF3)
unnamed: J1.R, K1.7
unnamed: J1.T, K1.2
unnamed: J2.R, K1.5
unnamed: J2.T, K1.4
unnamed: J4.1, K3.2
unnamed: J4.3, K3.7
unnamed: K1.3, K2.2
unnamed: K1.6, K2.7
unnamed: K2.4, K3.3
unnamed: K2.5, K3.6
unnamed: K3.4, U4.6 (LEFT)
unnamed: K3.5, U4.7 (RIGHT)
R01: K1.1, U2.16 (O1)
R02: K3.1, U2.10 (O7)
R03: K2.1, U2.13 (O4)
RS485_A: J6.a6, J6.c6, U3.6 (A)
RS485_B: J6.a7, J6.c7, U3.7 (B)
RS485_INT_A: J6.a4, J6.c4
RS485_INT_B: J6.a5, J6.c5
SR01: U1.4 (PA6), U2.1 (I1)
SR02: U1.2 (PA4), U2.7 (I7)
SR03: U1.3 (PA5), U2.4 (I4)
S_BT_VCC: Q1.1 (G), R1.2, U1.9 (PC3)
UPDI: J5.1 (DATA), U1.27 (PF7/UPDI)
