kiu/kha/kha-bgt-subrack/kha-bgt-audio/kha-bgt-audio-sub/kicad/kha-bgt-audio-sub.kicad_pcb

## KiCad design kha-bgt-subrack/kha-bgt-audio/kha-bgt-audio-sub/kicad/kha-bgt-audio-sub.kicad_pcb (2024-02-18)

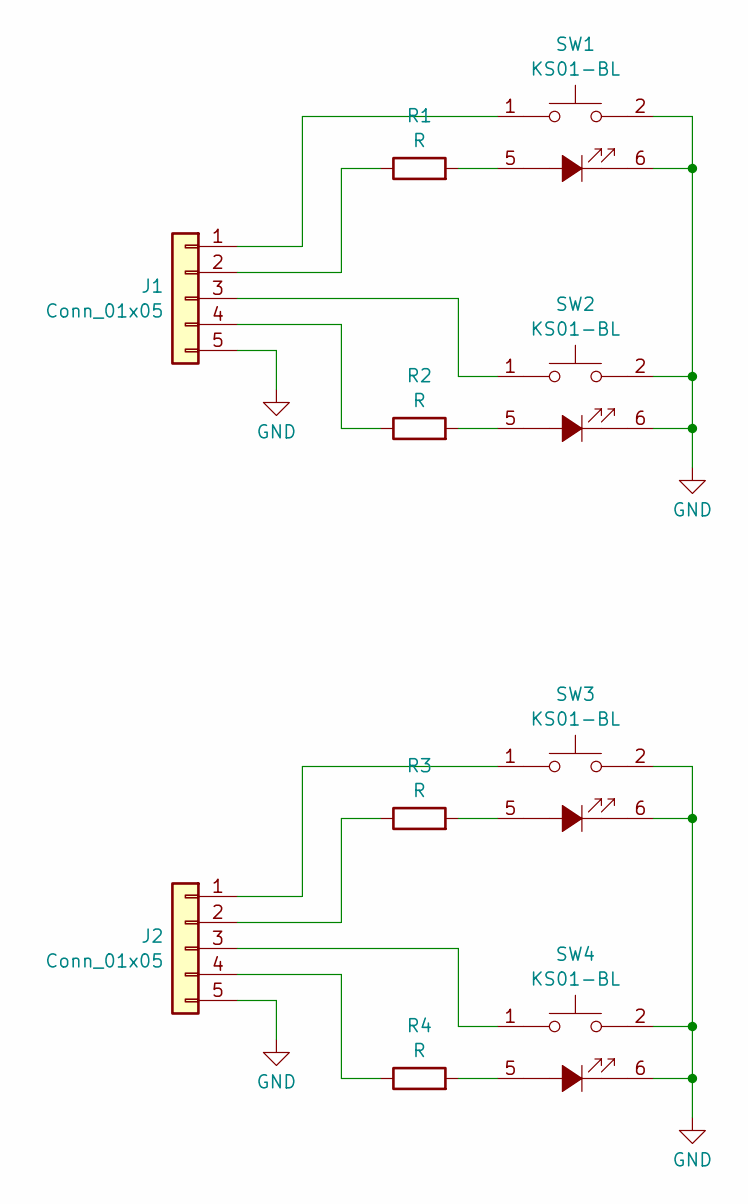
[picture p160: schematic kha-bgt-audio-sub.kicad_sch]

Parts:
J1, J2: Conn_01x05; JST_PH_B5B-PH-K_1x05_P2.00mm_Vertical
R1, R2, R3, R4: R; R_0805_2012Metric
SW1, SW2, SW3, SW4: KS01-BL

Connections:
GND: J1.5, J2.5, SW1.2, SW1.6, SW2.2, SW2.6, SW3.2, SW3.6, SW4.2, SW4.6
unnamed: J1.1, SW1.1
unnamed: J1.2, R1.1
unnamed: J1.3, SW2.1
unnamed: J1.4, R2.1
unnamed: J2.1, SW3.1
unnamed: J2.2, R3.1
unnamed: J2.3, SW4.1
unnamed: J2.4, R4.1
unnamed: R1.2, SW1.5
unnamed: R2.2, SW2.5
unnamed: R3.2, SW3.5
unnamed: R4.2, SW4.5

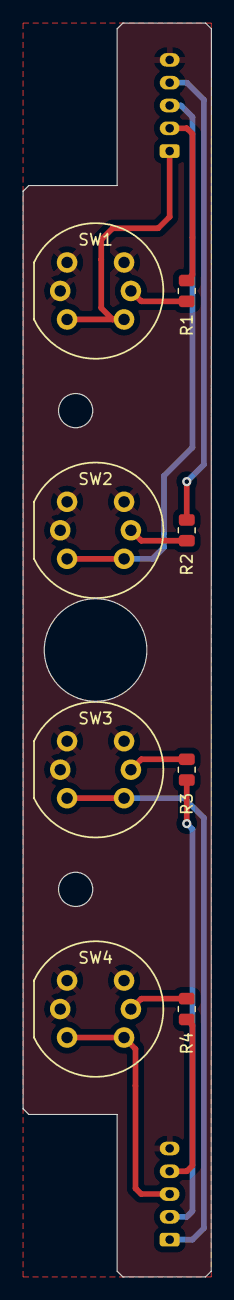
[picture p161: board kha-bgt-audio-sub.kicad_pcb from above]

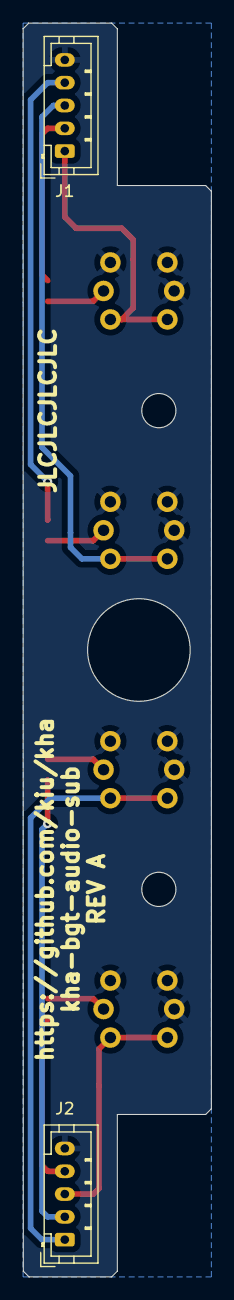
[picture p162: board kha-bgt-audio-sub.kicad_pcb from below]

Board: 2 copper layers, 16.5 x 110.0 mm, 10 parts (2 on the bottom side), 13 nets.
