kiu/kha/kha-bgt-subrack/kha-bgt-rainbow/kha-bgt-rainbow-sub/kicad/kha-bgt-rainbow-sub.kicad_pcb

## KiCad design kha-bgt-subrack/kha-bgt-rainbow/kha-bgt-rainbow-sub/kicad/kha-bgt-rainbow-sub.kicad_pcb (2024-02-18)

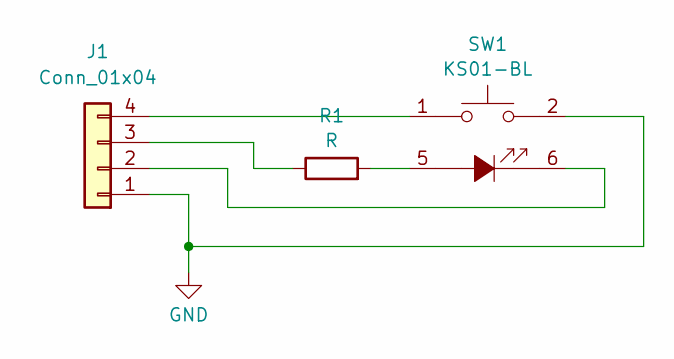
[picture p165: schematic kha-bgt-rainbow-sub.kicad_sch]

Parts:
J1: Conn_01x04; JST_PH_B4B-PH-K_1x04_P2.00mm_Vertical
R1: R; R_0805_2012Metric
SW1: KS01-BL

Connections:
GND: J1.1, SW1.2
unnamed: J1.2, SW1.6
unnamed: J1.3, R1.1
unnamed: J1.4, SW1.1
unnamed: R1.2, SW1.5

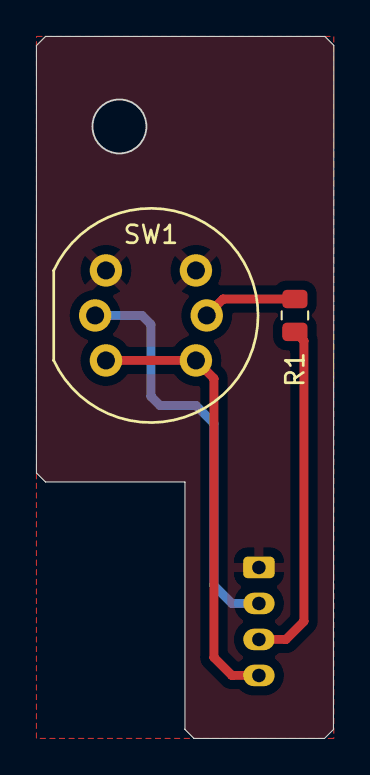
[picture p166: board kha-bgt-rainbow-sub.kicad_pcb from above]

Board: 2 copper layers, 16.5 x 39.0 mm, 3 parts (1 on the bottom side), 5 nets.
