kiu/kha/kha-nodes/kha-led-ikea/kha-led-ikea-lighting/kha-led-ikea-term/kicad/kha-led-ikea-term.kicad_pcb

## KiCad design kha-nodes/kha-led-ikea/kha-led-ikea-lighting/kha-led-ikea-term/kicad/kha-led-ikea-term.kicad_pcb (2024-02-18)

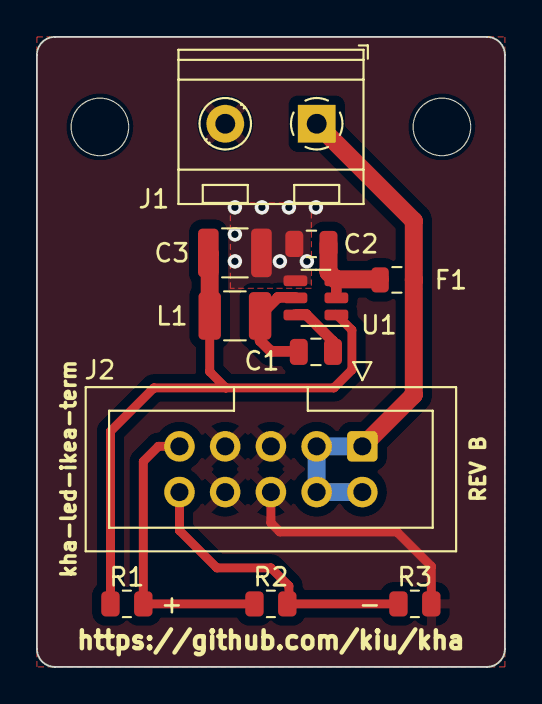
[picture p167: board kha-led-ikea-term.kicad_pcb from above]

Board: 2 copper layers, 26.0 x 35.0 mm, 13 parts (0 on the bottom side), 8 nets.

Parts:
C1: 100nF; C_0805_2012Metric
C2: 10uF; C_0805_2012Metric
C3: 47uF; C_1210_3225Metric
F1: Polyfuse; Fuse_0805_2012Metric
H1, H2: MountingHole; MountingHole_3.2mm_M3
J1: Screw_Terminal_01x02; TerminalBlock_RND_205-00232_1x02_P5.08mm_Horizontal
J2: Conn_01x10; IDC-Header_2x05_P2.54mm_Vertical
L1: 4.7uH; L_1210_3225Metric
R1, R2, R3: R; R_0805_2012Metric
U1: AP63205WU; TSOT-23-6

Connections:
+5V: C3.1, L1.2, R1.1, U1.1 (FB)
+12V: F1.2, J1.1, J2.1, J2.2, J2.3, J2.4
GND: C2.1, C3.2, J1.2, J2.5, J2.6, J2.7, J2.8, R3.2, U1.4 (GND)
unnamed: J2.9, R1.2, R2.1
unnamed: J2.10, R2.2, R3.1
unnamed: C1.2, U1.6 (BST)
unnamed: C2.2, F1.1, U1.2 (EN), U1.3 (IN)
unnamed: C1.1, L1.1, U1.5 (SW)
