kiu/kha/kha-nodes/kha-relay-2x3/kha-relay-2x3-box/kha-relay-2x3-base/kicad/kha-relay-2x3-base.kicad_pcb

## KiCad design kha-nodes/kha-relay-2x3/kha-relay-2x3-box/kha-relay-2x3-base/kicad/kha-relay-2x3-base.kicad_pcb (2024-02-18)

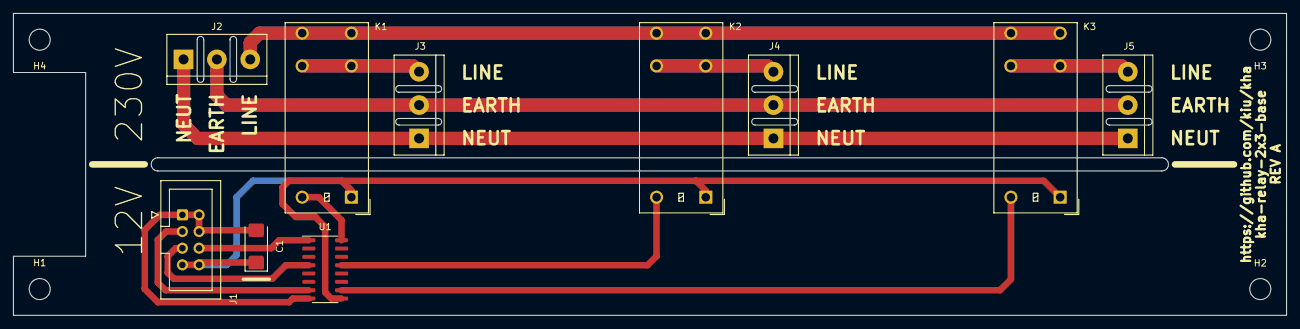
[picture p168: board kha-relay-2x3-base.kicad_pcb from above]

Board: 2 copper layers, 194.0 x 46.0 mm, 14 parts (0 on the bottom side), 14 nets.

Parts:
C1: 220uF; CP_EIA-6032-28_Kemet-C
H1, H2, H3, H4: MountingHole; MountingHole_3.2mm_M3_DIN965
J1: Conn_02x04_Odd_Even; IDC-Header_2x04_P2.54mm_Vertical
J2, J3, J4, J5: Conn_01x03; TerminalBlock_bornier-3_P5.08mm
K1, K2, K3: G2RL-1A-E; Relay_SPST_Omron_G2RL-1A-E
U1: ULN2003; SOP-16_3.9x9.9mm_P1.27mm

Connections:
+12V: C1.1, J1.7, J1.8, K1.A1, K2.A1, K3.A1, U1.9 (COM)
Earth: J2.2, J3.2, J4.2, J5.2
GND: C1.2, J1.1, J1.2, J1.4, U1.8 (GND)
LINE: J2.3, K1.14, K2.14, K3.14
NEUT: J2.1, J3.1, J4.1, J5.1
unnamed: J1.3, U1.7 (I7)
unnamed: J1.5, U1.4 (I4)
unnamed: J1.6, U1.1 (I1)
unnamed: J3.3, K1.13
unnamed: J4.3, K2.13
unnamed: J5.3, K3.13
R01: K1.A2, U1.16 (O1)
R02: K2.A2, U1.13 (O4)
R03: K3.A2, U1.10 (O7)
