kiu/kha/kha-nodes/kha-led-ikea/kha-led-ikea-node/kicad/kha-led-ikea-node.kicad_pcb

## KiCad design kha-nodes/kha-led-ikea/kha-led-ikea-node/kicad/kha-led-ikea-node.kicad_pcb (2024-02-18)

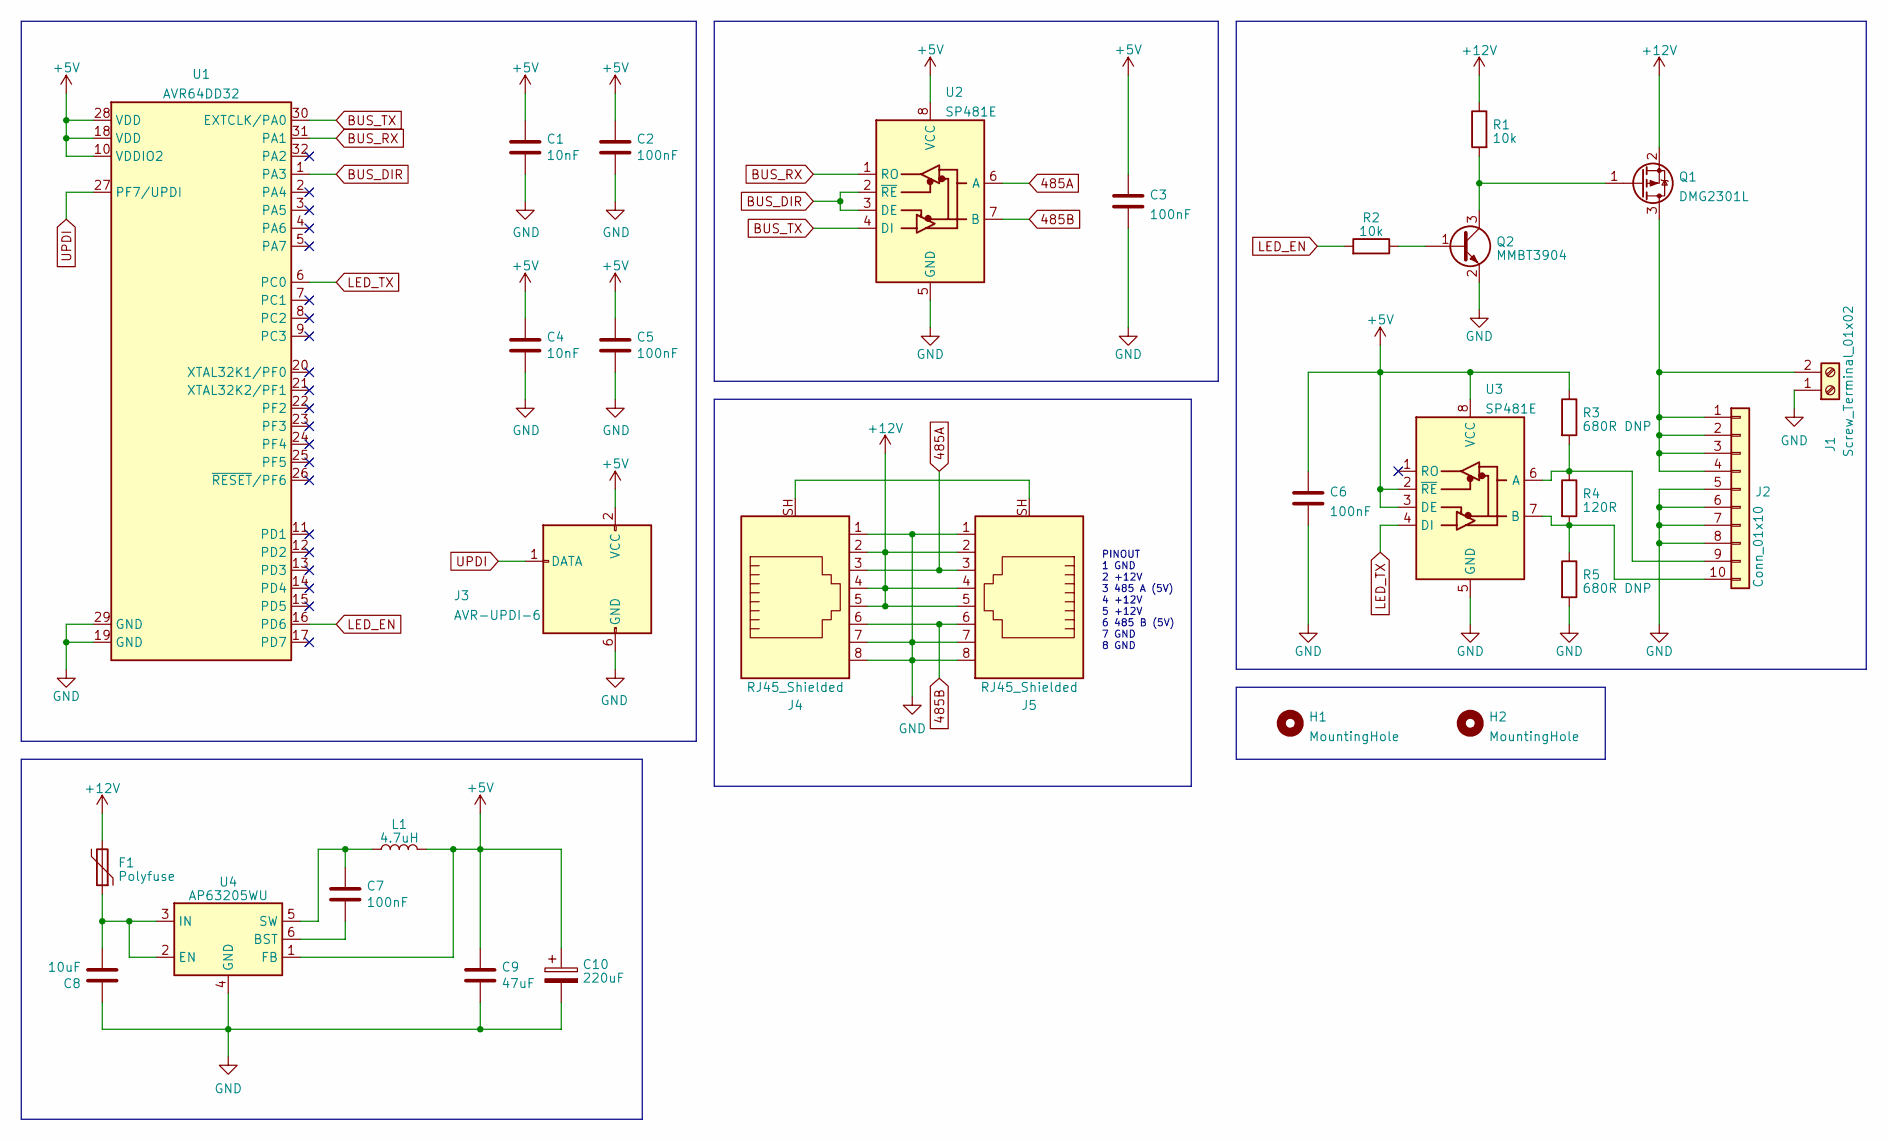
[picture p169: schematic kha-led-ikea-node.kicad_sch]

Parts:
C1, C4: 10nF; C_0805_2012Metric
C2, C3, C5, C6, C7: 100nF; C_0805_2012Metric
C8: 10uF; C_0805_2012Metric
C9: 47uF; C_1210_3225Metric
C10: 220uF; CP_EIA-6032-28_Kemet-C
F1: Polyfuse; Fuse_0805_2012Metric
H1, H2: MountingHole; MountingHole_3.2mm_M3_DIN965
J1: Screw_Terminal_01x02; TerminalBlock_bornier-2_P5.08mm
J2: Conn_01x10; IDC-Header_2x05_P2.54mm_Vertical
J3: AVR-UPDI-6; eAVR6-UPDI-F
J4, J5: RJ45_Shielded; GDLX-S-88K
L1: 4.7uH; L_1210_3225Metric
Q1: DMG2301L; SOT-23
Q2: MMBT3904; SOT-23
R1, R2: 10k; R_0805_2012Metric
R3, R5: 680R DNP; R_0805_2012Metric
R4: 120R; R_0805_2012Metric
U1: AVR64DD32; TQFP-32_7x7mm_P0.8mm
U2, U3: SP481E; SOIC-8_3.9x4.9mm_P1.27mm
U4: AP63205WU; TSOT-23-6

Connections:
485A: J4.3, J5.3, U2.6 (A)
485B: J4.6, J5.6, U2.7 (B)
+5V: C1.1, C2.1, C3.1, C4.1, C5.1, C6.1, C9.1, C10.1, J3.2 (VCC), L1.2, R3.1, U1.10 (VDDIO2), U1.18 (VDD), U1.28 (VDD), U2.8 (VCC), U3.2 (~RE), U3.3 (DE), U3.8 (VCC), U4.1 (FB)
+12V: F1.2, J4.2, J4.4, J4.5, J5.2, J5.4, J5.5, Q1.2 (S), R1.1
BUS_DIR: U1.1 (PA3), U2.2 (~RE), U2.3 (DE)
BUS_RX: U1.31 (PA1), U2.1 (RO)
BUS_TX: U1.30 (EXTCLK/PA0), U2.4 (DI)
GND: C1.2, C2.2, C3.2, C4.2, C5.2, C6.2, C8.1, C9.2, C10.2, J1.1, J2.5, J2.6, J2.7, J2.8, J3.6 (GND), J4.1, J4.7, J4.8, J5.1, J5.7, J5.8, Q2.2 (E), R5.2, U1.19 (GND), U1.29 (GND), U2.5 (GND), U3.5 (GND), U4.4 (GND)
LED_EN: R2.2, U1.16 (PD6)
LED_TX: U1.6 (PC0), U3.4 (DI)
unnamed: J1.2, J2.1, J2.2, J2.3, J2.4, Q1.3 (D)
unnamed: J2.9, R3.2, R4.1, U3.6 (A)
unnamed: J2.10, R4.2, R5.1, U3.7 (B)
unnamed: J4.SH, J5.SH
unnamed: Q1.1 (G), Q2.3 (C), R1.2
unnamed: Q2.1 (B), R2.1
unnamed: C7.2, U4.6 (BST)
unnamed: C8.2, F1.1, U4.2 (EN), U4.3 (IN)
unnamed: C7.1, L1.1, U4.5 (SW)
UPDI: J3.1 (DATA), U1.27 (PF7/UPDI)

Notes on the sheet:
PINOUT 1 GND 2 +12V 3 485 A (5V) 4 +12V 5 +12V 6 485 B (5V) 7 GND 8 GND

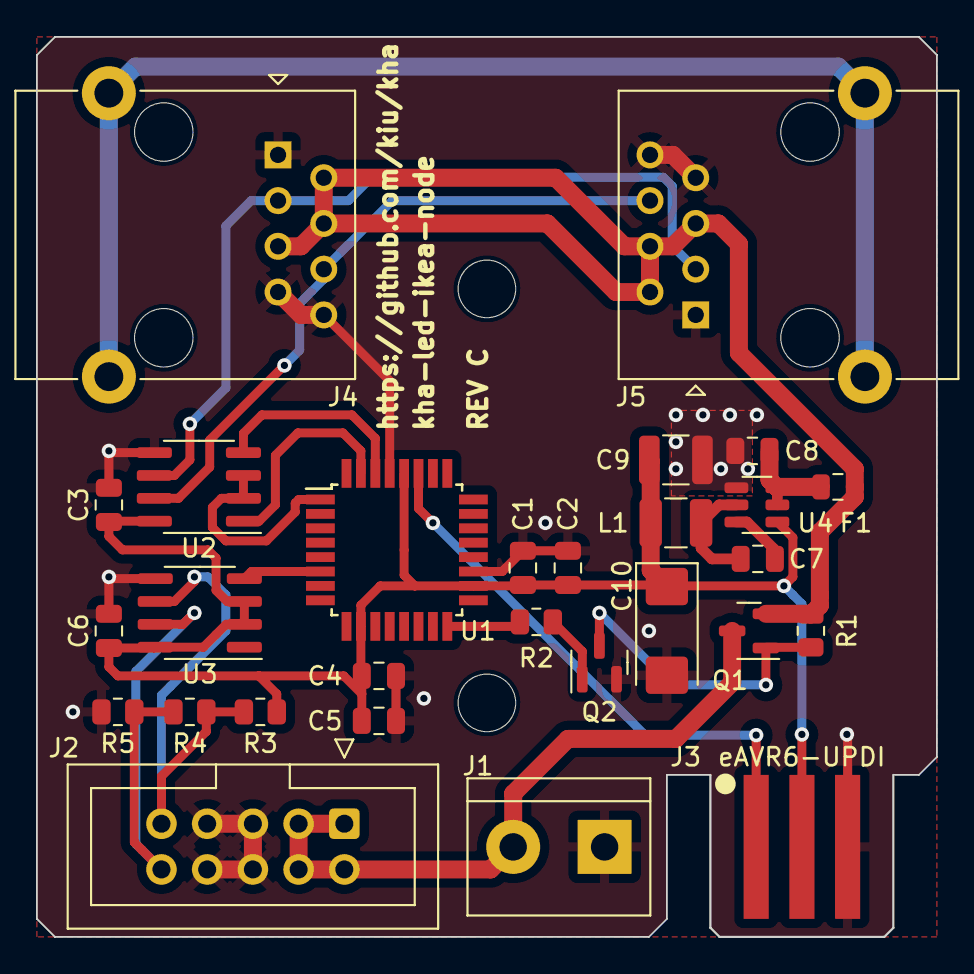
[picture p170: board kha-nodes/kha-led-ikea/kha-led-ikea-node/kicad/kha-led-ikea-node.kica… from above]

Board: 2 copper layers, 50.0 x 50.0 mm, 30 parts (0 on the bottom side), 20 nets.
