kiu/kha/kha-bgt-subrack/kha-bgt-guru/kha-bgt-guru-front/kicad/kha-bgt-guru-front.kicad_pcb

## KiCad design kha-bgt-subrack/kha-bgt-guru/kha-bgt-guru-front/kicad/kha-bgt-guru-front.kicad_pcb (2024-02-18)

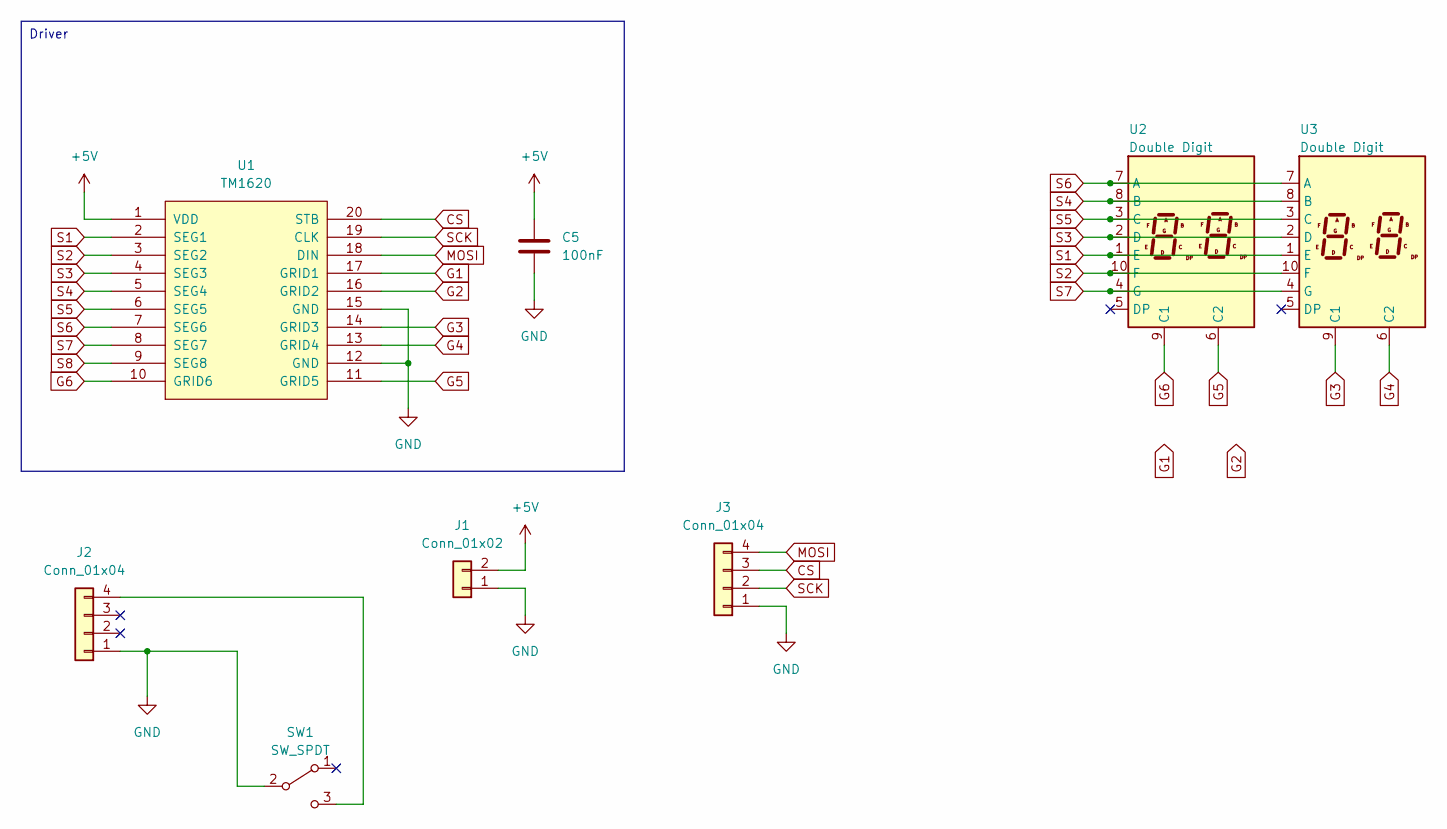
[picture p171: schematic kha-bgt-guru-front.kicad_sch]

Parts:
C5: 100nF; C_0805_2012Metric
J1: Conn_01x02; JST_PH_B2B-PH-SM4-TB_1x02-1MP_P2.00mm_Vertical
J2, J3: Conn_01x04; JST_PH_B4B-PH-SM4-TB_1x04-1MP_P2.00mm_Vertical
SW1: SW_SPDT; PB86
U1: TM1620_[C19579]; SOIC-20W_7.5x12.8mm_P1.27mm
U2, U3: Double Digit; SLR028

Connections:
+5V: C5.1, J1.2, U1.1 (VDD)
CS: J3.3, U1.20 (STB)
G1: U1.17 (GRID1)
G2: U1.16 (GRID2)
G3: U1.14 (GRID3), U3.9 (C1)
G4: U1.13 (GRID4), U3.6 (C2)
G5: U1.11 (GRID5), U2.6 (C2)
G6: U1.10 (GRID6), U2.9 (C1)
GND: C5.2, J1.1, J2.1, J3.1, SW1.2 (B), U1.12 (GND), U1.15 (GND)
MOSI: J3.4, U1.18 (DIN)
unnamed: J2.4, SW1.3 (C)
S1: U1.2 (SEG1), U2.1 (E), U3.1 (E)
S2: U1.3 (SEG2), U2.10 (F), U3.10 (F)
S3: U1.4 (SEG3), U2.2 (D), U3.2 (D)
S4: U1.5 (SEG4), U2.8 (B), U3.8 (B)
S5: U1.6 (SEG5), U2.3 (C), U3.3 (C)
S6: U1.7 (SEG6), U2.7 (A), U3.7 (A)
S7: U1.8 (SEG7), U2.4 (G), U3.4 (G)
S8: U1.9 (SEG8)
SCK: J3.2, U1.19 (CLK)

Notes on the sheet:
Driver

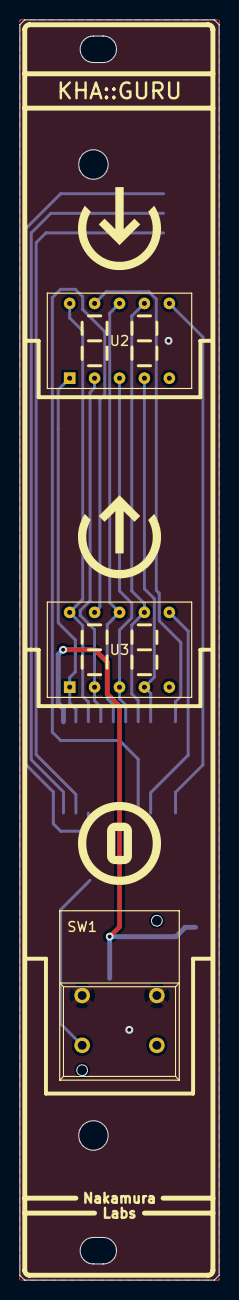
[picture p172: board kha-bgt-guru-front.kicad_pcb from above]

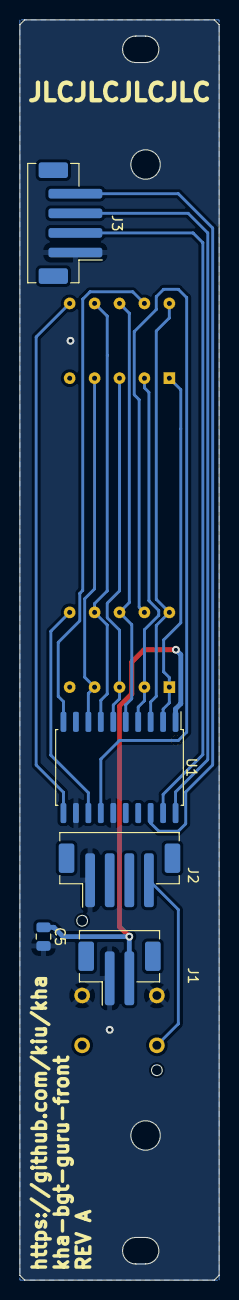
[picture p173: board kha-bgt-guru-front.kicad_pcb from below]

Board: 2 copper layers, 20.3 x 128.5 mm, 8 parts (5 on the bottom side), 17 nets.
