kiu/kha/kha-nodes/kha-pwr-rj45/kicad/kha-pwr-rj45.kicad_pcb

## KiCad design kha-nodes/kha-pwr-rj45/kicad/kha-pwr-rj45.kicad_pcb (2024-02-17)

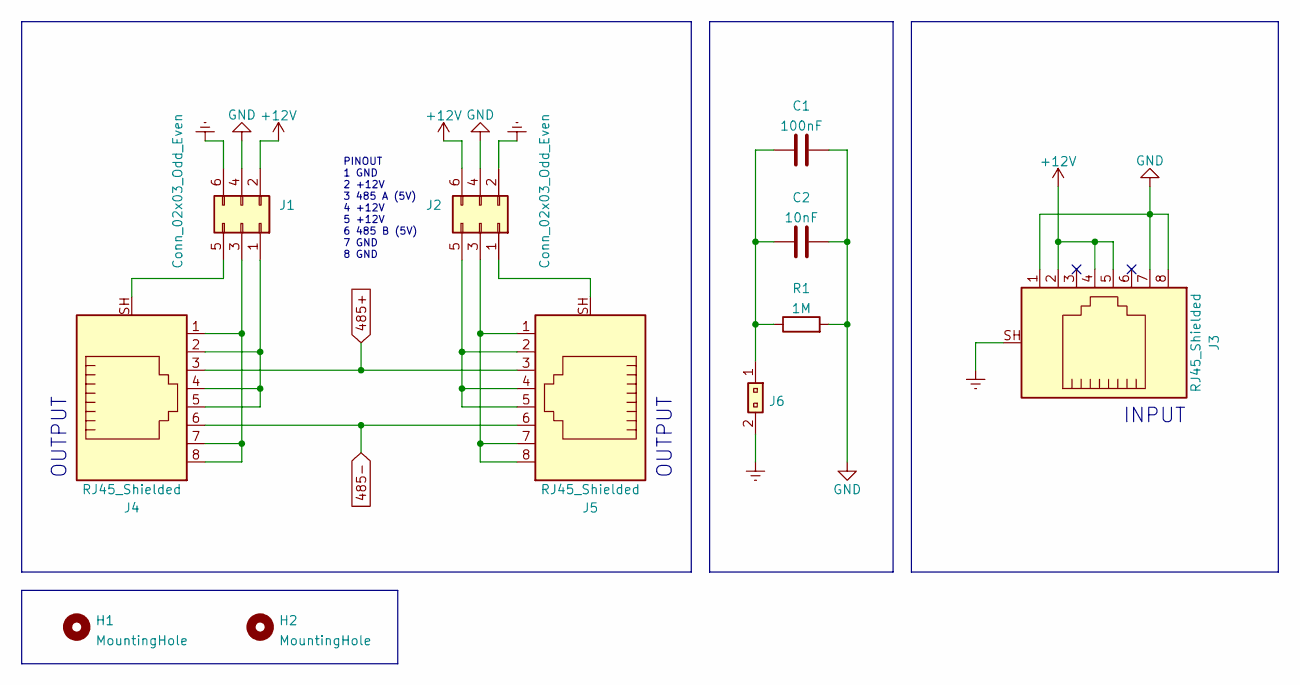
[picture p174: schematic kha-pwr-rj45.kicad_sch]

Parts:
C1: 100nF; C_0805_2012Metric
C2: 10nF; C_0805_2012Metric
H1, H2: MountingHole; MountingHole_3.2mm_M3
J1, J2: Conn_02x03_Odd_Even; PinHeader_2x03_P2.54mm_Vertical
J3, J4, J5: RJ45_Shielded; GDLX-S-88K
J6: 1x02_Jumper; PinHeader_1x02_P2.54mm_Vertical
R1: 1M; R_0805_2012Metric

Connections:
485+: J4.3, J5.3
485-: J4.6, J5.6
+12V: J1.2, J2.6, J3.2, J3.4, J3.5
Earth: J1.6, J2.2, J3.SH, J6.2
GND: C1.2, C2.2, J1.4, J2.4, J3.1, J3.7, J3.8, R1.2
unnamed: C1.1, C2.1, J6.1, R1.1
unnamed: J1.1, J4.2, J4.4, J4.5
unnamed: J1.3, J4.1, J4.7, J4.8
unnamed: J1.5, J4.SH
unnamed: J2.1, J5.SH
unnamed: J2.3, J5.1, J5.7, J5.8
unnamed: J2.5, J5.2, J5.4, J5.5

Notes on the sheet:
PINOUT 1 GND 2 +12V 3 485 A (5V) 4 +12V 5 +12V 6 485 B (5V) 7 GND 8 GND
INPUT
OUTPUT

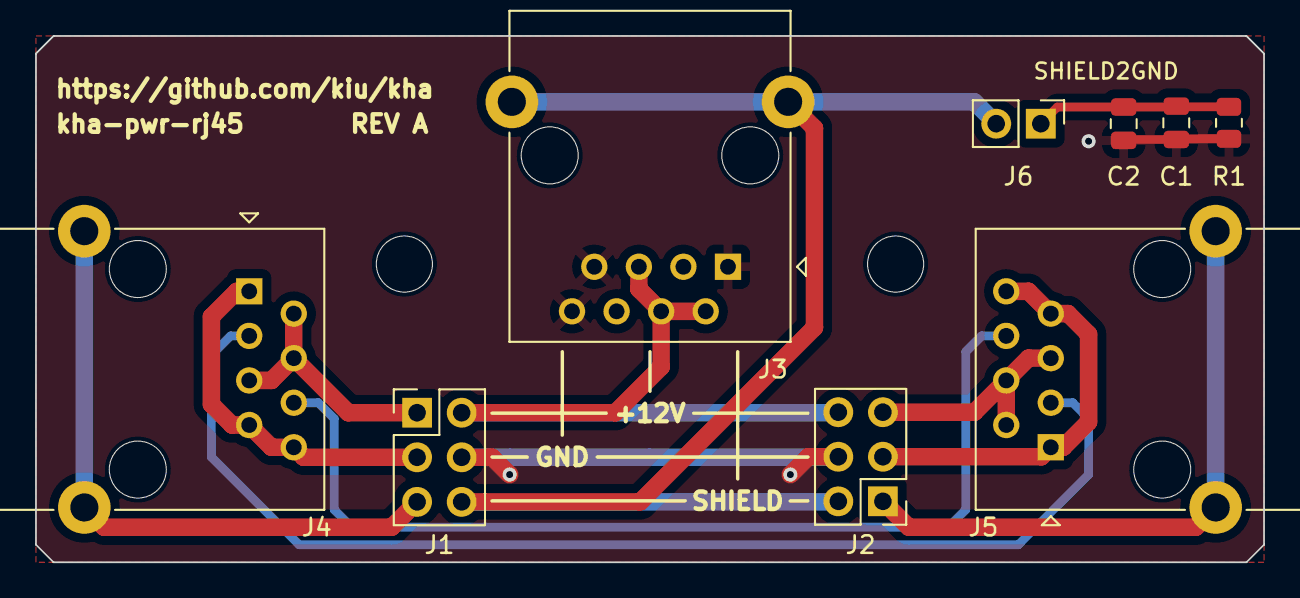
[picture p175: board kha-pwr-rj45.kicad_pcb from above]

Board: 2 copper layers, 70.0 x 30.0 mm, 11 parts (0 on the bottom side), 12 nets.
