kiu/kha/superseded/kha-nodes/kha-led-ikea-node-reva/kicad/kha-led-ikea-node.kicad_pcb

## KiCad design superseded/kha-nodes/kha-led-ikea-node-reva/kicad/kha-led-ikea-node.kicad_pcb (2024-02-16, an earlier design)

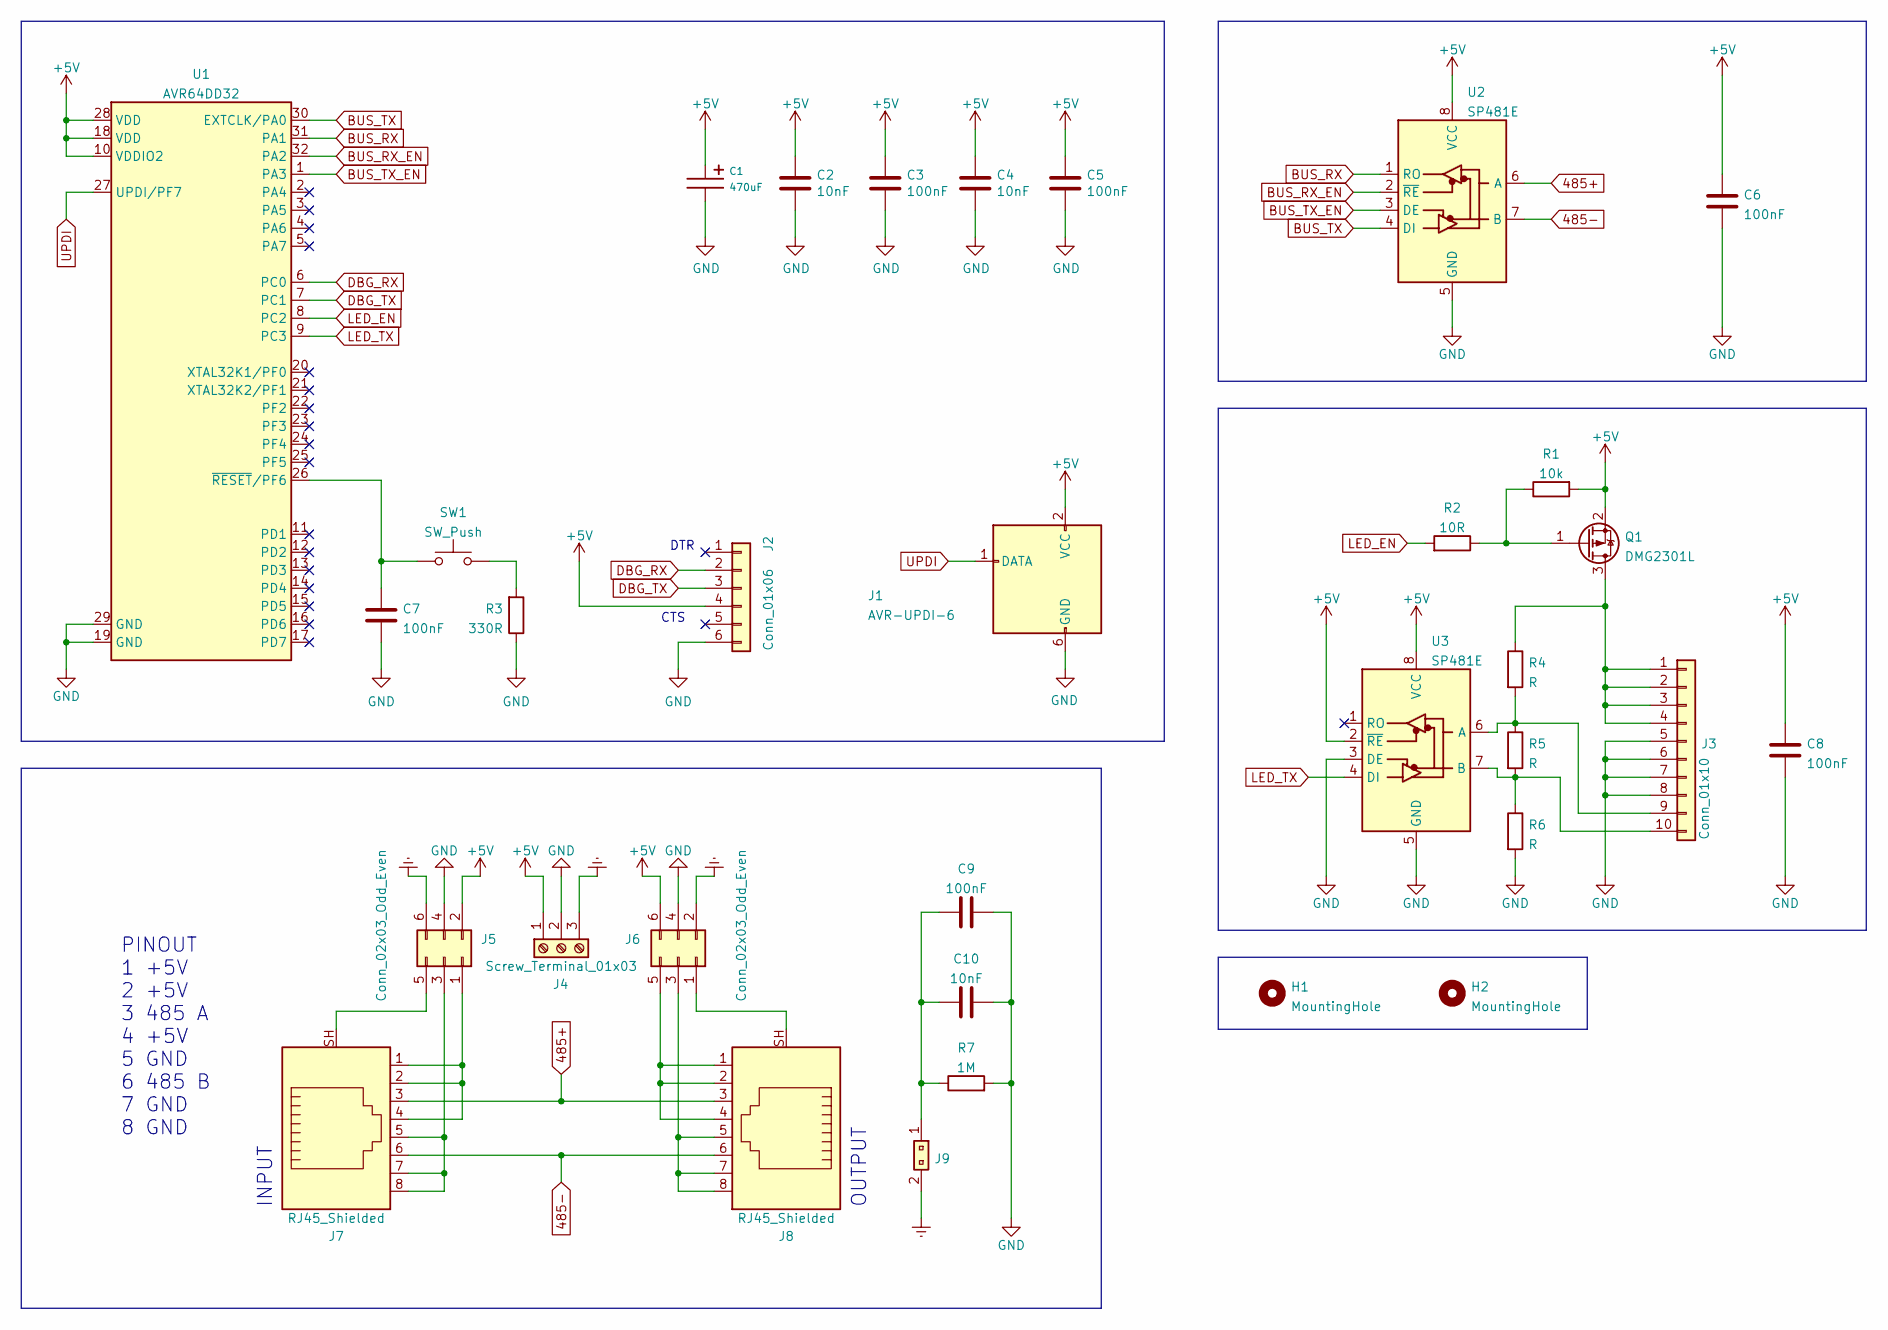
[picture p176: schematic kha-led-ikea-node.kicad_sch]

Parts:
C1: 470uF; CP_Elec_8x10
C2, C4, C10: 10nF; C_0805_2012Metric
C3, C5, C6, C7, C8, C9: 100nF; C_0805_2012Metric
H1, H2: MountingHole; MountingHole_3.2mm_M3
J1: AVR-UPDI-6; eAVR6-UPDI-F
J2: Conn_01x06; PinSocket_1x06_P2.54mm_Vertical
J3: Conn_01x10; IDC-Header_2x05_P2.54mm_Vertical
J4: Screw_Terminal_01x03; TerminalBlock_RND_205-00233_1x03_P5.08mm_Horizontal
J5, J6: Conn_02x03_Odd_Even; PinHeader_2x03_P2.54mm_Vertical
J7, J8: RJ45_Shielded; GDLX-S-88K
J9: 1x02_Jumper; PinHeader_1x02_P2.54mm_Vertical
Q1: DMG2301L; SOT-23
R1: 10k; R_0805_2012Metric
R2: 10R; R_0805_2012Metric
R3: 330R; R_0805_2012Metric
R4, R5, R6: R; R_0805_2012Metric
R7: 1M; R_0805_2012Metric
SW1: SW_Push; SW_Push_1P1T_NO_6x6mm_H9.5mm
U1: AVR64DD32; TQFP-32_7x7mm_P0.8mm
U2, U3: SP481E; SOIC-8_3.9x4.9mm_P1.27mm

Connections:
485+: J7.3, J8.3, U2.6 (A)
485-: J7.6, J8.6, U2.7 (B)
+5V: C1.1, C2.1, C3.1, C4.1, C5.1, C6.1, C8.1, J1.2 (VCC), J2.4, J4.1, J5.2, J6.6, Q1.2 (S), R1.2, U1.10 (VDDIO2), U1.18 (VDD), U1.28 (VDD), U2.8 (VCC), U3.2 (~RE), U3.8 (VCC)
BUS_RX: U1.31 (PA1), U2.1 (RO)
BUS_RX_EN: U1.32 (PA2), U2.2 (~RE)
BUS_TX: U1.30 (EXTCLK/PA0), U2.4 (DI)
BUS_TX_EN: U1.1 (PA3), U2.3 (DE)
DBG_RX: J2.2, U1.6 (PC0)
DBG_TX: J2.3, U1.7 (PC1)
Earth: J4.3, J5.6, J6.2, J9.2
GND: C1.2, C2.2, C3.2, C4.2, C5.2, C6.2, C7.2, C8.2, C9.2, C10.2, J1.6 (GND), J2.6, J3.5, J3.6, J3.7, J3.8, J4.2, J5.4, J6.4, R3.1, R6.2, R7.2, U1.19 (GND), U1.29 (GND), U2.5 (GND), U3.3 (DE), U3.5 (GND)
LED_EN: R2.2, U1.8 (PC2)
LED_TX: U1.9 (PC3), U3.4 (DI)
unnamed: C7.1, SW1.1, U1.26 (~RESET/PF6)
unnamed: C9.1, C10.1, J9.1, R7.1
unnamed: J3.1, J3.2, J3.3, J3.4, Q1.3 (D), R4.1
unnamed: J3.9, R4.2, R5.1, U3.6 (A)
unnamed: J5.1, J7.1, J7.2, J7.4
unnamed: J5.3, J7.5, J7.7, J7.8
unnamed: J5.5, J7.SH
unnamed: J6.1, J8.SH
unnamed: J6.3, J8.5, J8.7, J8.8
unnamed: J6.5, J8.1, J8.2, J8.4
unnamed: Q1.1 (G), R1.1, R2.1
unnamed: R3.2, SW1.2
unnamed: J3.10, R5.2, R6.1, U3.7 (B)
UPDI: J1.1 (DATA), U1.27 (UPDI/PF7)

Notes on the sheet:
CTS
PINOUT 1 +5V 2 +5V 3 485 A 4 +5V 5 GND 6 485 B 7 GND 8 GND
OUTPUT
INPUT
DTR

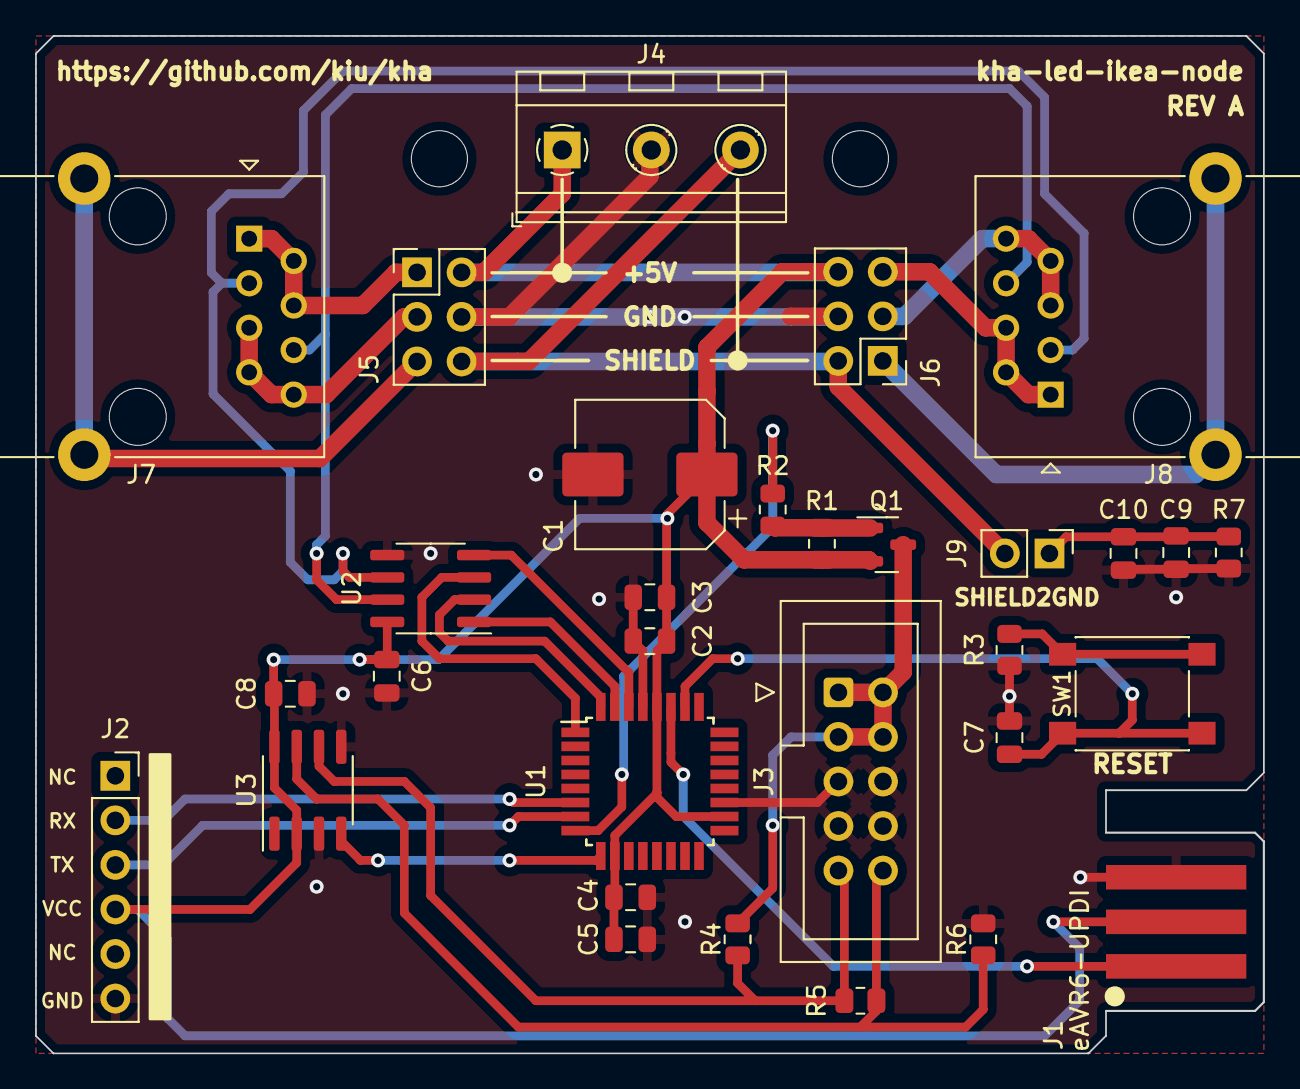
[picture p177: board superseded/kha-nodes/kha-led-ikea-node-reva/kicad/kha-led-ikea-node.k… from above]

Board: 2 copper layers, 70.0 x 58.0 mm, 33 parts (0 on the bottom side), 27 nets.
