kiu/kha/superseded/kha-bgt-rack/kha-bgt-template-64/kicad/kha-bgt-template-64.kicad_pcb

## KiCad design superseded/kha-bgt-rack/kha-bgt-template-64/kicad/kha-bgt-template-64.kicad_pcb (2024-02-16, an earlier design)

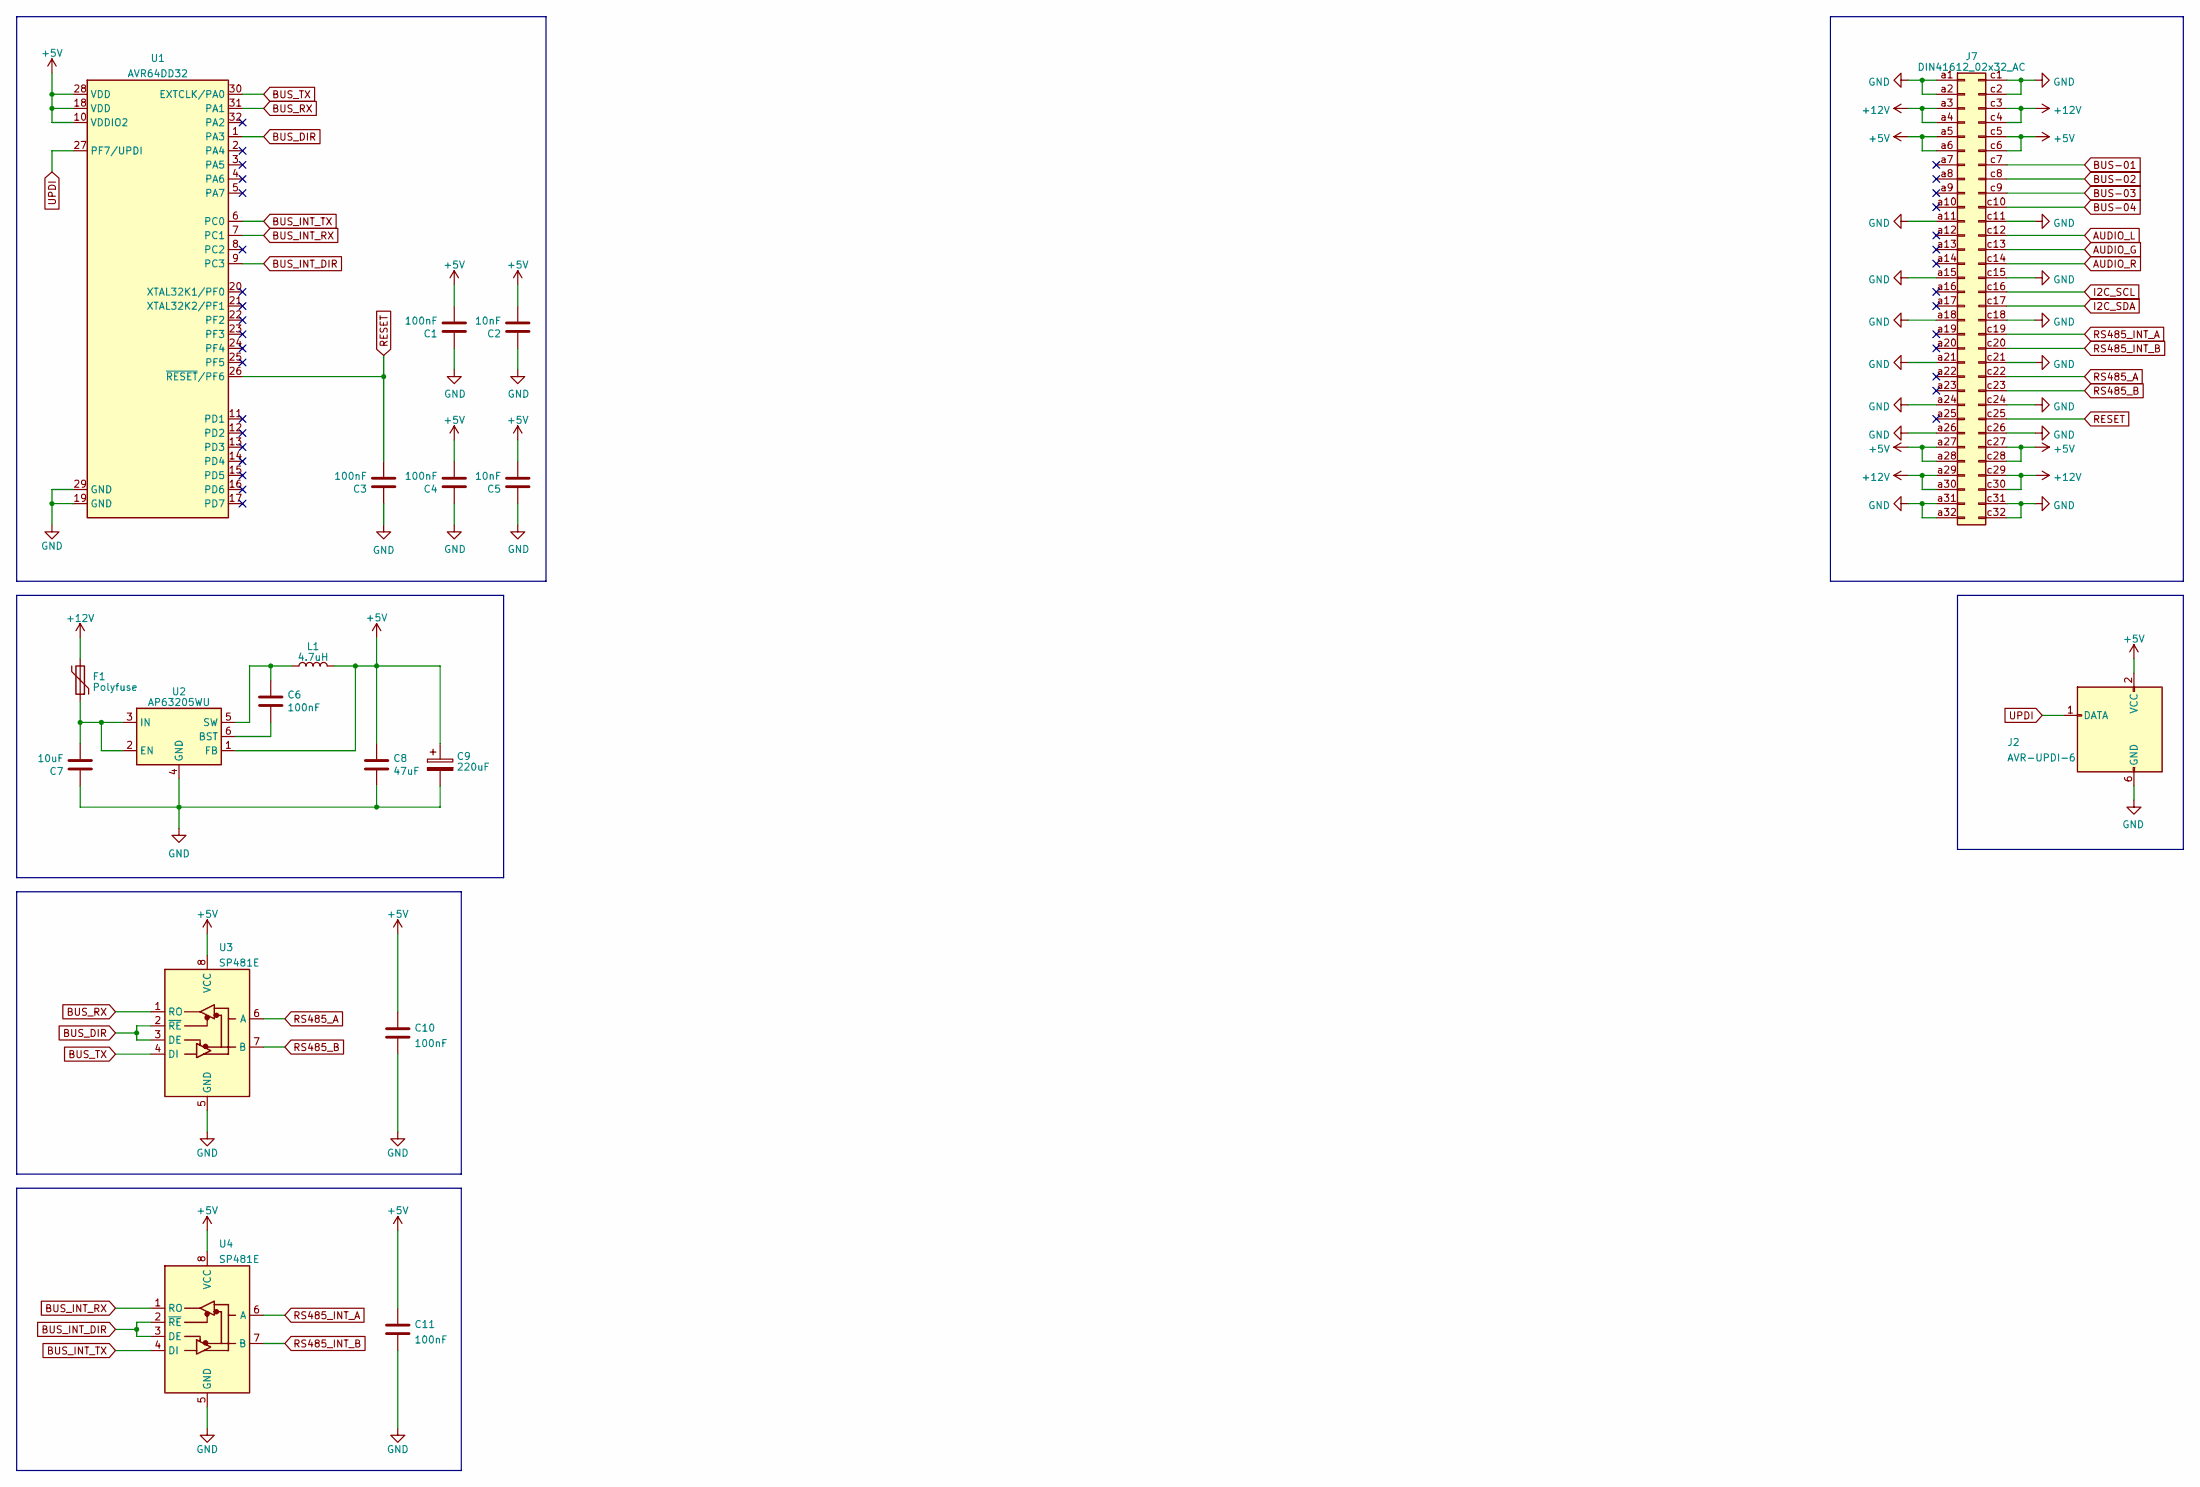
[picture p178: schematic kha-bgt-template-64.kicad_sch]

Parts:
C1, C3, C4, C6, C10, C11: 100nF; C_0805_2012Metric
C2, C5: 10nF; C_0805_2012Metric
C7: 10uF; C_0805_2012Metric
C8: 47uF; C_1210_3225Metric
C9: 220uF; CP_EIA-6032-28_Kemet-C
F1: Polyfuse; Fuse_0805_2012Metric
J2: AVR-UPDI-6; eAVR6-UPDI-B
J7: DIN41612_02x32_AC; DIN41612_C_2x32_Male_Horizontal_THT
L1: 4.7uH; L_1210_3225Metric
U1: AVR64DD32; TQFP-32_7x7mm_P0.8mm
U2: AP63205WU; TSOT-23-6
U3, U4: SP481E; SOIC-8_3.9x4.9mm_P1.27mm

Connections:
+5V: C1.2, C2.2, C4.2, C5.2, C8.1, C9.1, C10.1, C11.1, J2.2 (VCC), J7.a5, J7.a6, J7.a27, J7.a28, J7.c5, J7.c6, J7.c27, J7.c28, L1.2, U1.10 (VDDIO2), U1.18 (VDD), U1.28 (VDD), U2.1 (FB), U3.8 (VCC), U4.8 (VCC)
+12V: F1.2, J7.a3, J7.a4, J7.a29, J7.a30, J7.c3, J7.c4, J7.c29, J7.c30
AUDIO_G: J7.c13
AUDIO_L: J7.c12
AUDIO_R: J7.c14
BUS-01: J7.c7
BUS-02: J7.c8
BUS-03: J7.c9
BUS-04: J7.c10
BUS_DIR: U1.1 (PA3), U3.2 (~RE), U3.3 (DE)
BUS_INT_DIR: U1.9 (PC3), U4.2 (~RE), U4.3 (DE)
BUS_INT_RX: U1.7 (PC1), U4.1 (RO)
BUS_INT_TX: U1.6 (PC0), U4.4 (DI)
BUS_RX: U1.31 (PA1), U3.1 (RO)
BUS_TX: U1.30 (EXTCLK/PA0), U3.4 (DI)
GND: C1.1, C2.1, C3.1, C4.1, C5.1, C7.1, C8.2, C9.2, C10.2, C11.2, J2.6 (GND), J7.a1, J7.a2, J7.a11, J7.a15, J7.a18, J7.a21, J7.a24, J7.a26, J7.a31, J7.a32, J7.c1, J7.c2, J7.c11, J7.c15, J7.c18, J7.c21, J7.c24, J7.c26, J7.c31, J7.c32, U1.19 (GND), U1.29 (GND), U2.4 (GND), U3.5 (GND), U4.5 (GND)
I2C_SCL: J7.c16
I2C_SDA: J7.c17
unnamed: C6.2, U2.6 (BST)
unnamed: C7.2, F1.1, U2.2 (EN), U2.3 (IN)
unnamed: C6.1, L1.1, U2.5 (SW)
RESET: C3.2, J7.c25, U1.26 (~RESET/PF6)
RS485_A: J7.c22, U3.6 (A)
RS485_B: J7.c23, U3.7 (B)
RS485_INT_A: J7.c19, U4.6 (A)
RS485_INT_B: J7.c20, U4.7 (B)
UPDI: J2.1 (DATA), U1.27 (PF7/UPDI)

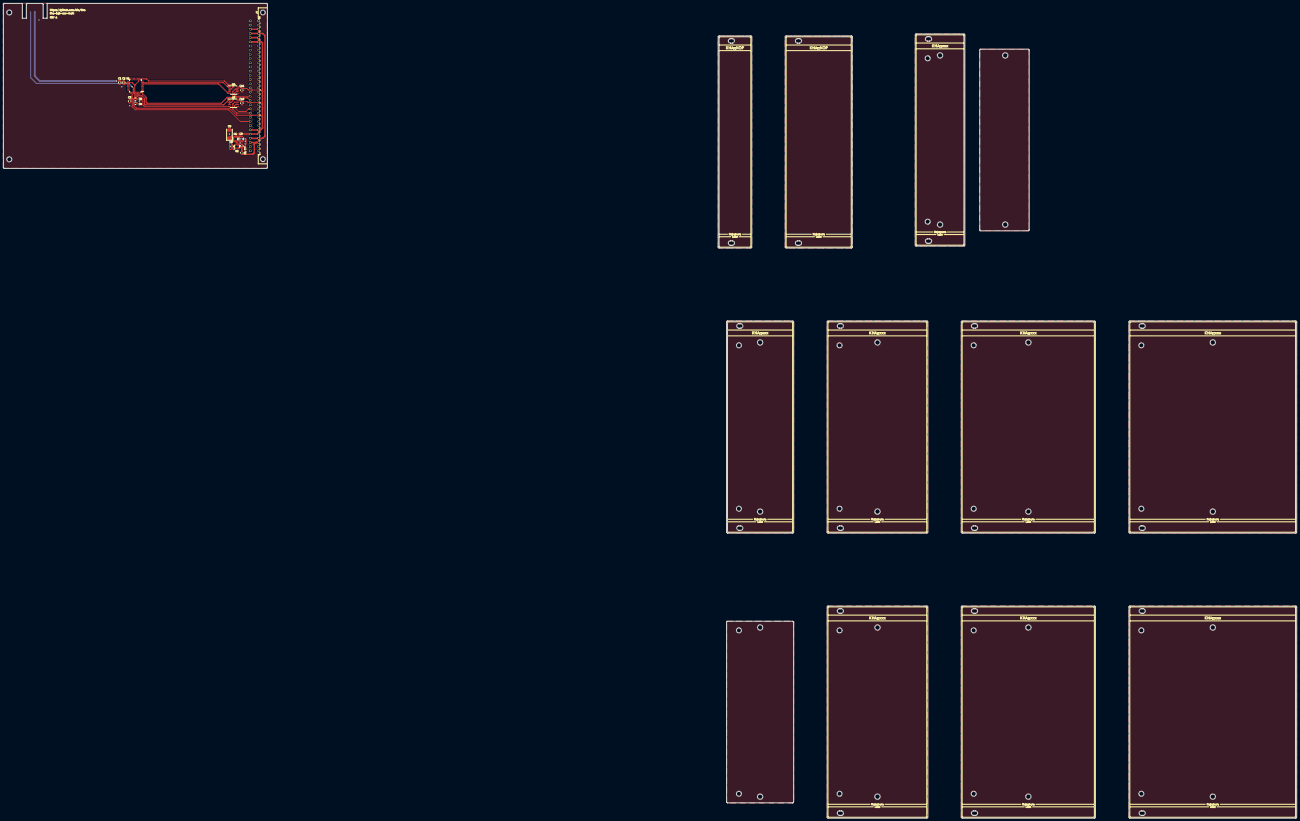
[picture p179: board kha-bgt-template-64.kicad_pcb from above]

Board: 2 copper layers, 160.0 x 100.0 mm, 19 parts (0 on the bottom side), 18 nets.
