kiu/kha/superseded/kha-nodes/kha-led-ikea-rx4-revb1/kicad/kha-led-ikea-rx4.kicad_pcb

## KiCad design superseded/kha-nodes/kha-led-ikea-rx4-revb1/kicad/kha-led-ikea-rx4.kicad_pcb (2024-02-16, an earlier design)

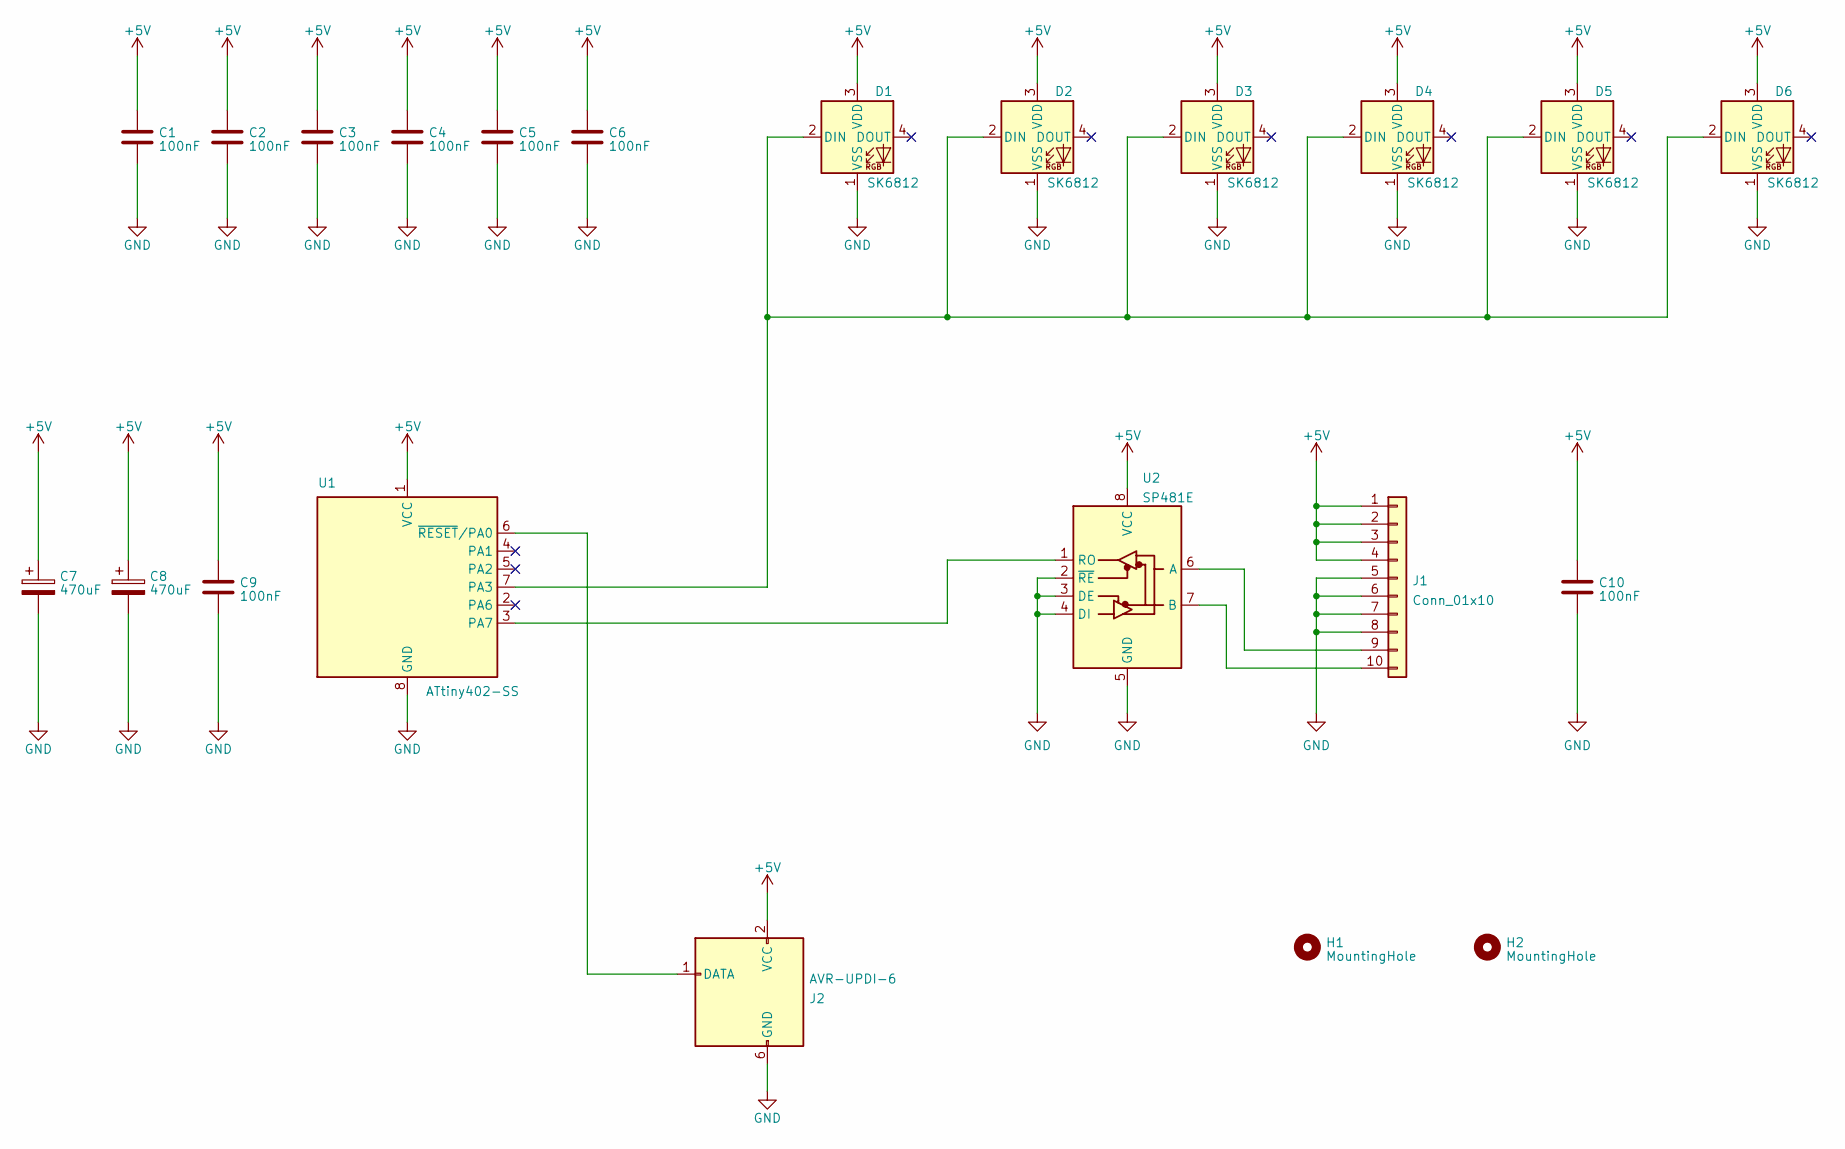
[picture p180: schematic kha-led-ikea-rx4.kicad_sch]

Parts:
C1, C2, C3, C4, C5, C6, C9, C10: 100nF; C_0805_2012Metric
C7, C8: 470uF; CP_EIA-6032-28_Kemet-C
D1, D2, D3, D4, D5, D6: SK6812; LED_SK6812_PLCC4_5.0x5.0mm_P3.2mm
H1, H2: MountingHole; MountingHole_3.2mm_M3_DIN965
J1: Conn_01x10; IDC-Header_2x05_P2.54mm_Vertical
J2: AVR-UPDI-6; eAVR6-UPDI-F
U1: ATtiny402-SS; SOIC-8_3.9x4.9mm_P1.27mm
U2: SP481E; SOIC-8_3.9x4.9mm_P1.27mm

Connections:
+5V: C1.1, C2.1, C3.1, C4.1, C5.1, C6.1, C7.1, C8.1, C9.1, C10.1, D1.3 (VDD), D2.3 (VDD), D3.3 (VDD), D4.3 (VDD), D5.3 (VDD), D6.3 (VDD), J1.1, J1.2, J1.3, J1.4, J2.2 (VCC), U1.1 (VCC), U2.8 (VCC)
GND: C1.2, C2.2, C3.2, C4.2, C5.2, C6.2, C7.2, C8.2, C9.2, C10.2, D1.1 (VSS), D2.1 (VSS), D3.1 (VSS), D4.1 (VSS), D5.1 (VSS), D6.1 (VSS), J1.5, J1.6, J1.7, J1.8, J2.6 (GND), U1.8 (GND), U2.2 (~RE), U2.3 (DE), U2.4 (DI), U2.5 (GND)
unnamed: D1.2 (DIN), D2.2 (DIN), D3.2 (DIN), D4.2 (DIN), D5.2 (DIN), D6.2 (DIN), U1.7 (PA3)
unnamed: J1.9, U2.6 (A)
unnamed: J1.10, U2.7 (B)
unnamed: J2.1 (DATA), U1.6 (~RESET/PA0)
unnamed: U1.3 (PA7), U2.1 (RO)

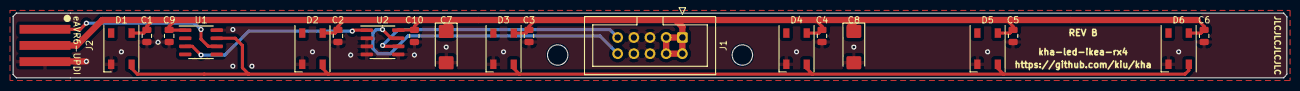
[picture p181: board superseded/kha-nodes/kha-led-ikea-rx4-revb1/kicad/kha-led-ikea-rx4.ki… from above]

Board: 2 copper layers, 200.0 x 10.2 mm, 22 parts (0 on the bottom side), 7 nets.
