kiu/kha/superseded/kha-nodes/kha-led-ikea-node-revb1/kicad/kha-led-ikea-node.kicad_pcb

## KiCad design superseded/kha-nodes/kha-led-ikea-node-revb1/kicad/kha-led-ikea-node.kicad_pcb (2024-02-16, an earlier design)

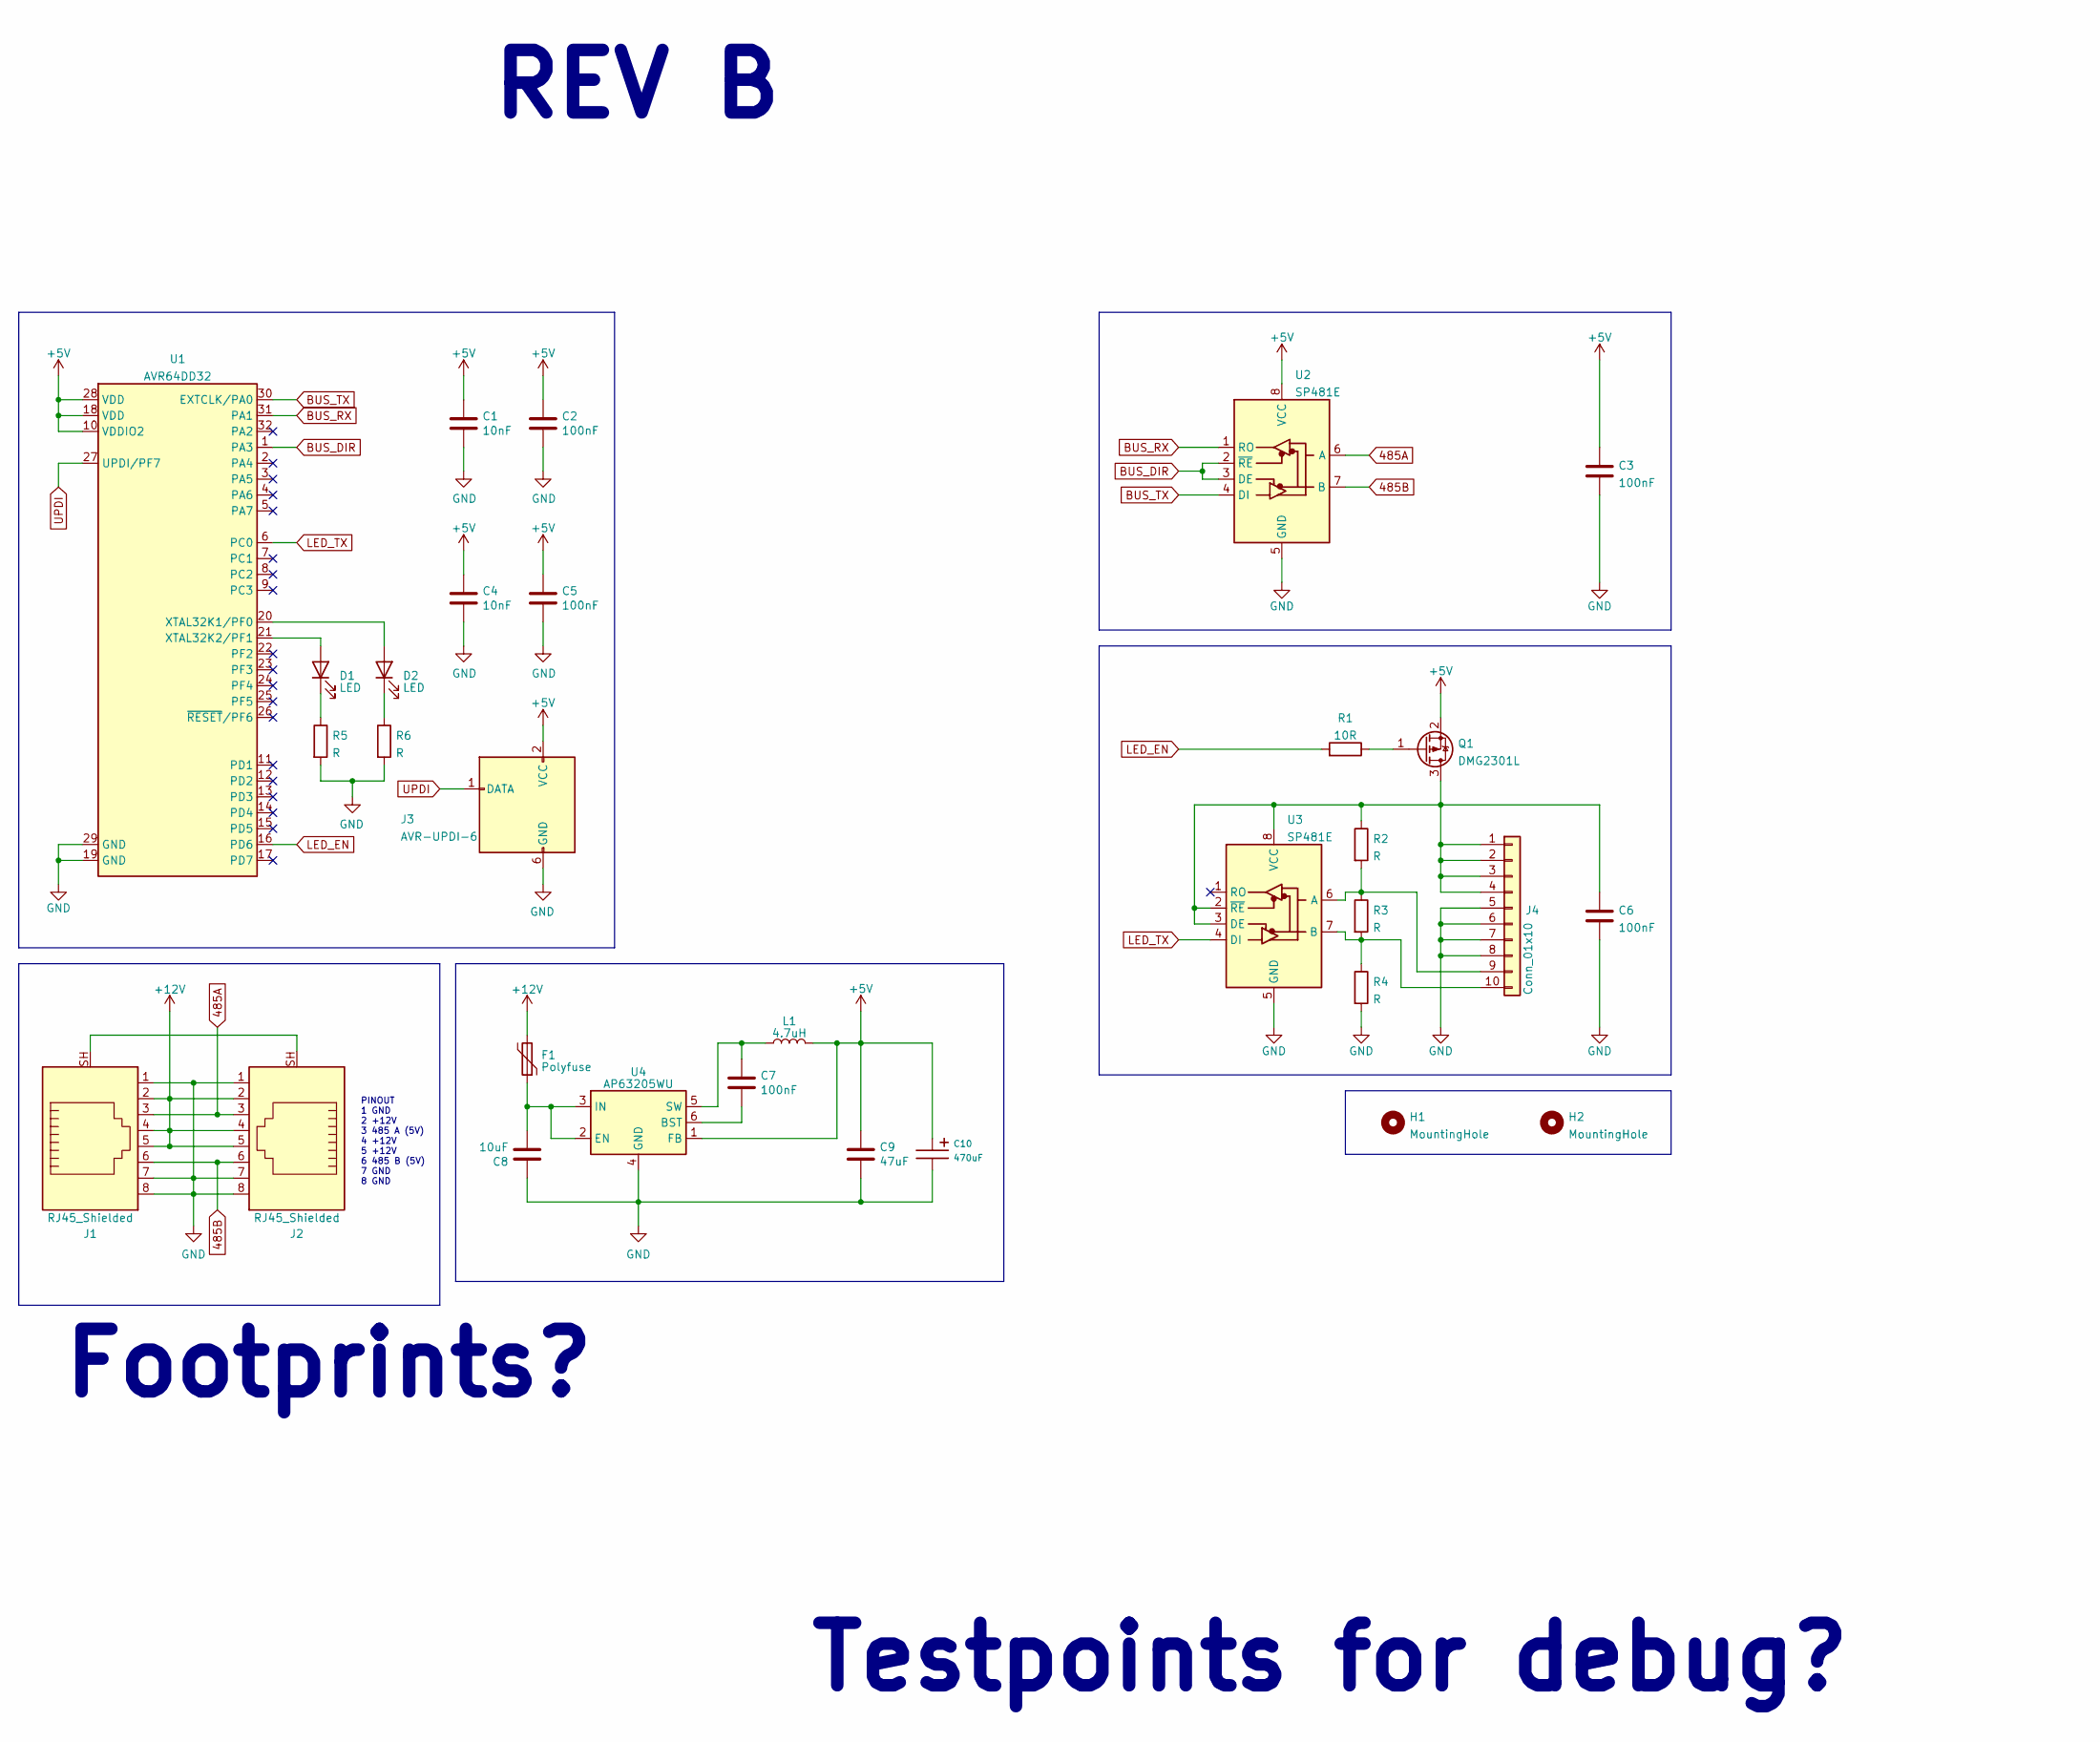
[picture p182: schematic kha-led-ikea-node.kicad_sch]

Parts:
C1: 10nF; L_0805_2012Metric
C2, C3, C5, C6, C7: 100nF; C_0805_2012Metric
C4: 10nF; C_0805_2012Metric
C8: 10uF; C_0805_2012Metric
C9: 47uF; C_1210_3225Metric
C10: 470uF; CP_Elec_8x10
D1, D2: LED; LED_0805_2012Metric
F1: Polyfuse; Fuse_1206_3216Metric
H1, H2: MountingHole; MountingHole_3.2mm_M3_DIN965
J1, J2: RJ45_Shielded; GDLX-S-88K
J3: AVR-UPDI-6; eAVR6-UPDI-F
J4: Conn_01x10; IDC-Header_2x05_P2.54mm_Vertical
L1: 4.7uH; L_6.3x6.3_H3
Q1: DMG2301L; SOT-23
R1: 10R; R_0805_2012Metric
R2, R3, R4, R5, R6: R; R_0805_2012Metric
U1: AVR64DD32; TQFP-32_7x7mm_P0.8mm
U2, U3: SP481E; SOIC-8_3.9x4.9mm_P1.27mm
U4: AP63205WU; TSOT-23-6

Connections:
485A: J1.3, J2.3, U2.6 (A)
485B: J1.6, J2.6, U2.7 (B)
+5V: C1.1, C2.1, C3.1, C4.1, C5.1, C9.1, C10.1, J3.2 (VCC), L1.2, Q1.2 (S), U1.10 (VDDIO2), U1.18 (VDD), U1.28 (VDD), U2.8 (VCC), U4.1 (FB)
+12V: F1.2, J1.2, J1.4, J1.5, J2.2, J2.4, J2.5
BUS_DIR: U1.1 (PA3), U2.2 (~RE), U2.3 (DE)
BUS_RX: U1.31 (PA1), U2.1 (RO)
BUS_TX: U1.30 (EXTCLK/PA0), U2.4 (DI)
GND: C1.2, C2.2, C3.2, C4.2, C5.2, C6.2, C8.1, C9.2, C10.2, J1.1, J1.7, J1.8, J2.1, J2.7, J2.8, J3.6 (GND), J4.5, J4.6, J4.7, J4.8, R4.2, R5.2, R6.2, U1.19 (GND), U1.29 (GND), U2.5 (GND), U3.5 (GND), U4.4 (GND)
LED_EN: R1.2, U1.16 (PD6)
LED_TX: U1.6 (PC0), U3.4 (DI)
unnamed: D1.2 (A), U1.21 (XTAL32K2/PF1)
unnamed: D1.1 (K), R5.1
unnamed: D2.2 (A), U1.20 (XTAL32K1/PF0)
unnamed: D2.1 (K), R6.1
unnamed: J1.SH, J2.SH
unnamed: C6.1, J4.1, J4.2, J4.3, J4.4, Q1.3 (D), R2.1, U3.2 (~RE), U3.3 (DE), U3.8 (VCC)
unnamed: J4.9, R2.2, R3.1, U3.6 (A)
unnamed: J4.10, R3.2, R4.1, U3.7 (B)
unnamed: Q1.1 (G), R1.1
unnamed: C7.2, U4.6 (BST)
unnamed: C8.2, F1.1, U4.2 (EN), U4.3 (IN)
unnamed: C7.1, L1.1, U4.5 (SW)
UPDI: J3.1 (DATA), U1.27 (UPDI/PF7)

Notes on the sheet:
REV B
Testpoints for debug?
PINOUT 1 GND 2 +12V 3 485 A (5V) 4 +12V 5 +12V 6 485 B (5V) 7 GND 8 GND
Footprints?

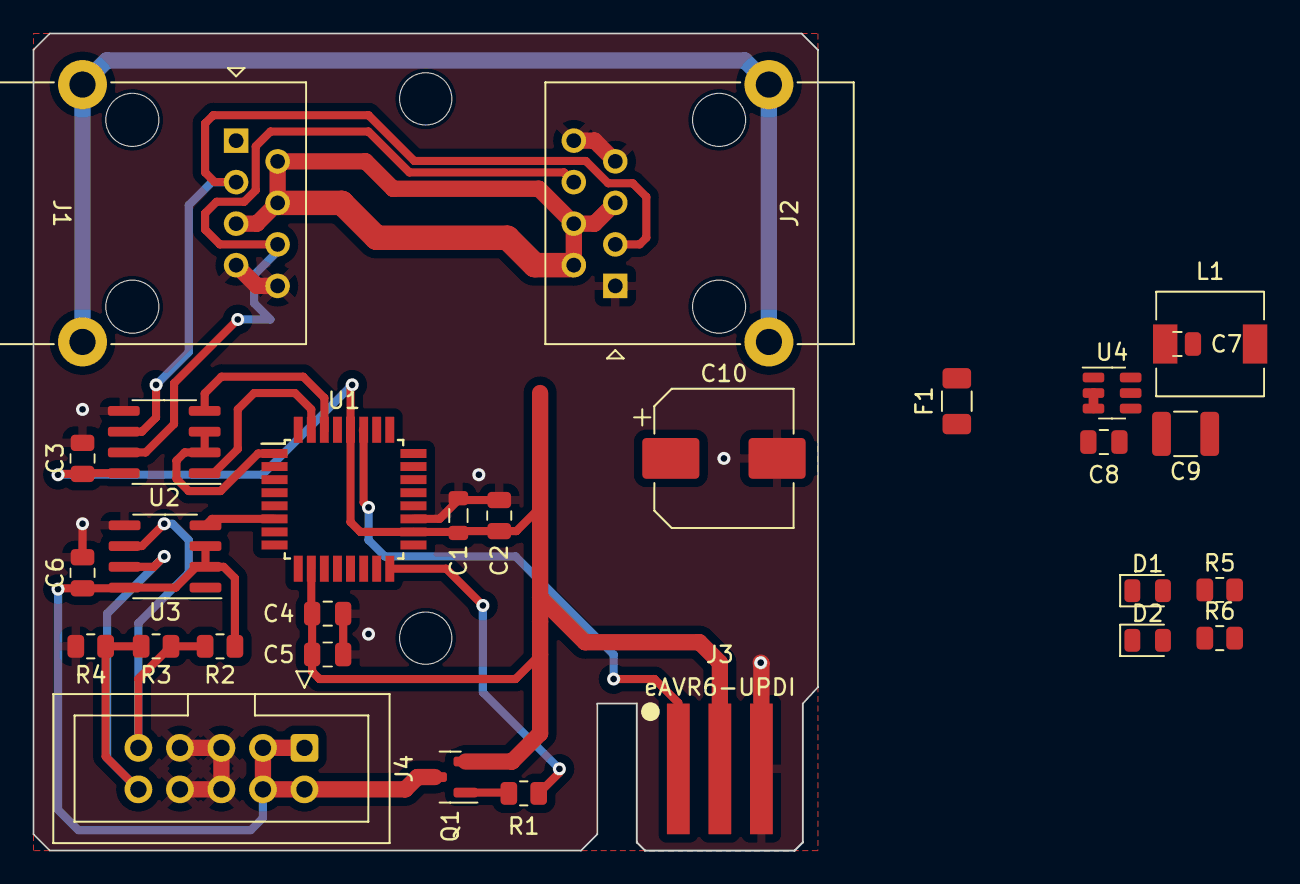
[picture p183: board superseded/kha-nodes/kha-led-ikea-node-revb1/kicad/kha-led-ikea-node.… from above]

Board: 2 copper layers, 48.0 x 50.0 mm, 31 parts (0 on the bottom side), 23 nets.
