kiu/kha/superseded/kha-bgt-subrack/kha-bgt-pwr-reva/kicad/kha-bgt-pwr.kicad_pcb

## KiCad design superseded/kha-bgt-subrack/kha-bgt-pwr-reva/kicad/kha-bgt-pwr.kicad_pcb (2024-02-16, an earlier design)

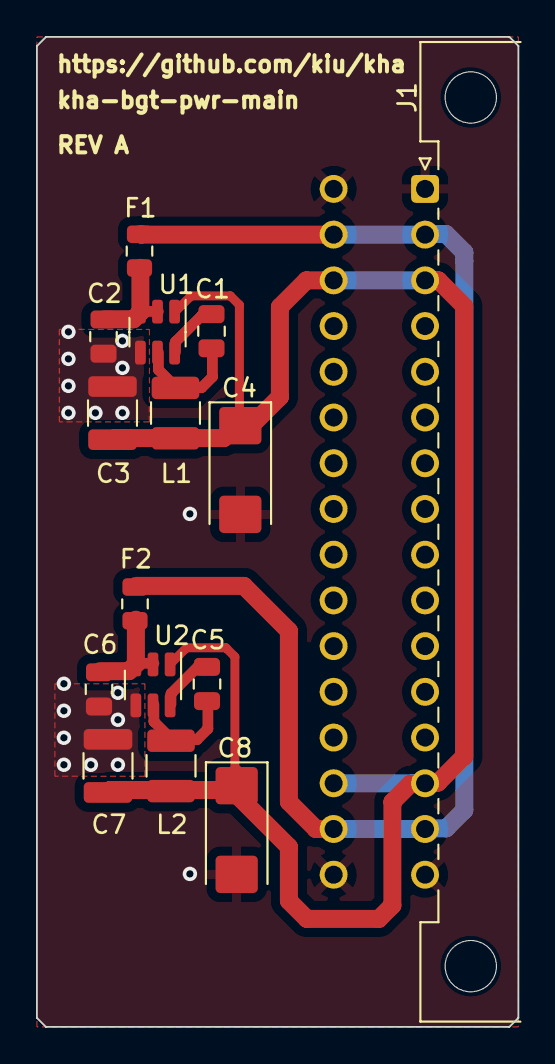
[picture p184: board kha-bgt-pwr.kicad_pcb from above]

Board: 2 copper layers, 26.8 x 55.0 mm, 15 parts (0 on the bottom side), 9 nets.

Parts:
C1, C2, C5, C6: C; C_0805_2012Metric
C3, C7: C; C_1210_3225Metric
C4, C8: C_Polarized; CP_EIA-6032-28_Kemet-C
F1, F2: Polyfuse; Fuse_0805_2012Metric
J1: DIN41612_02x16_AC; DIN41612_C2_2x16_Male_Horizontal_THT
L1, L2: L; L_1210_3225Metric
U1, U2: AP63205WU; TSOT-23-6

Connections:
+5V: C3.1, C4.1, C7.1, C8.1, J1.a3, J1.a14, J1.c3, J1.c14, L1.2, L2.2, U1.1 (FB), U2.1 (FB)
+12V: F1.2, F2.2, J1.a2, J1.a15, J1.c2, J1.c15
GND: C2.1, C3.2, C4.2, C6.1, C7.2, C8.2, J1.a1, J1.a16, J1.c1, J1.c16, U1.4 (GND), U2.4 (GND)
unnamed: C1.2, U1.6 (BST)
unnamed: C2.2, F1.1, U1.2 (EN), U1.3 (IN)
unnamed: C1.1, L1.1, U1.5 (SW)
unnamed: C5.2, U2.6 (BST)
unnamed: C6.2, F2.1, U2.2 (EN), U2.3 (IN)
unnamed: C5.1, L2.1, U2.5 (SW)
