kiu/kha/superseded/kha-bgt-rack/kha-bgt-backplane-mini/kicad/kha-bgt-backplane.kicad_pcb

## KiCad design superseded/kha-bgt-rack/kha-bgt-backplane-mini/kicad/kha-bgt-backplane.kicad_pcb (2024-02-16, an earlier design)

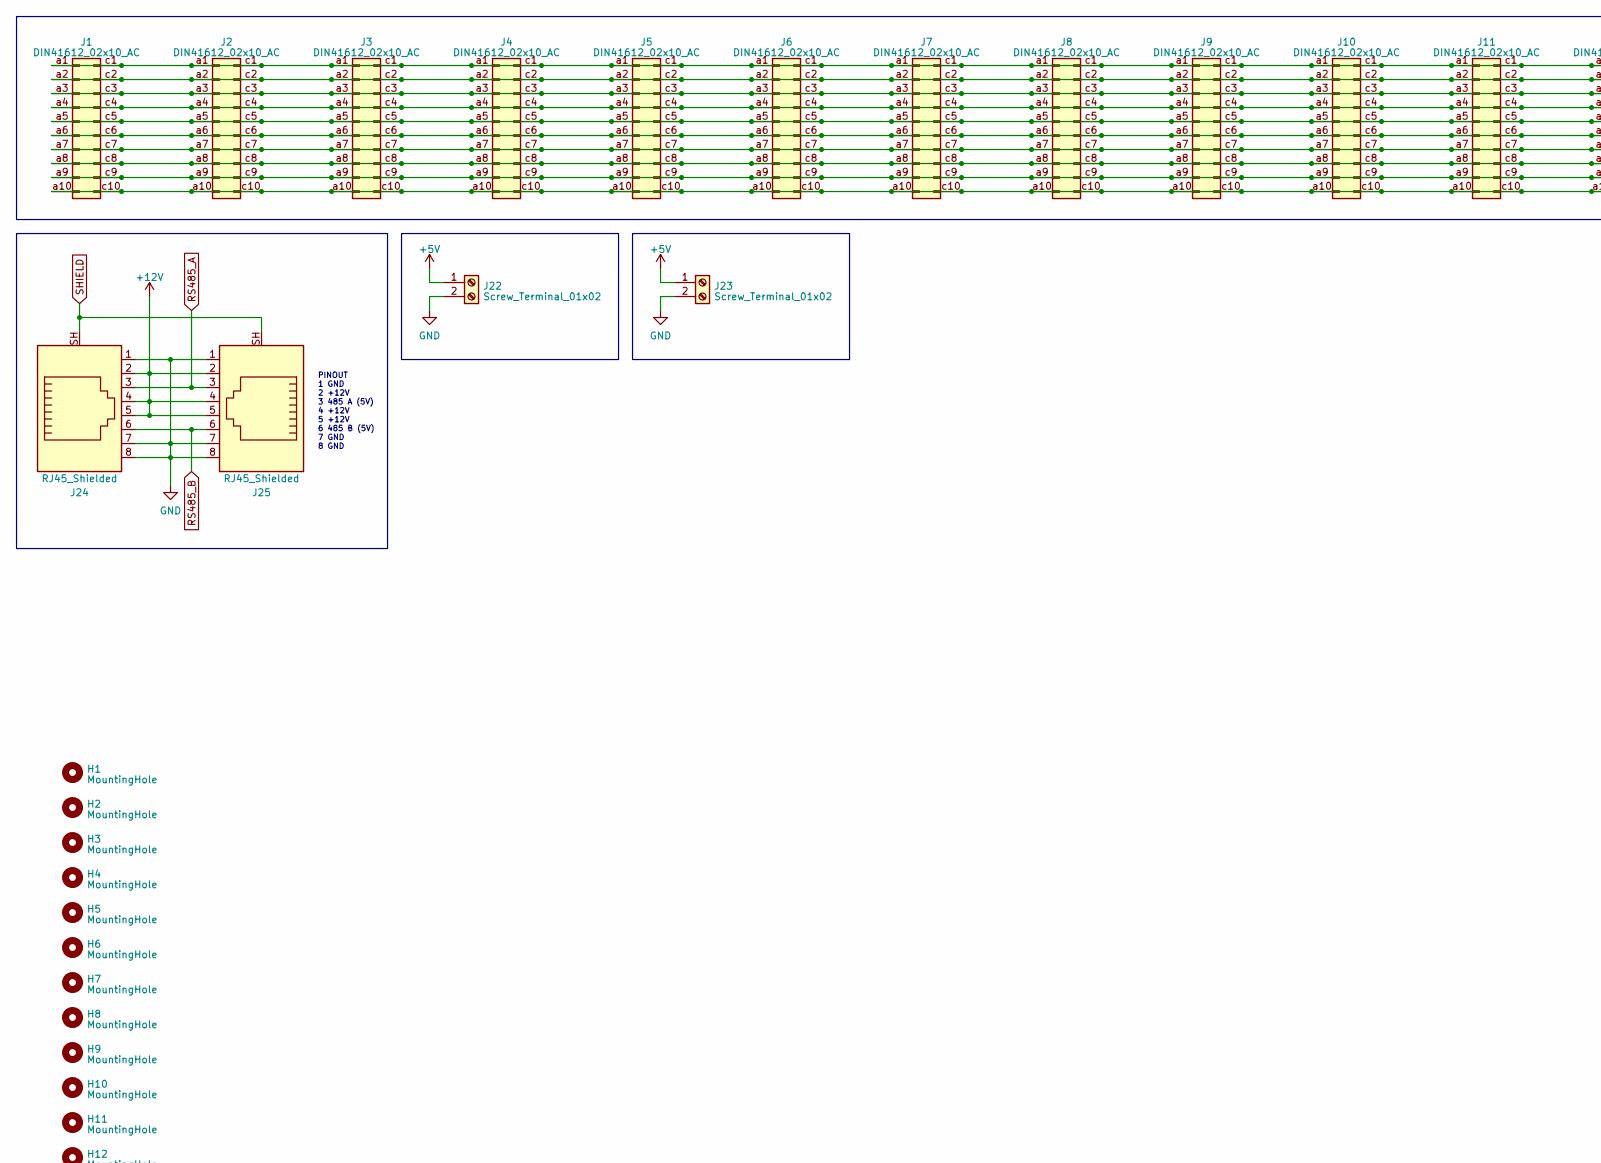
[picture p185: schematic kha-bgt-backplane.kicad_sch, part in row 1, column 1]

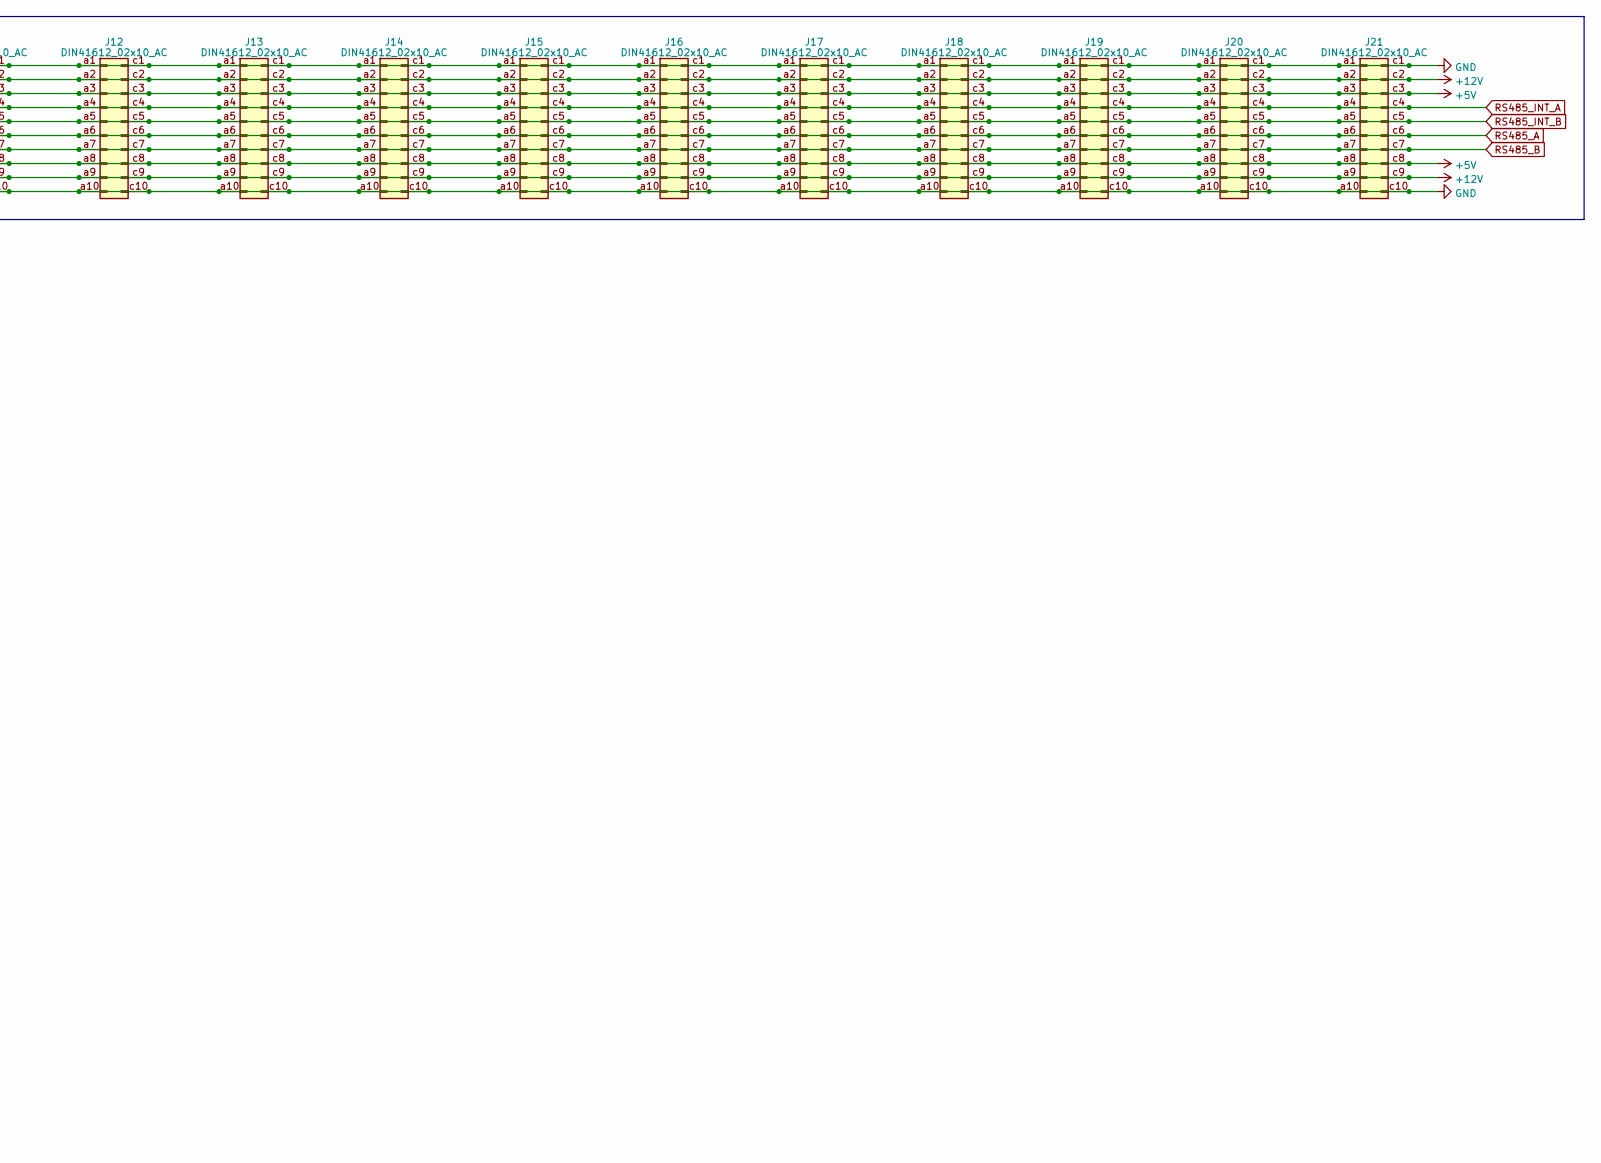
[picture p186: schematic kha-bgt-backplane.kicad_sch, part in row 1, column 2]

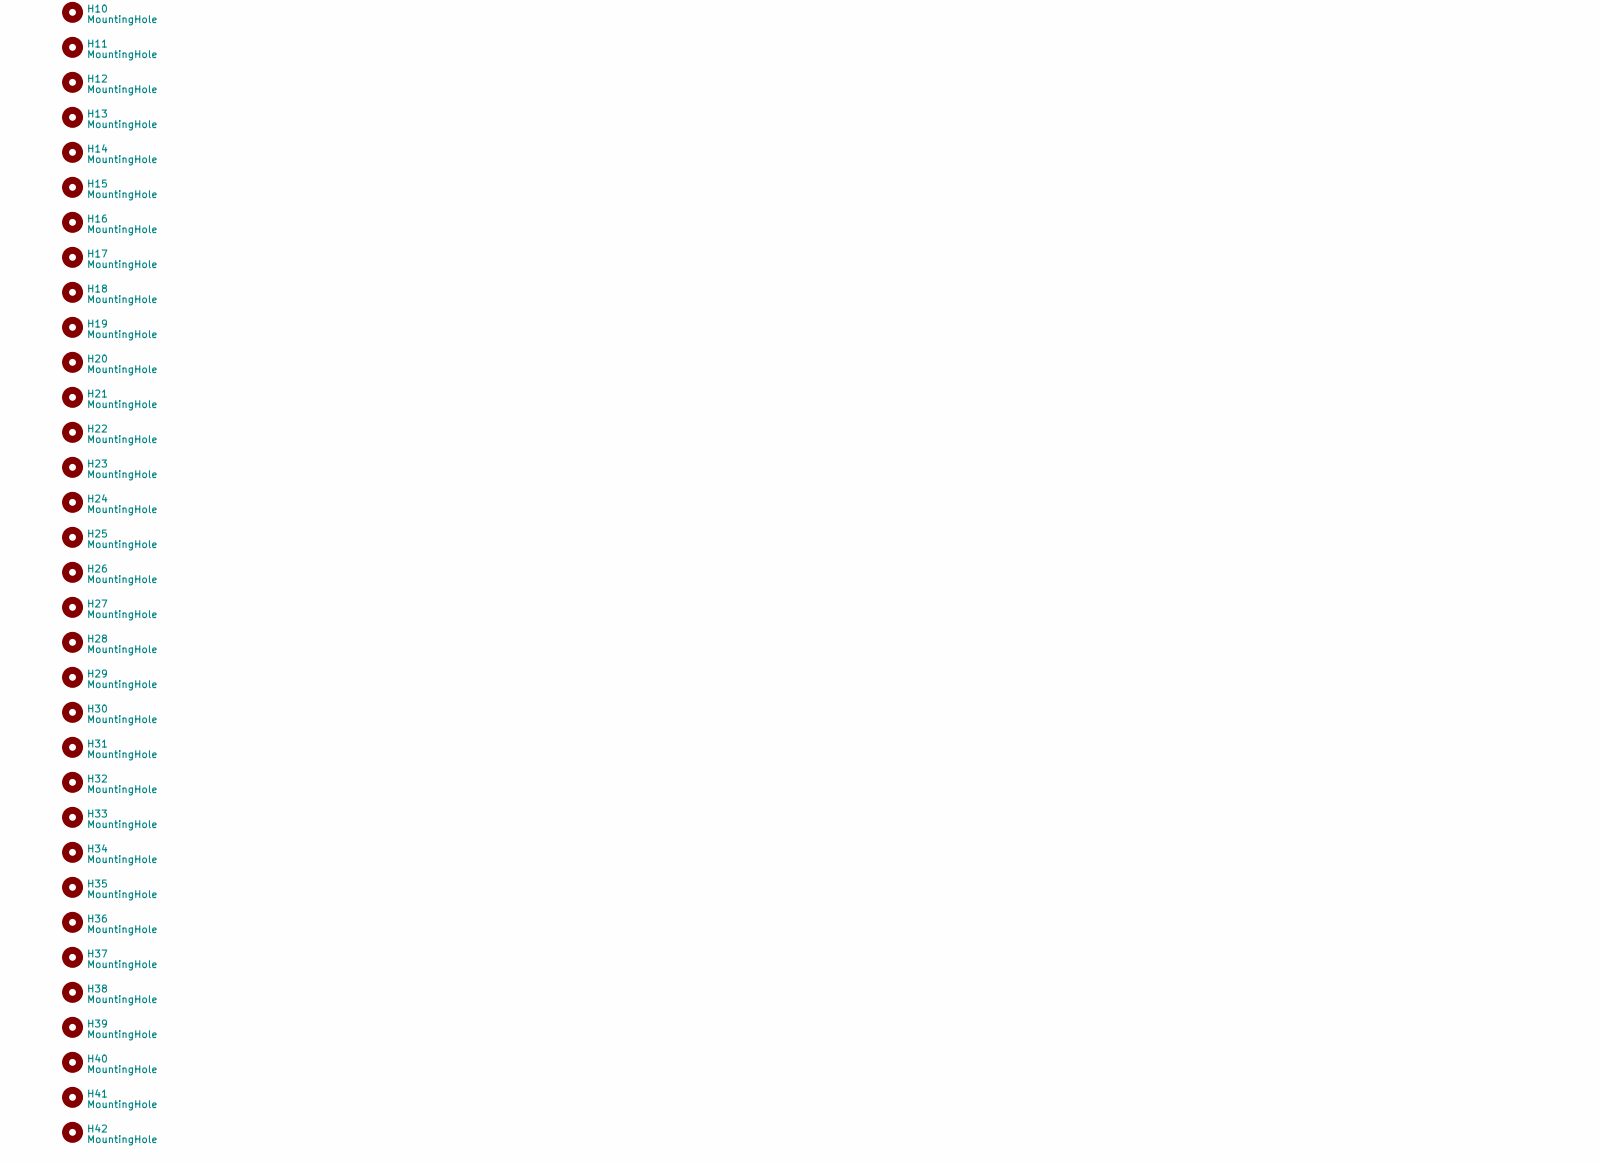
[picture p187: schematic kha-bgt-backplane.kicad_sch, part in row 2, column 1]

Parts:
H1, H2, H3, H4, H5, H6, H7, H8, H9, H10, H11, H12, H13, H14, H15, H16, H17, H18, H19, H20, H21, H22, H23, H24, H25, H26, H27, H28, H29, H30, H31, H32, H33, H34, H35, H36, H37, H38, H39, H40, H41, H42: MountingHole; MountingHole_2.5mm
J1, J2, J3, J4, J5, J6, J7, J8, J9, J10, J11, J12, J13, J14, J15, J16, J17, J18, J19, J20, J21: DIN41612_02x10_AC; DIN41612_C3_2x10_Female_Vertical_THT
J22, J23: Screw_Terminal_01x02; TerminalBlock_RND_205-00232_1x02_P5.08mm_Horizontal
J24, J25: RJ45_Shielded; GDLX-S-88K

Connections:
+5V: J1.a3, J1.a8, J1.c3, J1.c8, J2.a3, J2.a8, J2.c3, J2.c8, J3.a3, J3.a8, J3.c3, J3.c8, J4.a3, J4.a8, J4.c3, J4.c8, J5.a3, J5.a8, J5.c3, J5.c8, J6.a3, J6.a8, J6.c3, J6.c8, J7.a3, J7.a8, J7.c3, J7.c8, J8.a3, J8.a8, J8.c3, J8.c8, J9.a3, J9.a8, J9.c3, J9.c8, J10.a3, J10.a8, J10.c3, J10.c8, J11.a3, J11.a8, J11.c3, J11.c8, J12.a3, J12.a8, J12.c3, J12.c8, J13.a3, J13.a8, J13.c3, J13.c8, J14.a3, J14.a8, J14.c3, J14.c8, J15.a3, J15.a8, J15.c3, J15.c8, J16.a3, J16.a8, J16.c3, J16.c8, J17.a3, J17.a8, J17.c3, J17.c8, J18.a3, J18.a8, J18.c3, J18.c8, J19.a3, J19.a8, J19.c3, J19.c8, J20.a3, J20.a8, J20.c3, J20.c8, J21.a3, J21.a8, J21.c3, J21.c8, J22.1, J23.1
+12V: J1.a2, J1.a9, J1.c2, J1.c9, J2.a2, J2.a9, J2.c2, J2.c9, J3.a2, J3.a9, J3.c2, J3.c9, J4.a2, J4.a9, J4.c2, J4.c9, J5.a2, J5.a9, J5.c2, J5.c9, J6.a2, J6.a9, J6.c2, J6.c9, J7.a2, J7.a9, J7.c2, J7.c9, J8.a2, J8.a9, J8.c2, J8.c9, J9.a2, J9.a9, J9.c2, J9.c9, J10.a2, J10.a9, J10.c2, J10.c9, J11.a2, J11.a9, J11.c2, J11.c9, J12.a2, J12.a9, J12.c2, J12.c9, J13.a2, J13.a9, J13.c2, J13.c9, J14.a2, J14.a9, J14.c2, J14.c9, J15.a2, J15.a9, J15.c2, J15.c9, J16.a2, J16.a9, J16.c2, J16.c9, J17.a2, J17.a9, J17.c2, J17.c9, J18.a2, J18.a9, J18.c2, J18.c9, J19.a2, J19.a9, J19.c2, J19.c9, J20.a2, J20.a9, J20.c2, J20.c9, J21.a2, J21.a9, J21.c2, J21.c9, J24.2, J24.4, J24.5, J25.2, J25.4, J25.5
GND: J1.a1, J1.a10, J1.c1, J1.c10, J2.a1, J2.a10, J2.c1, J2.c10, J3.a1, J3.a10, J3.c1, J3.c10, J4.a1, J4.a10, J4.c1, J4.c10, J5.a1, J5.a10, J5.c1, J5.c10, J6.a1, J6.a10, J6.c1, J6.c10, J7.a1, J7.a10, J7.c1, J7.c10, J8.a1, J8.a10, J8.c1, J8.c10, J9.a1, J9.a10, J9.c1, J9.c10, J10.a1, J10.a10, J10.c1, J10.c10, J11.a1, J11.a10, J11.c1, J11.c10, J12.a1, J12.a10, J12.c1, J12.c10, J13.a1, J13.a10, J13.c1, J13.c10, J14.a1, J14.a10, J14.c1, J14.c10, J15.a1, J15.a10, J15.c1, J15.c10, J16.a1, J16.a10, J16.c1, J16.c10, J17.a1, J17.a10, J17.c1, J17.c10, J18.a1, J18.a10, J18.c1, J18.c10, J19.a1, J19.a10, J19.c1, J19.c10, J20.a1, J20.a10, J20.c1, J20.c10, J21.a1, J21.a10, J21.c1, J21.c10, J22.2, J23.2, J24.1, J24.7, J24.8, J25.1, J25.7, J25.8
RS485_A: J1.a6, J1.c6, J2.a6, J2.c6, J3.a6, J3.c6, J4.a6, J4.c6, J5.a6, J5.c6, J6.a6, J6.c6, J7.a6, J7.c6, J8.a6, J8.c6, J9.a6, J9.c6, J10.a6, J10.c6, J11.a6, J11.c6, J12.a6, J12.c6, J13.a6, J13.c6, J14.a6, J14.c6, J15.a6, J15.c6, J16.a6, J16.c6, J17.a6, J17.c6, J18.a6, J18.c6, J19.a6, J19.c6, J20.a6, J20.c6, J21.a6, J21.c6, J24.3, J25.3
RS485_B: J1.a7, J1.c7, J2.a7, J2.c7, J3.a7, J3.c7, J4.a7, J4.c7, J5.a7, J5.c7, J6.a7, J6.c7, J7.a7, J7.c7, J8.a7, J8.c7, J9.a7, J9.c7, J10.a7, J10.c7, J11.a7, J11.c7, J12.a7, J12.c7, J13.a7, J13.c7, J14.a7, J14.c7, J15.a7, J15.c7, J16.a7, J16.c7, J17.a7, J17.c7, J18.a7, J18.c7, J19.a7, J19.c7, J20.a7, J20.c7, J21.a7, J21.c7, J24.6, J25.6
RS485_INT_A: J1.a4, J1.c4, J2.a4, J2.c4, J3.a4, J3.c4, J4.a4, J4.c4, J5.a4, J5.c4, J6.a4, J6.c4, J7.a4, J7.c4, J8.a4, J8.c4, J9.a4, J9.c4, J10.a4, J10.c4, J11.a4, J11.c4, J12.a4, J12.c4, J13.a4, J13.c4, J14.a4, J14.c4, J15.a4, J15.c4, J16.a4, J16.c4, J17.a4, J17.c4, J18.a4, J18.c4, J19.a4, J19.c4, J20.a4, J20.c4, J21.a4, J21.c4
RS485_INT_B: J1.a5, J1.c5, J2.a5, J2.c5, J3.a5, J3.c5, J4.a5, J4.c5, J5.a5, J5.c5, J6.a5, J6.c5, J7.a5, J7.c5, J8.a5, J8.c5, J9.a5, J9.c5, J10.a5, J10.c5, J11.a5, J11.c5, J12.a5, J12.c5, J13.a5, J13.c5, J14.a5, J14.c5, J15.a5, J15.c5, J16.a5, J16.c5, J17.a5, J17.c5, J18.a5, J18.c5, J19.a5, J19.c5, J20.a5, J20.c5, J21.a5, J21.c5
SHIELD: J24.SH, J25.SH

Notes on the sheet:
PINOUT 1 GND 2 +12V 3 485 A (5V) 4 +12V 5 +12V 6 485 B (5V) 7 GND 8 GND

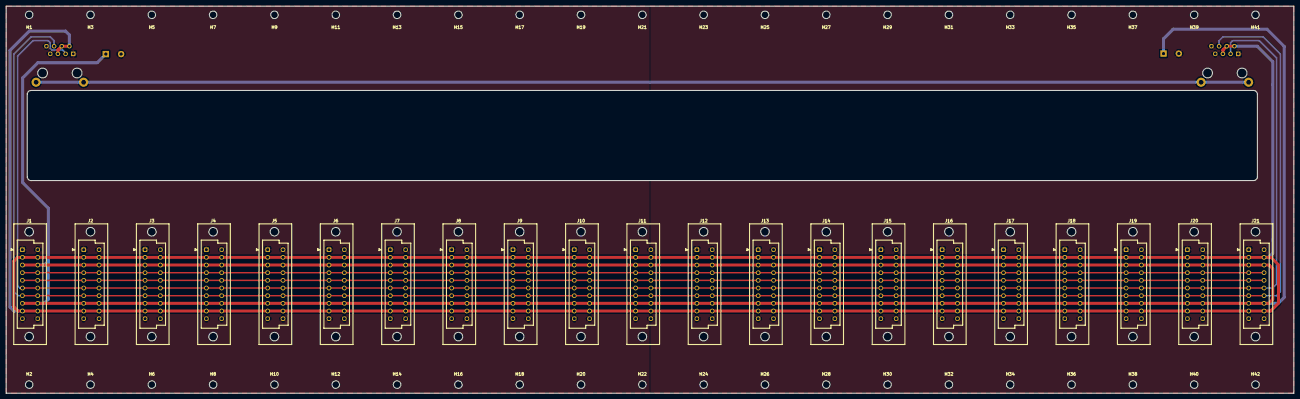
[picture p188: board kha-bgt-backplane.kicad_pcb from above]

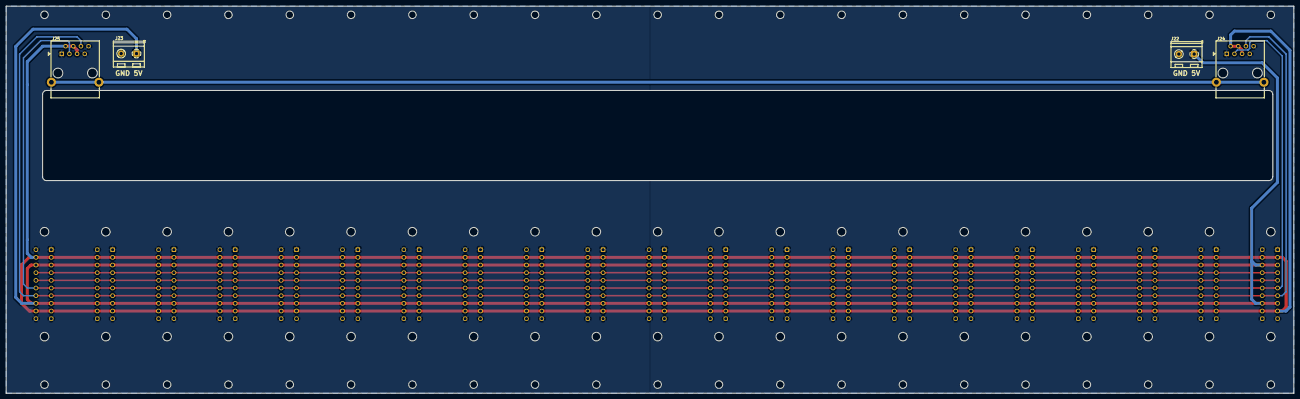
[picture p189: board kha-bgt-backplane.kicad_pcb from below]

Board: 2 copper layers, 426.7 x 128.3 mm, 67 parts (4 on the bottom side), 8 nets.
