kiu/kha/superseded/kha-nodes/kha-led-ikea-rx4-reva/kicad/kha-led-ikea-rx4.kicad_pcb

## KiCad design superseded/kha-nodes/kha-led-ikea-rx4-reva/kicad/kha-led-ikea-rx4.kicad_pcb (2024-02-16, an earlier design)

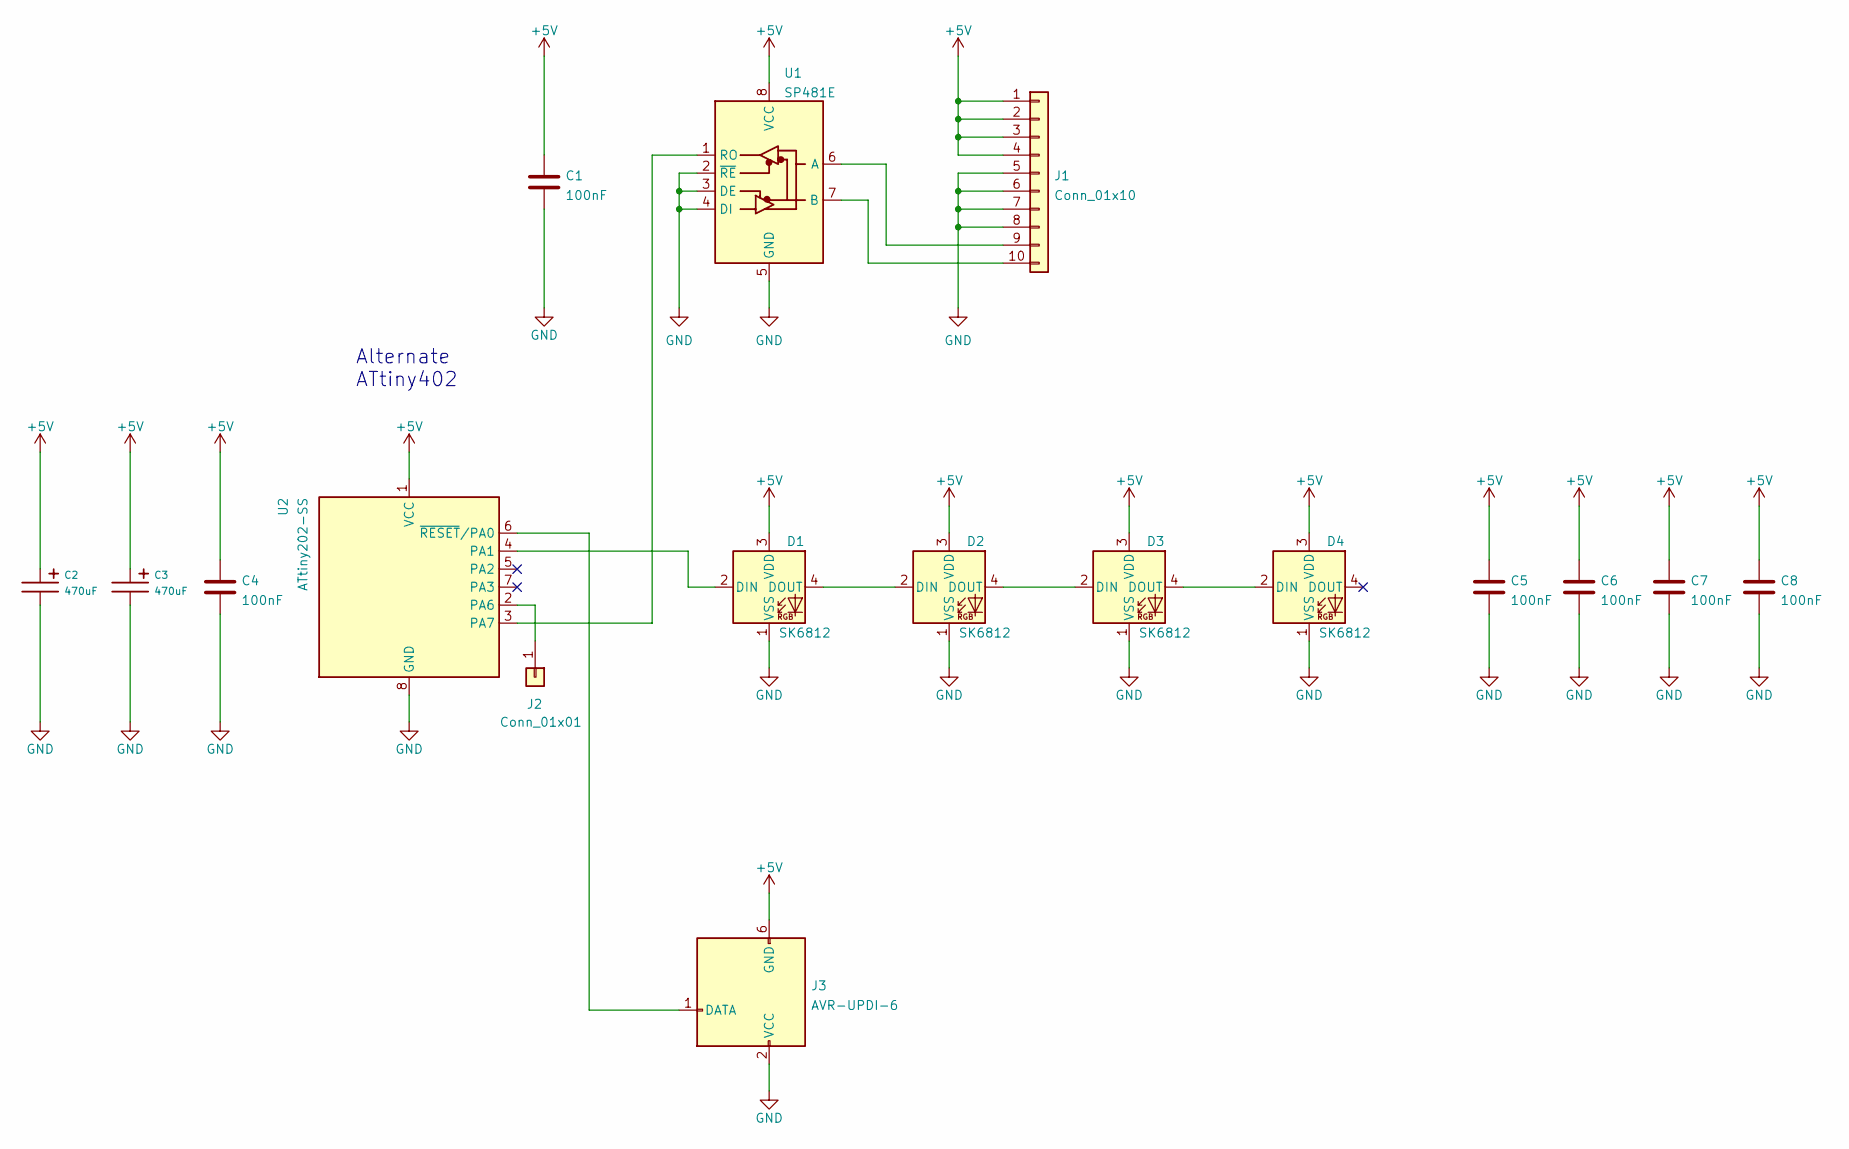
[picture p190: schematic kha-led-ikea-rx4.kicad_sch]

Parts:
C1, C4, C5, C6, C7, C8: 100nF; C_0805_2012Metric
C2, C3: 470uF; CP_EIA-6032-28_Kemet-C
D1, D2, D3, D4: SK6812; LED_SK6812_PLCC4_5.0x5.0mm_P3.2mm
J1: Conn_01x10; IDC-Header_2x05_P2.54mm_Vertical
J2: Conn_01x01; TestPoint_Pad_1.5x1.5mm
J3: AVR-UPDI-6; eAVR6-UPDI-F
U1: SP481E; SOIC-8_3.9x4.9mm_P1.27mm
U2: ATtiny202-SS; SOIC-8_3.9x4.9mm_P1.27mm

Connections:
+5V: C1.1, C2.1, C3.1, C4.1, C5.1, C6.1, C7.1, C8.1, D1.3 (VDD), D2.3 (VDD), D3.3 (VDD), D4.3 (VDD), J1.1, J1.2, J1.3, J1.4, J3.6 (GND), U1.8 (VCC), U2.1 (VCC)
GND: C1.2, C2.2, C3.2, C4.2, C5.2, C6.2, C7.2, C8.2, D1.1 (VSS), D2.1 (VSS), D3.1 (VSS), D4.1 (VSS), J1.5, J1.6, J1.7, J1.8, J3.2 (VCC), U1.2 (~RE), U1.3 (DE), U1.4 (DI), U1.5 (GND), U2.8 (GND)
unnamed: D1.2 (DIN), U2.4 (PA1)
unnamed: D1.4 (DOUT), D2.2 (DIN)
unnamed: D2.4 (DOUT), D3.2 (DIN)
unnamed: D3.4 (DOUT), D4.2 (DIN)
unnamed: J1.9, U1.6 (A)
unnamed: J1.10, U1.7 (B)
unnamed: J2.1, U2.2 (PA6)
unnamed: J3.1 (DATA), U2.6 (~RESET/PA0)
unnamed: U1.1 (RO), U2.3 (PA7)

Notes on the sheet:
Alternate ATtiny402

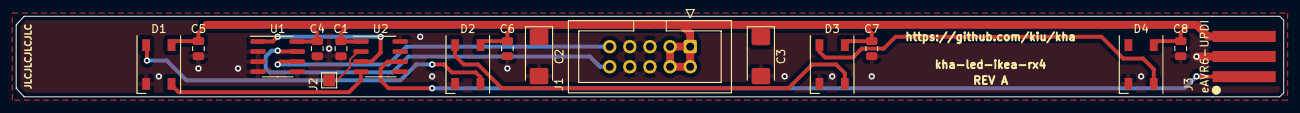
[picture p191: board superseded/kha-nodes/kha-led-ikea-rx4-reva/kicad/kha-led-ikea-rx4.kic… from above]

Board: 2 copper layers, 160.0 x 10.2 mm, 17 parts (0 on the bottom side), 11 nets.
