kiu/kha/kha-bgt-misc/kha-bgt-extend/kicad/kha-bgt-extend.kicad_sch

## KiCad design kha-bgt-misc/kha-bgt-extend/kicad/kha-bgt-extend.kicad_sch (2024-02-16)

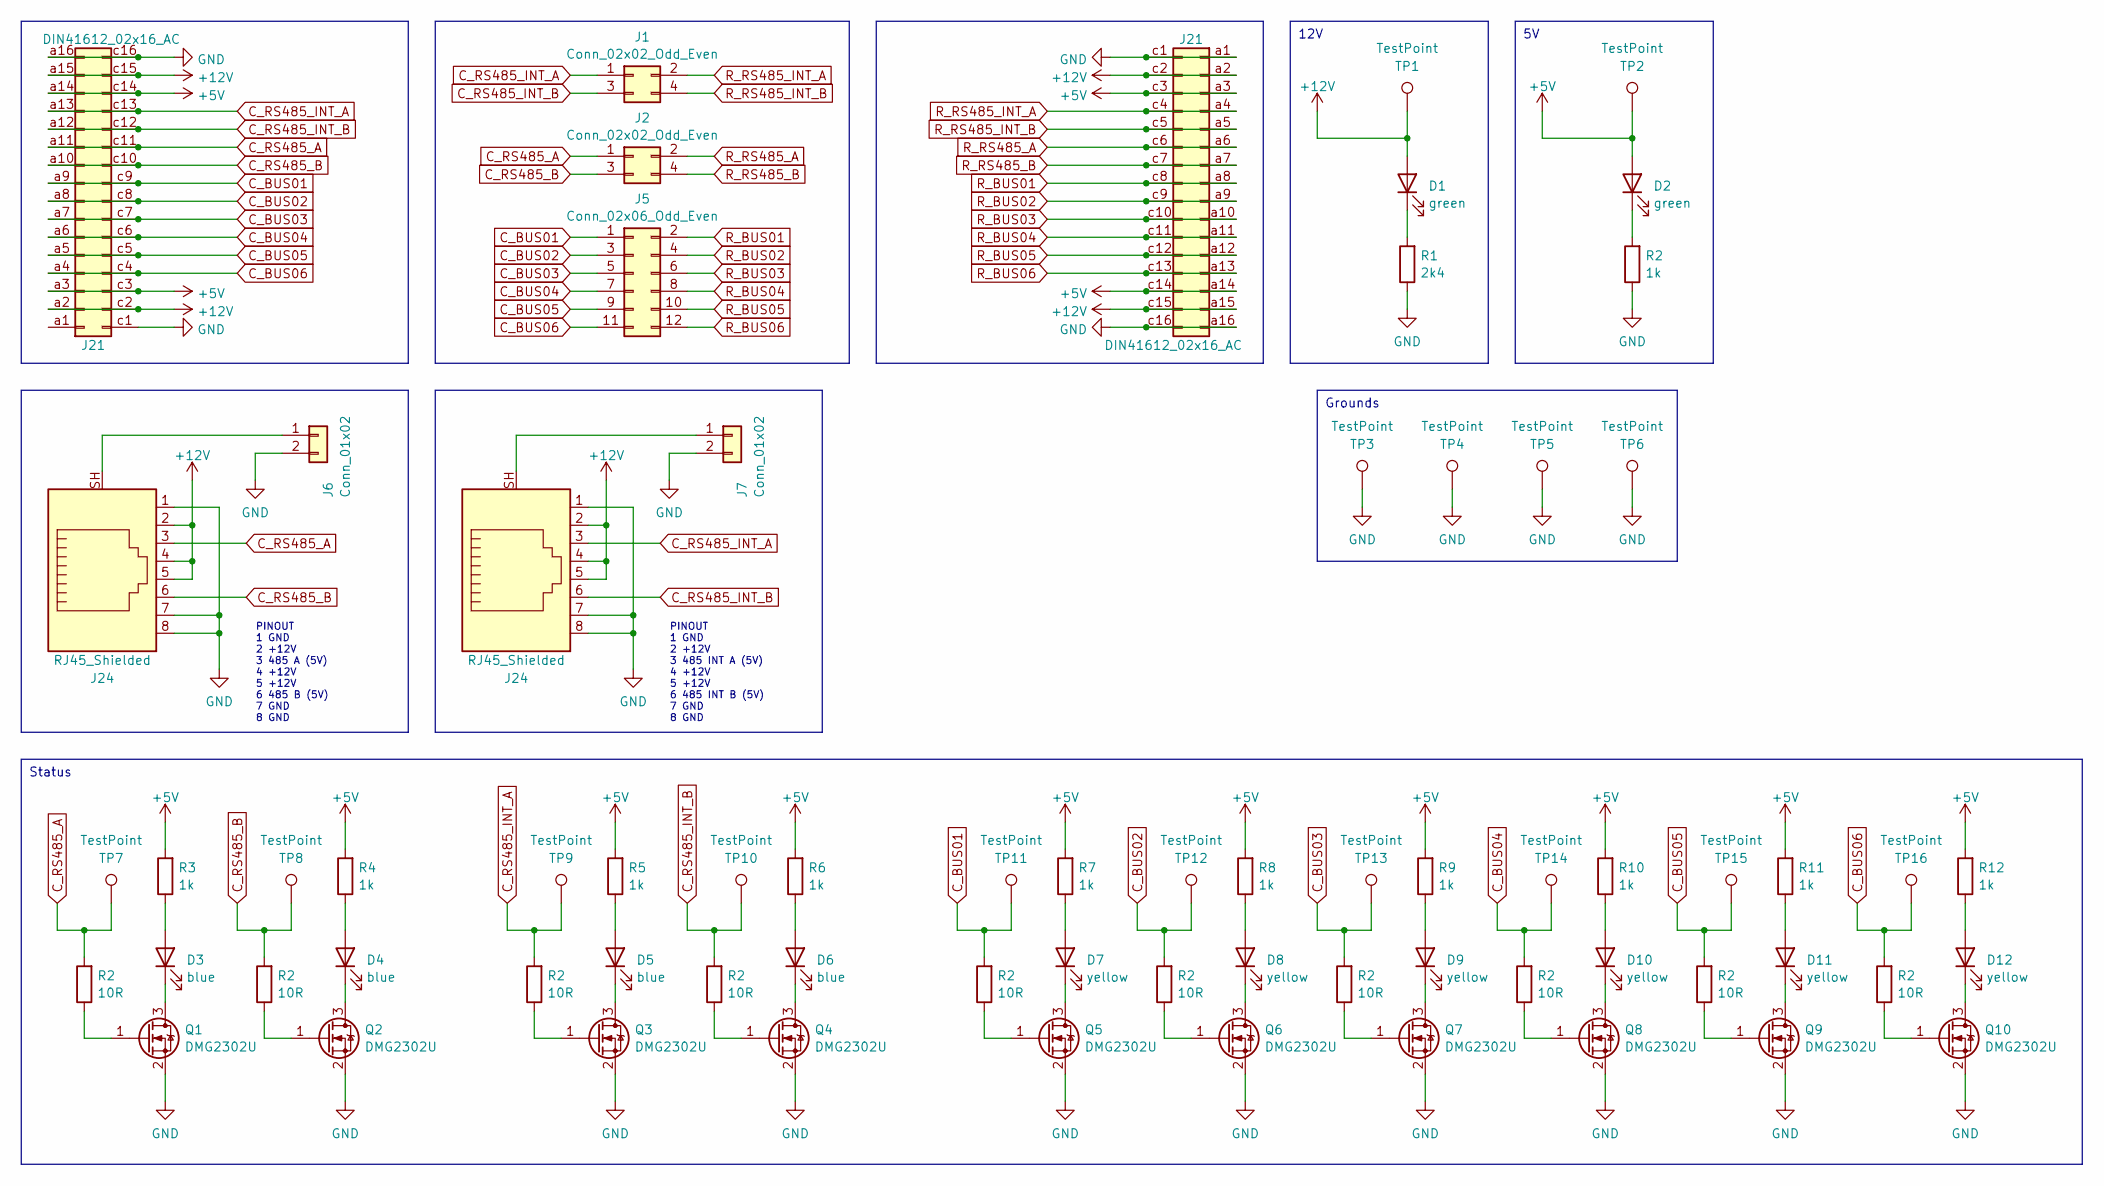
[picture p192: schematic kha-bgt-extend.kicad_sch]

Parts:
D1, D2: green; LED_0805_2012Metric
D3, D4, D5, D6: blue; LED_0805_2012Metric
D7, D8, D9, D10, D11, D12: yellow; LED_0805_2012Metric
J1, J2: Conn_02x02_Odd_Even; PinHeader_2x02_P2.54mm_Vertical
J5: Conn_02x06_Odd_Even; PinHeader_2x06_P2.54mm_Vertical
J6, J7: Conn_01x02; PinHeader_1x02_P2.54mm_Vertical
J21: DIN41612_02x16_AC; DIN41612_C2_2x16_Male_Horizontal_THT
J24: RJ45_Shielded; GDLX-S-88K
Q1, Q2, Q3, Q4, Q5, Q6, Q7, Q8, Q9, Q10: DMG2302U; SOT-23
R1: 2k4; R_0805_2012Metric
R2: 10R; R_0805_2012Metric
R3, R4, R5, R6, R7, R8, R9, R10, R11, R12: 1k; R_0805_2012Metric
TP1, TP2, TP3, TP4, TP5, TP6, TP7, TP8, TP9, TP10, TP11, TP12, TP13, TP14, TP15, TP16: TestPoint; TestPoint_Keystone_5010-5014_Multipurpose

Connections:
+5V: D2.2 (A), J21.a3, J21.a14, J21.c3, J21.c14, R3.2, R4.2, R5.2, R6.2, R7.2, R8.2, R9.2, R10.2, R11.2, R12.2, TP2.1
+12V: D1.2 (A), J21.a2, J21.a15, J21.c2, J21.c15, J24.2, J24.4, J24.5, TP1.1
C_BUS01: J5.1, J21.a9, J21.c9, R2.2, TP11.1
C_BUS02: J5.3, J21.a8, J21.c8, R2.2, TP12.1
C_BUS03: J5.5, J21.a7, J21.c7, R2.2, TP13.1
C_BUS04: J5.7, J21.a6, J21.c6, R2.2, TP14.1
C_BUS05: J5.9, J21.a5, J21.c5, R2.2, TP15.1
C_BUS06: J5.11, J21.a4, J21.c4, R2.2, TP16.1
C_RS485_A: J2.1, J21.a11, J21.c11, J24.3, R2.2, TP7.1
C_RS485_B: J2.3, J21.a10, J21.c10, J24.6, R2.2, TP8.1
C_RS485_INT_A: J1.1, J21.a13, J21.c13, J24.3, R2.2, TP9.1
C_RS485_INT_B: J1.3, J21.a12, J21.c12, J24.6, R2.2, TP10.1
GND: J6.2, J7.2, J21.a1, J21.a16, J21.c1, J21.c16, J24.1, J24.7, J24.8, Q1.2 (S), Q2.2 (S), Q3.2 (S), Q4.2 (S), Q5.2 (S), Q6.2 (S), Q7.2 (S), Q8.2 (S), Q9.2 (S), Q10.2 (S), R1.1, R2.1, TP3.1, TP4.1, TP5.1, TP6.1
unnamed: D1.1 (K), R1.2
unnamed: D2.1 (K), R2.2
unnamed: D3.1 (K), Q1.3 (D)
unnamed: D3.2 (A), R3.1
unnamed: D4.1 (K), Q2.3 (D)
unnamed: D4.2 (A), R4.1
unnamed: D5.1 (K), Q3.3 (D)
unnamed: D5.2 (A), R5.1
unnamed: D6.1 (K), Q4.3 (D)
unnamed: D6.2 (A), R6.1
unnamed: D7.1 (K), Q5.3 (D)
unnamed: D7.2 (A), R7.1
unnamed: D8.1 (K), Q6.3 (D)
unnamed: D8.2 (A), R8.1
unnamed: D9.1 (K), Q7.3 (D)
unnamed: D9.2 (A), R9.1
unnamed: D10.1 (K), Q8.3 (D)
unnamed: D10.2 (A), R10.1
unnamed: D11.1 (K), Q9.3 (D)
unnamed: D11.2 (A), R11.1
unnamed: D12.1 (K), Q10.3 (D)
unnamed: D12.2 (A), R12.1
unnamed: J6.1, J7.1, J24.SH
unnamed: Q1.1 (G), R2.1
unnamed: Q2.1 (G), R2.1
unnamed: Q3.1 (G), R2.1
unnamed: Q4.1 (G), R2.1
unnamed: Q5.1 (G), R2.1
unnamed: Q6.1 (G), R2.1
unnamed: Q7.1 (G), R2.1
unnamed: Q8.1 (G), R2.1
unnamed: Q9.1 (G), R2.1
unnamed: Q10.1 (G), R2.1
R_BUS01: J5.2, J21.a8, J21.c8
R_BUS02: J5.4, J21.a9, J21.c9
R_BUS03: J5.6, J21.a10, J21.c10
R_BUS04: J5.8, J21.a11, J21.c11
R_BUS05: J5.10, J21.a12, J21.c12
R_BUS06: J5.12, J21.a13, J21.c13
R_RS485_A: J2.2, J21.a6, J21.c6
R_RS485_B: J2.4, J21.a7, J21.c7
R_RS485_INT_A: J1.2, J21.a4, J21.c4
R_RS485_INT_B: J1.4, J21.a5, J21.c5

Notes on the sheet:
Status
Grounds
12V
PINOUT 1 GND 2 +12V 3 485 A (5V) 4 +12V 5 +12V 6 485 B (5V) 7 GND 8 GND
PINOUT 1 GND 2 +12V 3 485 INT A (5V) 4 +12V 5 +12V 6 485 INT B (5V) 7 GND 8 GND
