kiu/kha/kha-bgt-misc/kha-bgt-generic-4btn-sub/kicad/kha-bgt-generic-4btn-sub.kicad_sch

## KiCad design kha-bgt-misc/kha-bgt-generic-4btn-sub/kicad/kha-bgt-generic-4btn-sub.kicad_sch (2024-02-16)

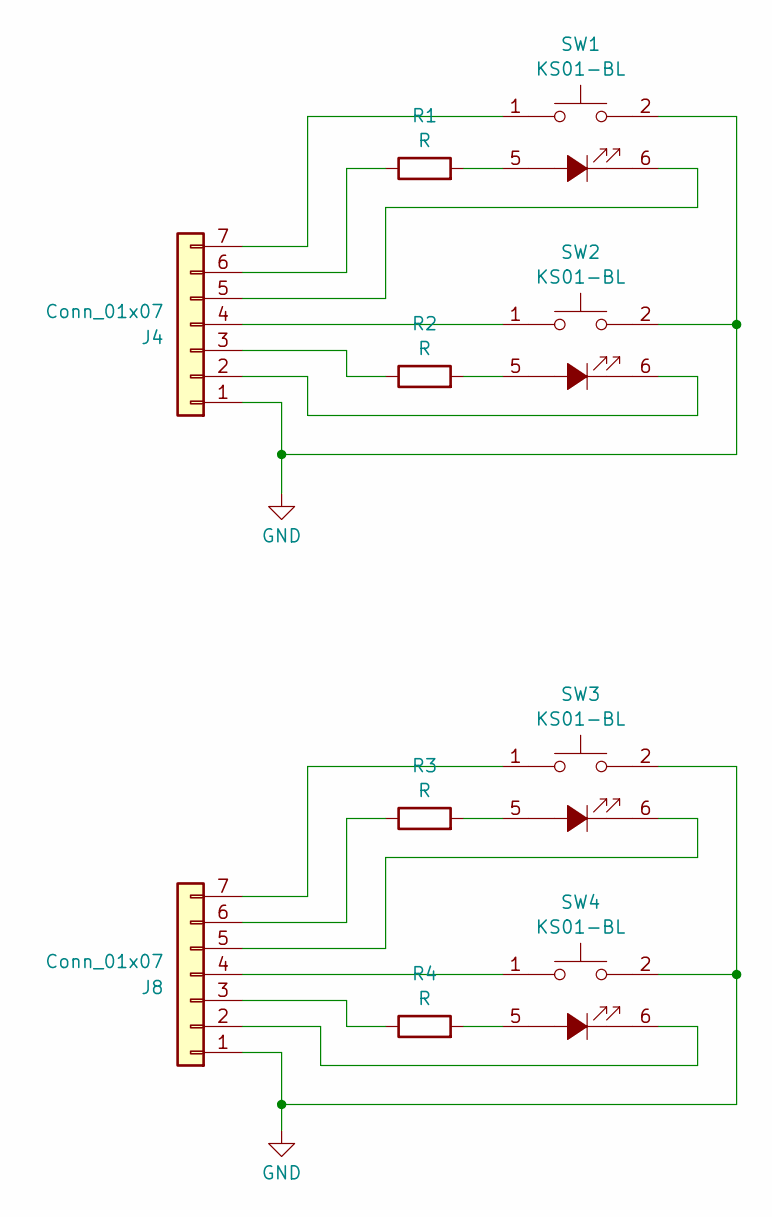
[picture p193: schematic kha-bgt-generic-4btn-sub.kicad_sch]

Parts:
J4, J8: Conn_01x07; JST_PH_B7B-PH-K_1x07_P2.00mm_Vertical
R1, R2, R3, R4: R; R_0805_2012Metric
SW1, SW2, SW3, SW4: KS01-BL

Connections:
GND: J4.1, J8.1, SW1.2, SW2.2, SW3.2, SW4.2
unnamed: J4.2, SW2.6
unnamed: J4.3, R2.1
unnamed: J4.4, SW2.1
unnamed: J4.5, SW1.6
unnamed: J4.6, R1.1
unnamed: J4.7, SW1.1
unnamed: J8.2, SW4.6
unnamed: J8.3, R4.1
unnamed: J8.4, SW4.1
unnamed: J8.5, SW3.6
unnamed: J8.6, R3.1
unnamed: J8.7, SW3.1
unnamed: R1.2, SW1.5
unnamed: R2.2, SW2.5
unnamed: R3.2, SW3.5
unnamed: R4.2, SW4.5
