kiu/kha/kha-bgt-misc/kha-bgt-generic-base/kicad/kha-bgt-generic-base.kicad_sch

## KiCad design kha-bgt-misc/kha-bgt-generic-base/kicad/kha-bgt-generic-base.kicad_sch (2024-02-16)

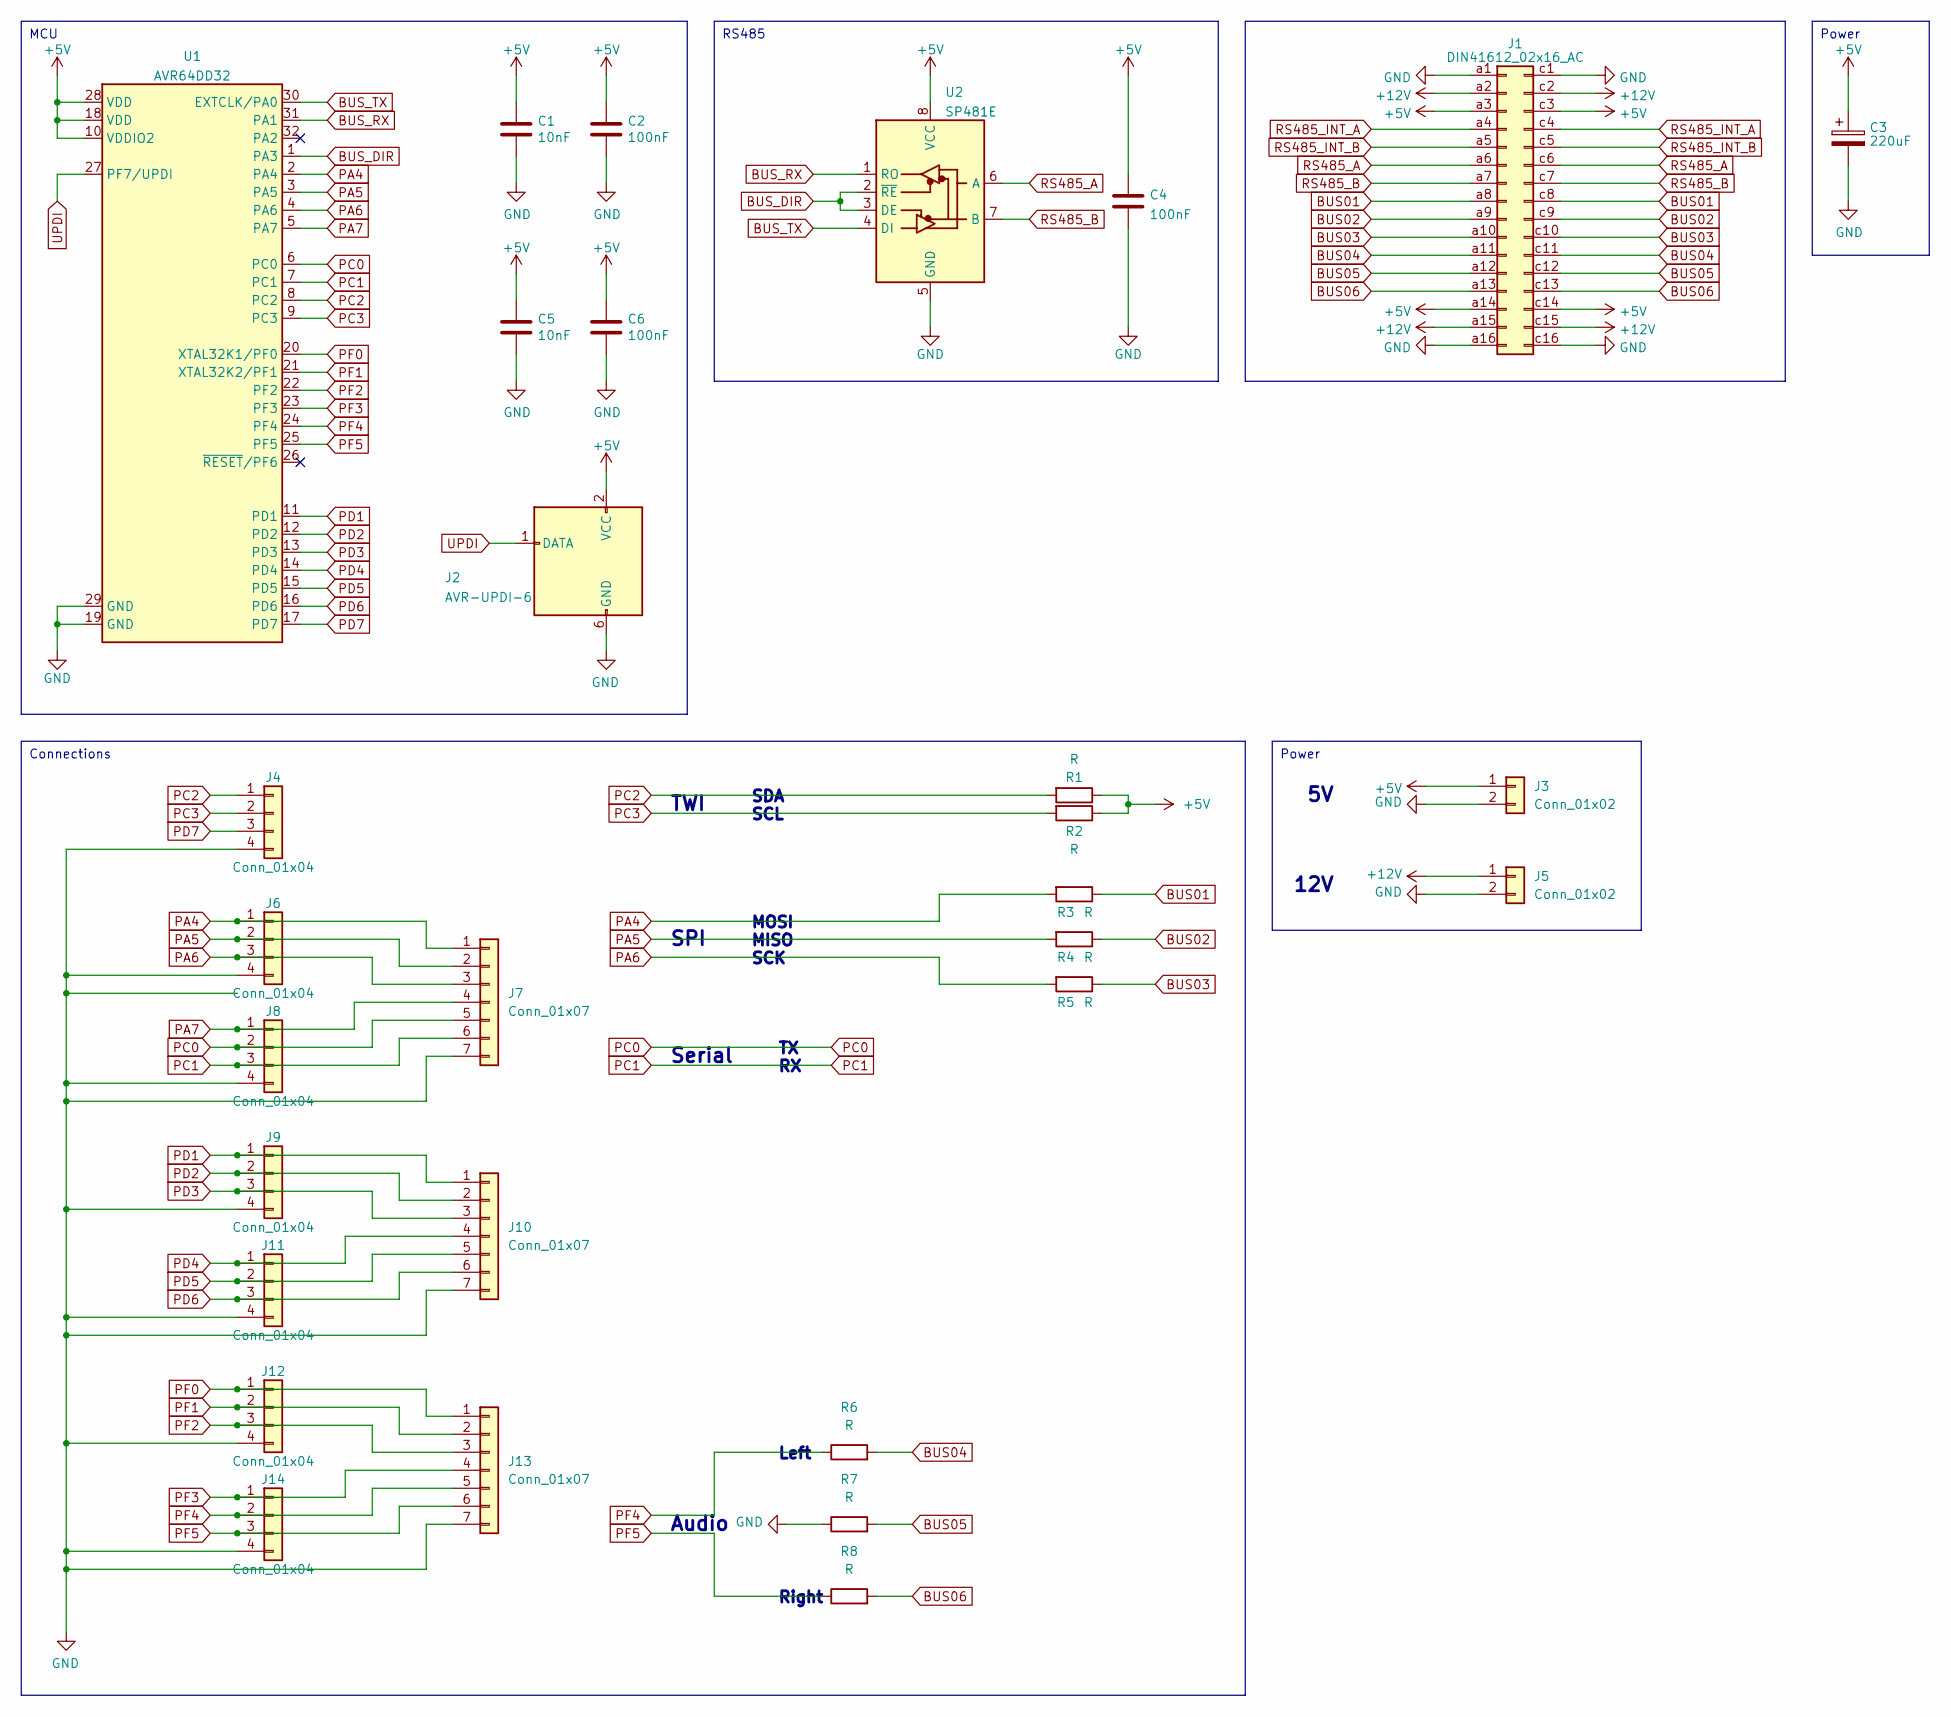
[picture p194: schematic kha-bgt-generic-base.kicad_sch]

Parts:
C1, C5: 10nF; C_0805_2012Metric
C2, C4, C6: 100nF; C_0805_2012Metric
C3: 220uF; CP_EIA-6032-28_Kemet-C
J1: DIN41612_02x16_AC; DIN41612_C2_2x16_Male_Horizontal_THT
J2: AVR-UPDI-6; eAVR6-UPDI-F
J3, J5: Conn_01x02; JST_PH_B2B-PH-K_1x02_P2.00mm_Vertical
J4, J6, J8, J9, J11, J12, J14: Conn_01x04; JST_PH_B4B-PH-K_1x04_P2.00mm_Vertical
J7, J10, J13: Conn_01x07; JST_PH_B7B-PH-K_1x07_P2.00mm_Vertical
R1, R2, R3, R4, R5, R6, R7, R8: R; R_0805_2012Metric
U1: AVR64DD32; TQFP-32_7x7mm_P0.8mm
U2: SP481E; SOIC-8_3.9x4.9mm_P1.27mm

Connections:
+5V: C1.1, C2.1, C3.1, C4.1, C5.1, C6.1, J1.a3, J1.a14, J1.c3, J1.c14, J2.2 (VCC), J3.1, R1.1, R2.1, U1.10 (VDDIO2), U1.18 (VDD), U1.28 (VDD), U2.8 (VCC)
+12V: J1.a2, J1.a15, J1.c2, J1.c15, J5.1
BUS01: J1.a8, J1.c8, R3.1
BUS02: J1.a9, J1.c9, R4.1
BUS03: J1.a10, J1.c10, R5.1
BUS04: J1.a11, J1.c11, R6.2
BUS05: J1.a12, J1.c12, R7.2
BUS06: J1.a13, J1.c13, R8.2
BUS_DIR: U1.1 (PA3), U2.2 (~RE), U2.3 (DE)
BUS_RX: U1.31 (PA1), U2.1 (RO)
BUS_TX: U1.30 (EXTCLK/PA0), U2.4 (DI)
GND: C1.2, C2.2, C3.2, C4.2, C5.2, C6.2, J1.a1, J1.a16, J1.c1, J1.c16, J2.6 (GND), J3.2, J4.4, J5.2, J6.4, J7.7, J8.4, J9.4, J10.7, J11.4, J12.4, J13.7, J14.4, R7.1, U1.19 (GND), U1.29 (GND), U2.5 (GND)
PA4: J6.1, J7.1, R3.2, U1.2 (PA4)
PA5: J6.2, J7.2, R4.2, U1.3 (PA5)
PA6: J6.3, J7.3, R5.2, U1.4 (PA6)
PA7: J7.4, J8.1, U1.5 (PA7)
PC0: J7.5, J8.2, U1.6 (PC0)
PC1: J7.6, J8.3, U1.7 (PC1)
PC2: J4.1, R1.2, U1.8 (PC2)
PC3: J4.2, R2.2, U1.9 (PC3)
PD1: J9.1, J10.1, U1.11 (PD1)
PD2: J9.2, J10.2, U1.12 (PD2)
PD3: J9.3, J10.3, U1.13 (PD3)
PD4: J10.4, J11.1, U1.14 (PD4)
PD5: J10.5, J11.2, U1.15 (PD5)
PD6: J10.6, J11.3, U1.16 (PD6)
PD7: J4.3, U1.17 (PD7)
PF0: J12.1, J13.1, U1.20 (XTAL32K1/PF0)
PF1: J12.2, J13.2, U1.21 (XTAL32K2/PF1)
PF2: J12.3, J13.3, U1.22 (PF2)
PF3: J13.4, J14.1, U1.23 (PF3)
PF4: J13.5, J14.2, R6.1, U1.24 (PF4)
PF5: J13.6, J14.3, R8.1, U1.25 (PF5)
RS485_A: J1.a6, J1.c6, U2.6 (A)
RS485_B: J1.a7, J1.c7, U2.7 (B)
RS485_INT_A: J1.a4, J1.c4
RS485_INT_B: J1.a5, J1.c5
UPDI: J2.1 (DATA), U1.27 (PF7/UPDI)

Notes on the sheet:
Connections
Power
RS485
MCU
SDA
Right
TWI
MISO
SCL
Serial
Audio
SPI
12V
SCK
Left
MOSI
