kiu/kha/kha-bgt-misc/kha-bgt-generic-rotary-encoder/kicad/kha-bgt-generic-rotary-encoder.kicad_sch

## KiCad design kha-bgt-misc/kha-bgt-generic-rotary-encoder/kicad/kha-bgt-generic-rotary-encoder.kicad_sch (2024-02-16)

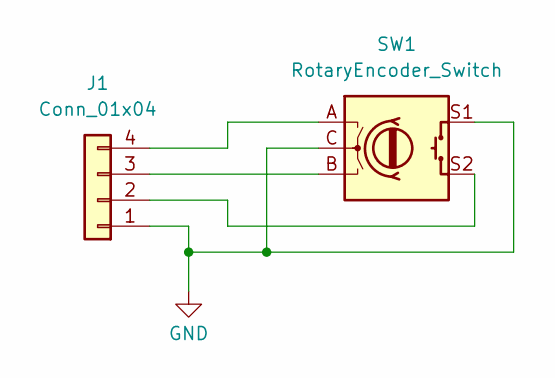
[picture p195: schematic kha-bgt-generic-rotary-encoder.kicad_sch]

Parts:
J1: Conn_01x04; JST_PH_B4B-PH-K_1x04_P2.00mm_Vertical
SW1: RotaryEncoder_Switch; RotaryEncoder_Alps_EC11E-Switch_Vertical_H20mm

Connections:
GND: J1.1, SW1.C, SW1.S1
unnamed: J1.2, SW1.S2
unnamed: J1.3, SW1.B
unnamed: J1.4, SW1.A
