kiu/kha/kha-bgt-misc/kha-bgt-pwr/kicad/kha-bgt-pwr.kicad_sch

## KiCad design kha-bgt-misc/kha-bgt-pwr/kicad/kha-bgt-pwr.kicad_sch (2024-02-16)

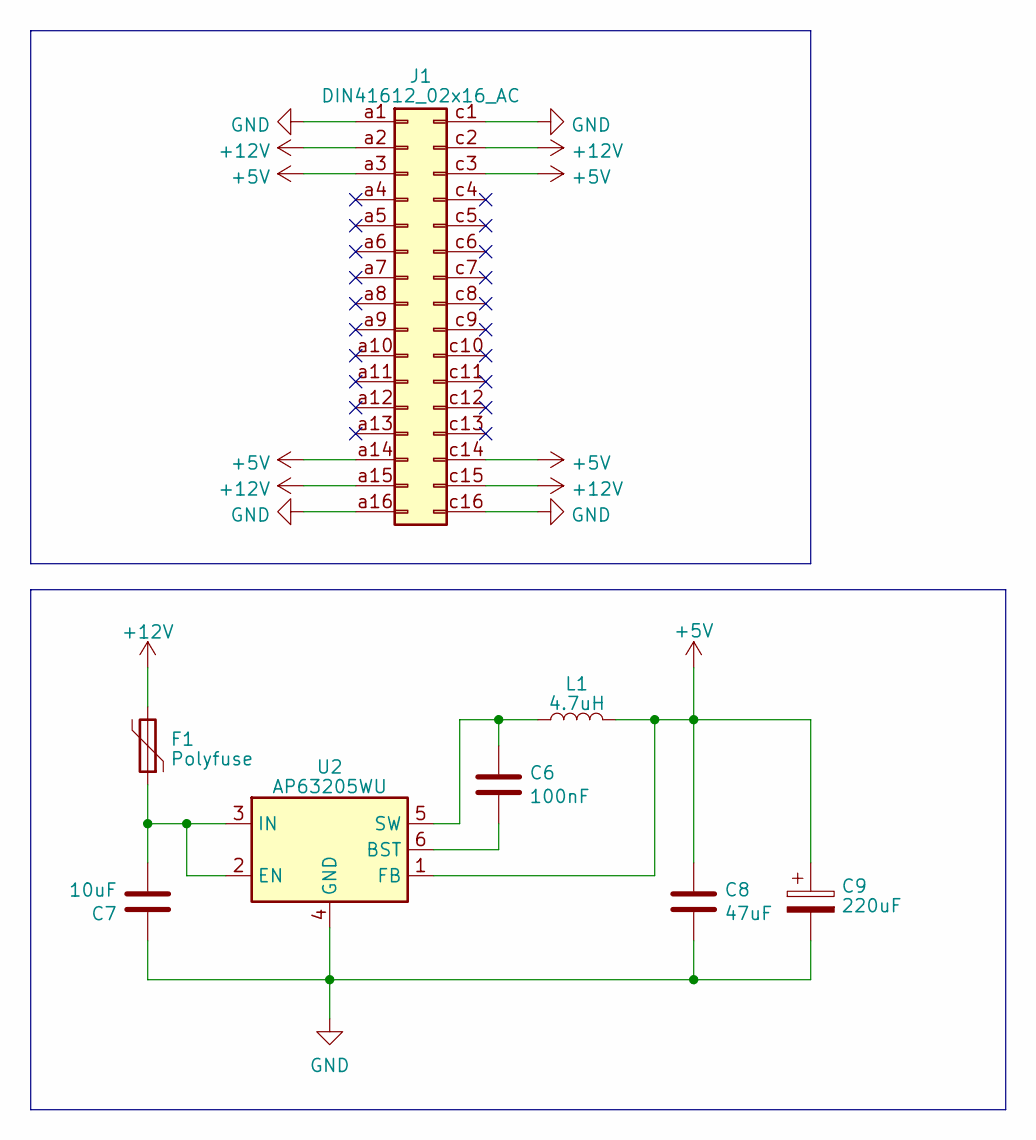
[picture p196: schematic kha-bgt-pwr.kicad_sch]

Parts:
C6: 100nF; C_0805_2012Metric
C7: 10uF; C_0805_2012Metric
C8: 47uF; C_1210_3225Metric
C9: 220uF; CP_EIA-6032-28_Kemet-C
F1: Polyfuse; Fuse_0805_2012Metric
J1: DIN41612_02x16_AC; DIN41612_C2_2x16_Male_Horizontal_THT
L1: 4.7uH; L_1210_3225Metric
U2: AP63205WU; TSOT-23-6

Connections:
+5V: C8.1, C9.1, J1.a3, J1.a14, J1.c3, J1.c14, L1.2, U2.1 (FB)
+12V: F1.2, J1.a2, J1.a15, J1.c2, J1.c15
GND: C7.1, C8.2, C9.2, J1.a1, J1.a16, J1.c1, J1.c16, U2.4 (GND)
unnamed: C6.1, L1.1, U2.5 (SW)
unnamed: C6.2, U2.6 (BST)
unnamed: C7.2, F1.1, U2.2 (EN), U2.3 (IN)
