kiu/kha/kha-bgt-misc/kha-bgt-template/kicad/kha-bgt-template.kicad_sch

## KiCad design kha-bgt-misc/kha-bgt-template/kicad/kha-bgt-template.kicad_sch (2024-02-09)

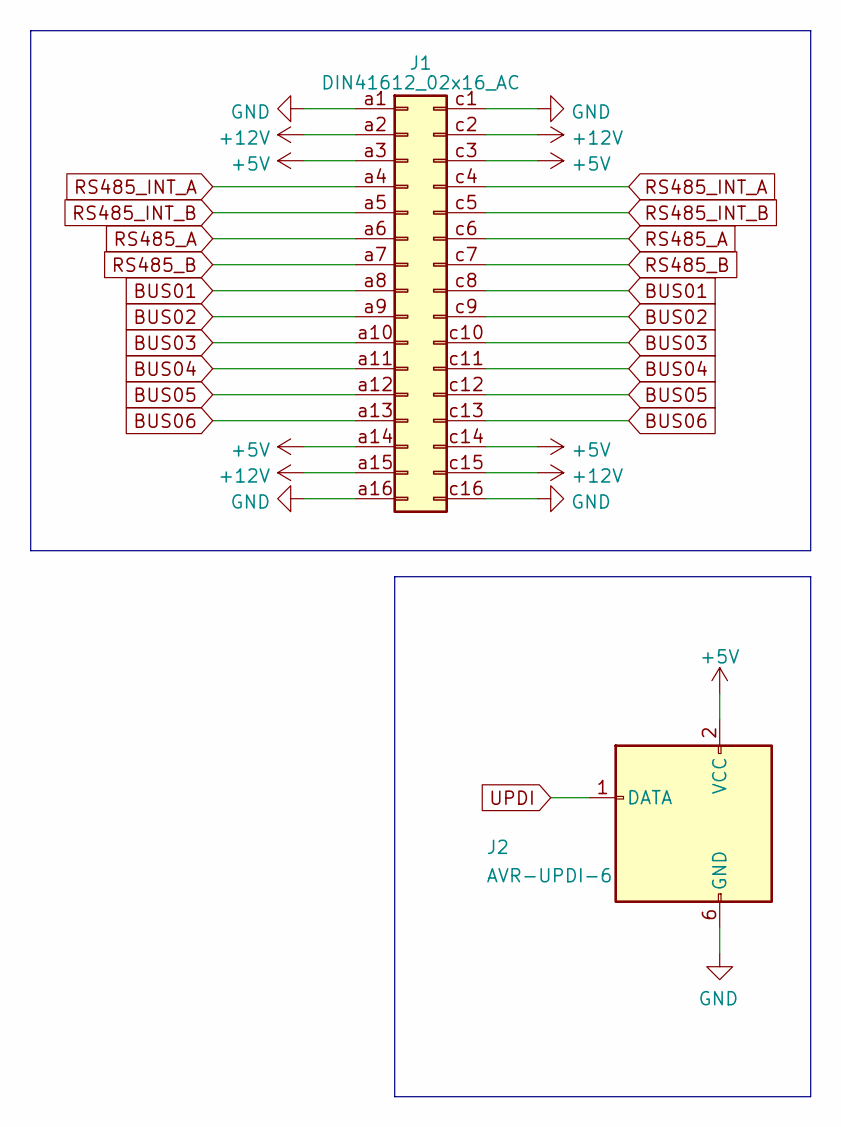
[picture p197: schematic kha-bgt-template.kicad_sch]

Parts:
J1: DIN41612_02x16_AC; DIN41612_C2_2x16_Male_Horizontal_THT
J2: AVR-UPDI-6; eAVR6-UPDI-B

Connections:
+5V: J1.a3, J1.a14, J1.c3, J1.c14, J2.2 (VCC)
+12V: J1.a2, J1.a15, J1.c2, J1.c15
BUS01: J1.a8, J1.c8
BUS02: J1.a9, J1.c9
BUS03: J1.a10, J1.c10
BUS04: J1.a11, J1.c11
BUS05: J1.a12, J1.c12
BUS06: J1.a13, J1.c13
GND: J1.a1, J1.a16, J1.c1, J1.c16, J2.6 (GND)
RS485_A: J1.a6, J1.c6
RS485_B: J1.a7, J1.c7
RS485_INT_A: J1.a4, J1.c4
RS485_INT_B: J1.a5, J1.c5
UPDI: J2.1 (DATA)
