kiu/kha/kha-nodes/kha-led-strip/kha-led-strip.X/main.h

/* 
 * File:   main.h
 * Author: kiu
 *
 * Created on March 21, 2024, 11:24 PM
 */

#ifndef MAIN_H
#define	MAIN_H

#ifdef	__cplusplus
extern "C" {
#endif

#define STRIP_ADDR_CFG_LEDS 0x01
#define STRIP_ADDR_CFG_COMM 0x02
#define STRIP_ADDR_CFG_INTENSITY_MAX 0x03
    
#ifdef	__cplusplus
}
#endif

#endif	/* MAIN_H */
