kiu/kha/kha-bgt-subrack/kha-bgt-audio/kha-bgt-audio.X/main.h

/* 
 * File:   main.h
 * Author: kiu
 *
 * Created on November 10, 2023, 9:38 PM
 */

#ifndef MAIN_H
#define	MAIN_H

#ifdef	__cplusplus
extern "C" {
#endif

typedef enum {AUXA, AUXB, AUXC, AUXD, NONE} opmode;

#ifdef	__cplusplus
}
#endif

#endif	/* MAIN_H */
